alvinr/tbs/fp-corner-blueprint-spec.md

<!-- SPDX-License-Identifier: AGPL-3.0-only -->
<!-- © 2026 Alvin Richards -->
<!-- Design spec / scope — NOT a published TBS artifact (not registered in publish.sh). -->

# Film-Plane Corner Mechanism — Definitive Blueprint Spec

**Status:** scoped, awaiting sign-off before implementation.
**Purpose:** upgrade ONE film-plane corner from arrangement-schematic to a **dimensionally-exact,
fabricator-ready** drawing — the **template** for rolling the same standard across every subsystem
(water/tray, IBC frame, walkway, hinged panel, light lock, electrical, optics).

## Locked decisions (2026-08-10)

1. **Upgrade the existing corner sheets 3/4/8/9 in place** (in `generate_film_plane_mechanism.py`)
   + add a new **guide-corner sheet**. No separate generator.
2. **Cover both corners**: bottom = **weight** corner (rail web-vertical, skate load-bearing);
   top = **guide** corner (rail flat, skate as guide only) — the mirror pair.
3. **304 stainless** for the cross-slide bar + skate axle (procurement BOM is source of record; the
   cyanotype wash is chloride-free). Fix the stale **316** references.

## Design of record (one corner)

| Element | Spec | Finish |
|---|---|---|
| Depth rail | 3×1½" (76×38) **6061-T6 Al U-channel**, 8 ft (Grainger 795M51) | mill |
| Carriage | 4-wheel **acetal skate** — Ø32 load + Ø20 keeper rollers on Ø10 **304** axles + fab carriage plate | — |
| Cam clamp | 3/corner McMaster **5128A63** low-profile hold-down toggle | zinc |
| Z + X cross-slide | **304** flat-bar ¼"×1½" (6.35×38.1) on UHMW pad + brass-tip gib | — |
| U-joint | **Belden SSNBUJ750x3/8KB** (Grainger 41D816; 3/8" keyway bore + set screw, 0.75" OD, 45°, needle-bearing, factory-booted); input stub in McMaster **4040N12** 304 shaft support; keyed 3/8" 304 stub | stainless |
| Corner plate | ¼" **304 SS** 6×8" blank, press-brake **L-bracket** | 304 |
| Frame angle | 2×2×⅛" **6061-Al** angle, welded rigid rectangle 4,389×2,094 | mill |

_(The TODO's "Ruland US12-6-6-SS" is stale — the U-joint was changed to Belden. "Wheels/trolley on
316 pipe" is a superseded concept — the built design is the U-channel + acetal skate.)_

## Phase 1 — Reconcile + parametrize (precondition; no drawing yet)

**1a. Resolve conflicts (drift sweep):**
- Cross-slide bar + skate axle **316 → 304** in: `film-plane-mechanism-report.md` §4, `generate_film_plane_mechanism.py` Sheet-8 note, `component-dependency-map.md` §3.1/§1.3 and the FPM note.
- Rail **material** in depmap "304 U-channel" → **6061-Al**; rail **supplier** stale "McMaster 1262T21" → **Grainger 795M51** (depmap §1.3 + 2D generator comment).
- Rail **scheme**: adopt the 3D model's **two-orientation** build as the design of record (bottom web-vertical weight / top flat guide); fix the report/parts "uniform, one skate rides inside each" wording; drop stale "4×2" / "V-trolley" / "trolley" comments in constants + model.

**1b. Promote/add constants to `tbs_constants.py`** (so the drawing is parametric, can't drift):
- Promote `XSLIDE_Z_TRAVEL` / `XSLIDE_X_TRAVEL` / `XSLIDE_STROKE` / `XSLIDE_N` from **`reserved` → firm**. **FIRM (2026-08-13):** travel verified vs geometry on Sheet 10 — Z = (FP_H/2)(1−cos 40°) = 245 mm, X = (FP_W/2)(1−cos 28°) = 257 mm (exact match).
- **New:** `XSLIDE_BAR_W=38.1`, `XSLIDE_BAR_T=6.35` (cross-slide bar section); `XSLIDE_UHMW_T`, `XSLIDE_GIB_*`.
- **New:** `UJOINT_BORE=9.53`, `UJOINT_OD=19.05`, `UJOINT_ANGLE=45`, `UJOINT_LEN` (from the Belden datasheet).
- **New:** `SKATE_ROLLER_OD=32`, `SKATE_KEEPER_OD=20`, `SKATE_AXLE_OD=10`, skate roller spacing / carriage-plate W×H×T.
- **New:** `CORNER_PLATE_W=203.2`, `CORNER_PLATE_H=152.4`, `CORNER_PLATE_T=6.35`, bend line + leg lengths.
- **New:** hole **PCDs / edge distances** — see Phase 2 (designed, then captured as constants).

**1c. Firm the load — DONE (2026-08-13; `fp_corner_load.py` → Sheet 10).** Per-corner load = W/4 = **124 N**
(moving mass ~51 kg, weight model). Governing case = the horizontal X (swing) slide in bending at full
257 mm extension (the Z slide takes gravity axially, so it doesn't bend). **DECISION: the
cross-slide bars are mounted DEEP** — the 38.1 mm dimension in the load direction — giving σ ≈ 21 MPa,
**SF ≈ 10**, δ ≈ 0.1 mm. Flat mounting is marginal (SF ≈ 1.7, fails under a 2× dynamic/asymmetry factor)
and is NOT used. See Sheet 10 (`film-plane-sheet10.png`).

## Phase 2 — Dimensioned drawing upgrades

**Hole positions** — take fixed patterns from datasheets (4040N12 shaft support, 5128A63 cam-clamp
base, U-joint bore); **design** the patterns on our fab plates (carriage plate, L-plate, cross-slide
mounts) to ≥2×Ø edge distance, then capture all as constants (Phase 1b).

- **Sheet 3** (corner carriage detail) → add hole PCDs + edge distances for the skate rollers/axles,
  carriage plate, and U-channel capture; add datum flags; dimension roller spacing.
- **Sheet 4** (rail mounting + transport drop-in) → dimension the rail-end mount, the transport
  drop-in bridge, and the right-flange bolt pattern (PCD/edge distance).
- **Sheet 8** (frame-corner ↔ cross-slide + J1–J5) → dimension the cross-slide **bar section + travel
  + gib/UHMW**; complete J1–J5 (below).
- **Sheet 9** (frame + ACM ↔ U-joint ↔ X-slide) → make it a **dimensioned fabrication section**;
  add the **U-joint envelope** and the **L-plate bend** (bend line, radius, leg lengths, PCDs).
- **NEW Sheet 10** (guide/top corner) → the mirror: rail laid flat, skate as guide (no load path),
  same cross-slide/U-joint stack — call out only the **deltas** from the weight corner.

## Phase 3 — Fastener schedule (complete J1–J5)

Existing J1–J5 (Sheet 8) carry size/thread only. Add per joint: **thread pitch + class**, **torque**
(from the fastener's proof load), **washer** (flat/split), and **thread-locker** (Loctite grade) callout.
- J1/J2 = M8 (carriage/plate); J3 = 3/8" stub → U-joint (key + clamp); J4 = shaft-support setscrew;
  J5 = M6 legs tapped into the frame angle. Verify each against its datasheet.

## Phase 4 — Datum + tolerance scheme

Establish a datum reference frame for the corner (e.g. **A** = frame-angle mounting face, **B** = rail
web, **C** = optical axis) and apply position/parallelism tolerances to the critical features
(cross-slide travel squareness, U-joint bore concentricity, rail capture). Add a title-block tolerance
block (general ±, then per-feature GD&T where it matters).

## Phase 5 — Cascade + close

- Reconcile `parts.py` / `costing.py` / report §7 / master BOM to any spec change (304 confirm = no
  cost move; new constants = no cost move).
- Re-send the `film-plane-mechanism.skp` model so its (currently hardcoded) corner geometry reads the
  new constants; reconcile depmap §3.1.
- Run the gates (`lint.py`, `check_consistency.py`), gallery + registration for the new Sheet 10.
- Tick the milestone sub-items in `TODO.md`; RELEASE `[Unreleased]`.

## Acceptance criteria

A fabricator can build one weight corner **and** one guide corner from Sheets 3/4/8/9/10 alone:
every hole located (PCD/edge distance), every fastener called out (size/thread/torque/locker), every
part's material + finish stated, sections dimensioned, and a datum/tolerance scheme present — all driven
from `tbs_constants` with **zero** `reserved`/prose-only corner dimensions remaining.

## Guide (top) corner — web-vertical decision + FP_H reconciliation (VERIFIED 2026-08-10)

**Decision:** the top (guide) corner uses the **same web-vertical rail + captured skate** as
the bottom (weight) corner — NOT the flat "inverted-U, wheels-under-web" build the 3D model currently
has. Rationale: the wheels-under-web build is unsound (gravity drops the hanging carriage away from the
rollers); a captured skate on a web-vertical rail holds the corner regardless of load direction (it
reacts the plane's tip-force, not gravity). The transport swing does not constrain this — the left rails
are transport drop-ins (removed for the ~56° swing; door clearance `SWUNG_DOOR_CLEARANCE_MM`=29mm is
unaffected).

**The old Sheet 10 was reverted** (commit on this branch): its wheels-under-web section was wrong and it
added nothing over Sheet 3 but a deltas note.

**FP_H reconciliation — the key result: NO `FP_H` change, NO headline cascade.** The flat top rail was
letting the 3D model draw the film ~36 mm *taller* than the official constant ever claimed — a latent
inconsistency. Web-vertical corrects the model *down to* the constant. Verified against the LIVE model
(`film-plane-mechanism.skp`, read-only eval), all mm:

| | film bottom | film top | FP height | top rail Z |
|---|---|---|---|---|
| **Constant** (`FP_H`) | 160 | 2254 | **2094** | — |
| **Model, flat top (now)** | 160 | **2290** | 2130 (outlier, +36) | 2300–2338 (38 tall, 50 below ceiling) |
| **Model, web-vertical** | 160 | **2252** | **2092** (≈ FP_H, −2) | 2262–2338 (76 tall, 50 below ceiling) |

Web-vertical film top = `C_HGT(2388) − rail(76) − ceiling_clear(50) − guide_gap(10) = 2252`; FP =
2252 − 160 = **2092 ≈ FP_H 2094** (2 mm, within rounding). So `FP_H` stays **2094**, `RAIL_OFF_TOP`
stays **144** — the model was the thing out of sync; web-vertical fixes it. (A separate ~10 mm internal
slack exists between `RAIL_OFF_TOP`→2244 and `FP_H`→2254; optional future cleanup, independent of this.)

**What the switch takes (no FP_H/optics/image-area/facts/CLAUDE.md churn):**
1. **3D model** `generate_film_plane_mechanism_model.py` — top rail flat→web-vertical (`CD_TOP/CW_TOP`
   orientation, `PZ_HB_TOP`, `GUIDE_GAP`, `guide_rail()` builder); the top skate becomes the SAME captured
   skate as the bottom; film top drops 2290→2252. Regenerate + **re-send** (needs the .skp open) + ALVIN saves.
2. **Docs/comments** — "top laid FLAT / inverted-U / wheels under web" → "top web-vertical, captured guide
   skate (rollers grip both flanges; reacts tip-force, not gravity)" in `component-dependency-map.md`,
   `film-plane-mechanism-report.md`, and the model comments.
3. **2D** — the guide-corner coverage folds into Sheet 3 as a captured-skate note (not a separate Sheet 10).
4. **No** `FP_H` change (verified), so no cascade to facts/optics/ACM/muslin/weight/CLAUDE.md.

## Open items to settle during design

- ~~Exact travel values for the promoted `XSLIDE_*`~~ **DONE 2026-08-13** — verified vs geometry (Sheet 10): Z 245 / X 257 mm.
- ~~Belden U-joint booted length + bolt/key detail~~ **DONE 2026-08-13.** Reviewed the plain `UJ-SS750x375` datasheet (`eng-specs/UJ-SS750x375__ZE41.pdf`) — OD 19.05 / length 68.3 / yoke 34.2 / hub 24.1 / 45° confirmed — but it has no keyway/set-screw, so **selected the retained variant: Belden SSNBUJ750x3/8KB (Grainger 41D816, $252.13 ea)** — 3/8″ **keyway bore (3/32×3/64 key) + set screw**, needle-bearing, stainless, 45° max, and **factory-booted** (integral bellows `UJOINT_BOOT_OD` 32.54 / `UJOINT_BOOT_LEN` 31.75 — no separate boot). Cascaded to constants / parts (fp-ujoint + fp-ujoint-key, boot line dropped) / costing (+~$403) / Sheets 3·8·9 / report. (3D model label re-send pending.)
- ~~Carriage-plate hole pattern~~ **DONE 2026-08-13** — plate firmed at **80×181×6mm 6061-T6** (`CARRIAGE_PLATE_*`, grown +10 for keeper edge distance); pattern **4× Ø10 stub-axle (40×38) + 4× M8 J1 + 2× M4 cam**, all ≥2×Ø from edges; drawn on Sheet 3 View A + firmed in `parts.py` fp-carriage-plate. (L-plate/corner-plate pattern already in `CORNER_PLATE_HOLE_*`.)
- ~~Per-corner load + cross-slide bending SF~~ **DONE 2026-08-13** (Sheet 10): 124 N/corner; bars mounted **DEEP** → SF ≈ 10 (flat 1.7, not used).
