alvinr/tbs/diagrams/container-floorplan.png

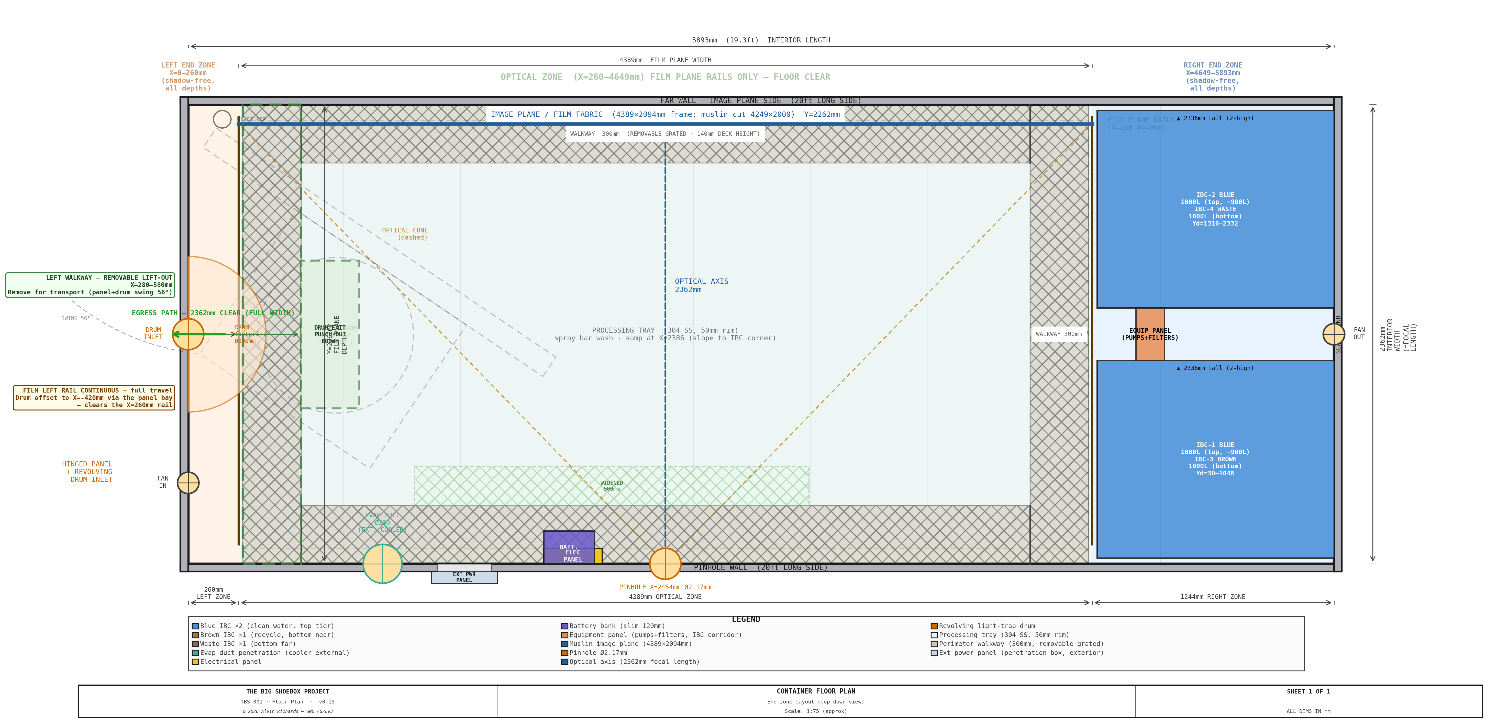
diagrams/container-floorplan.png
