alvinr/tbs/diagrams/electrical-sheet1.png

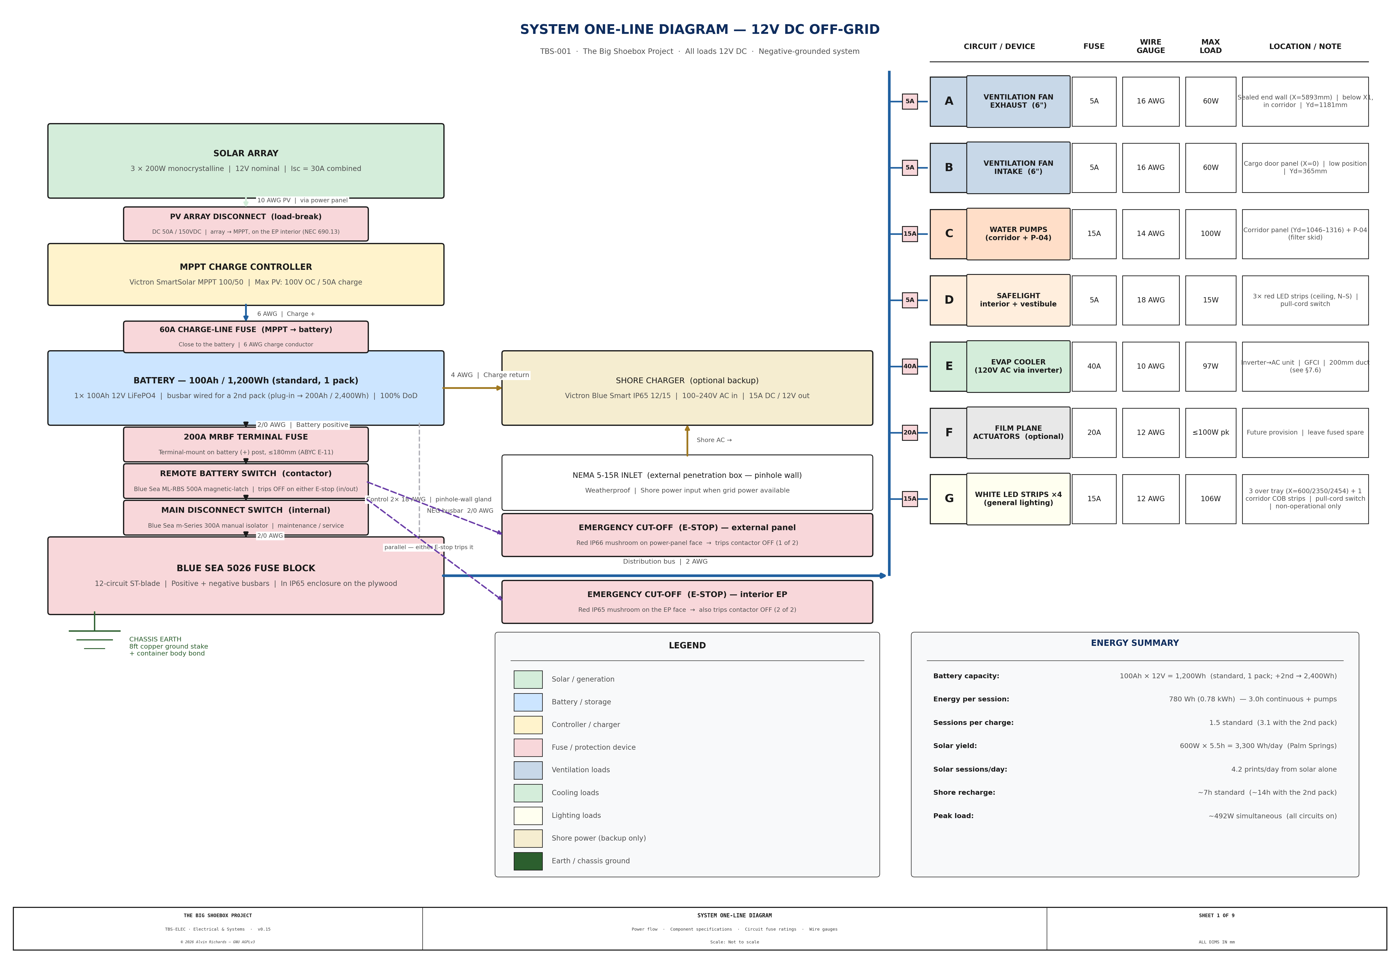
diagrams/electrical-sheet1.png
