alvinr/tbs/diagrams/electrical-sheet2.png

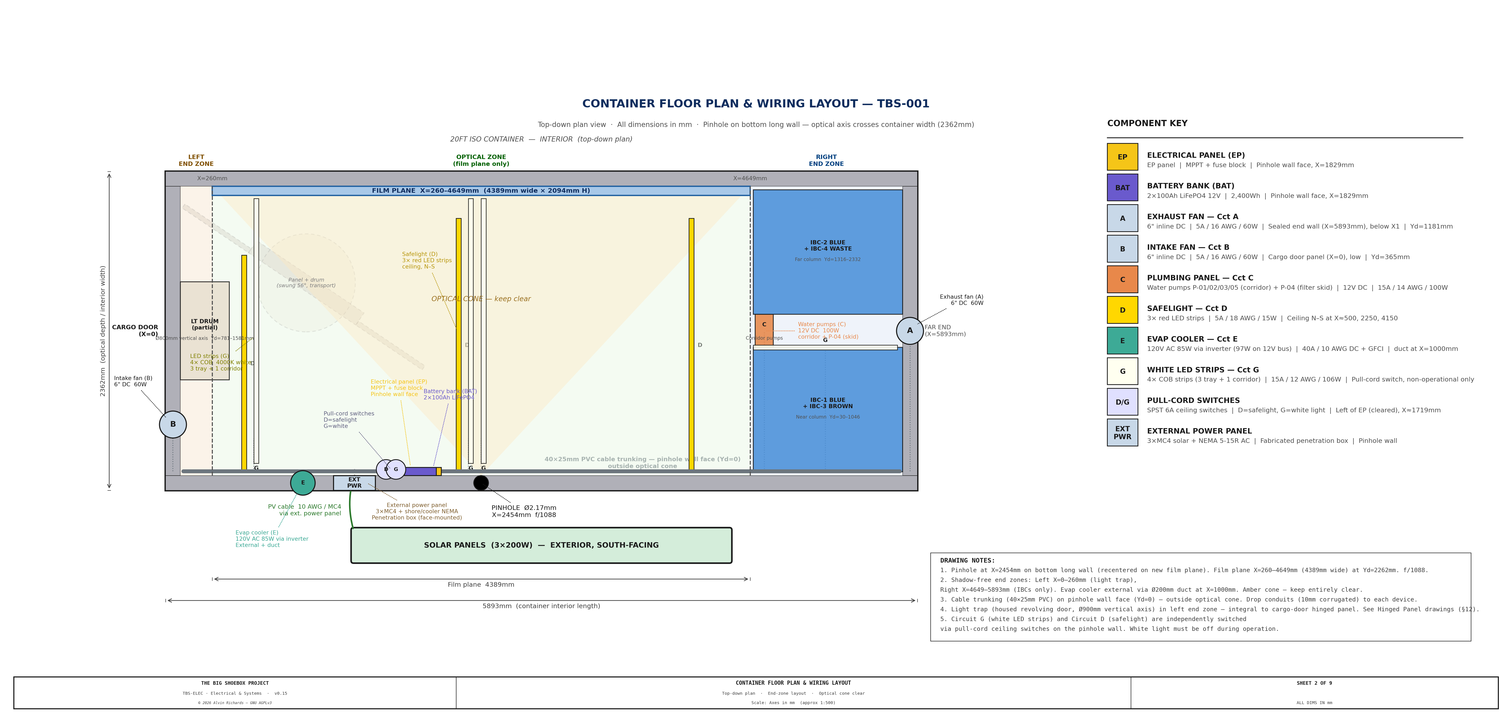
diagrams/electrical-sheet2.png
