alvinr/tbs/diagrams/film-joint-options.png

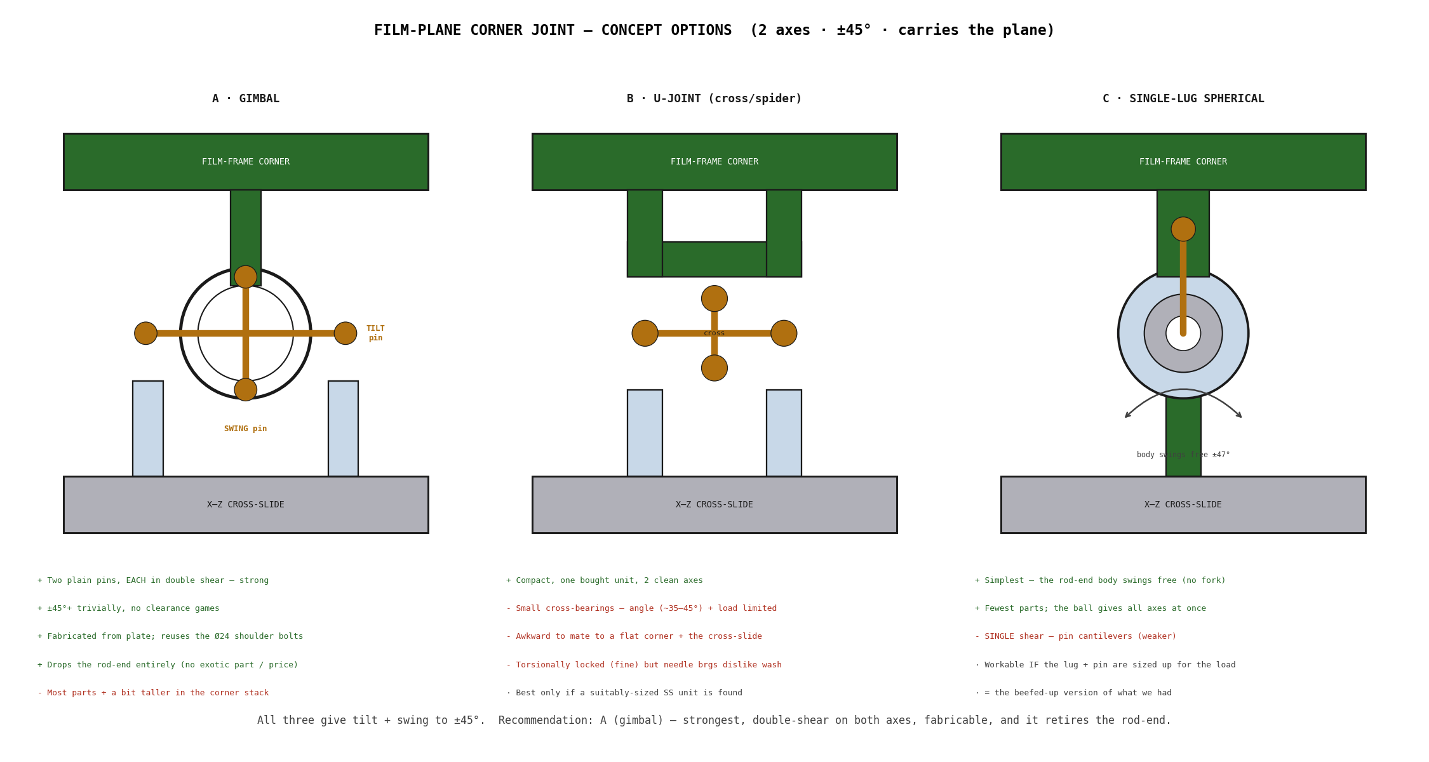
diagrams/film-joint-options.png
