alvinr/tbs/diagrams/film-joint-study-gimbal.png

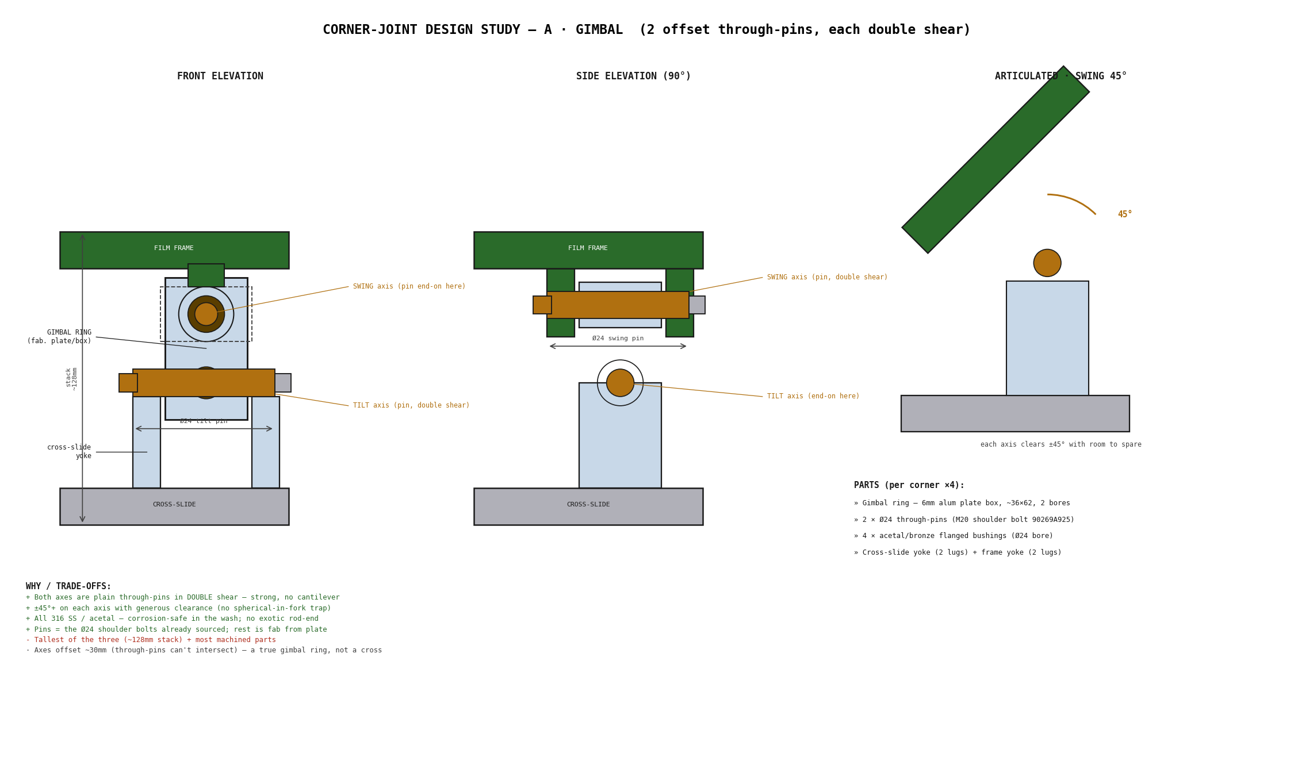
diagrams/film-joint-study-gimbal.png
