alvinr/tbs/diagrams/film-joint-study-ujoint.png

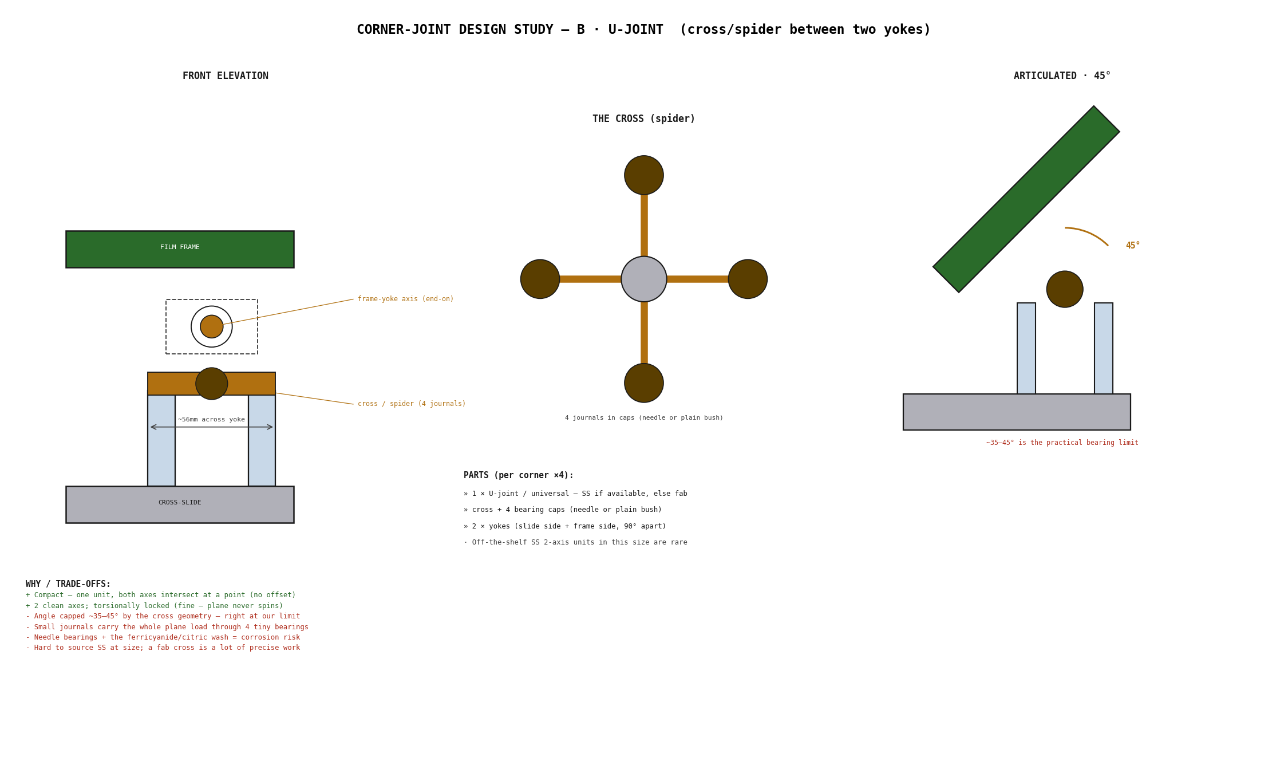
diagrams/film-joint-study-ujoint.png
