alvinr/tbs/diagrams/film-plane-distortion-c0.png

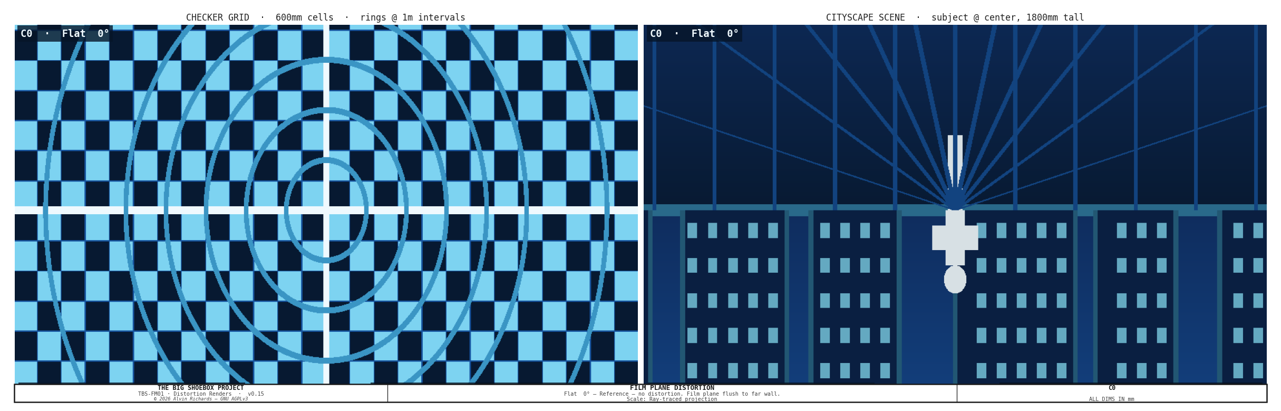
diagrams/film-plane-distortion-c0.png
