alvinr/tbs/diagrams/film-plane-distortion-c2.png

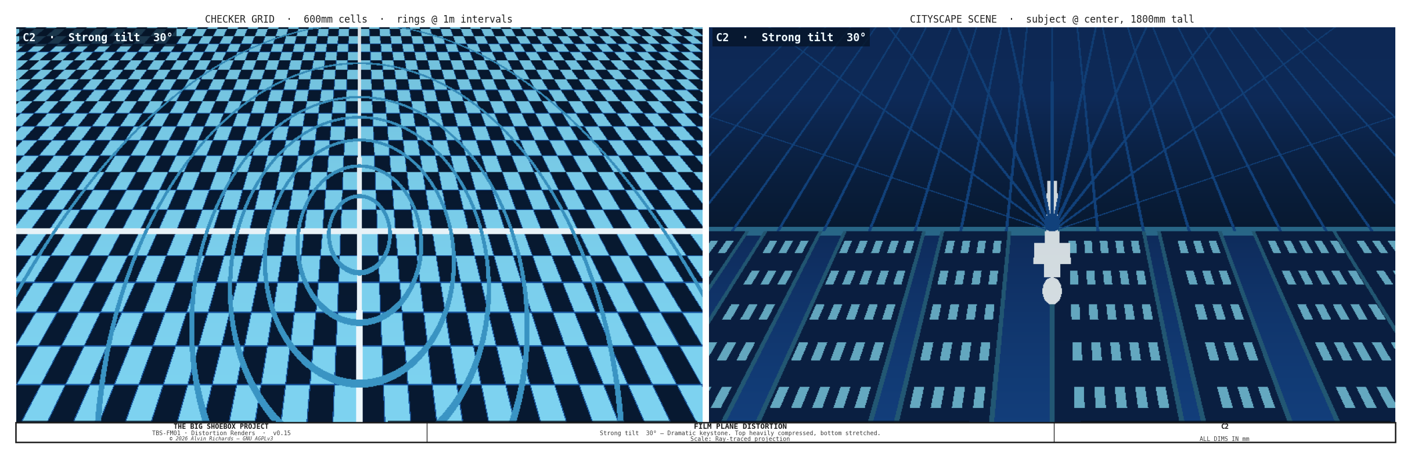
diagrams/film-plane-distortion-c2.png
