alvinr/tbs/diagrams/film-plane-distortion-c3.png

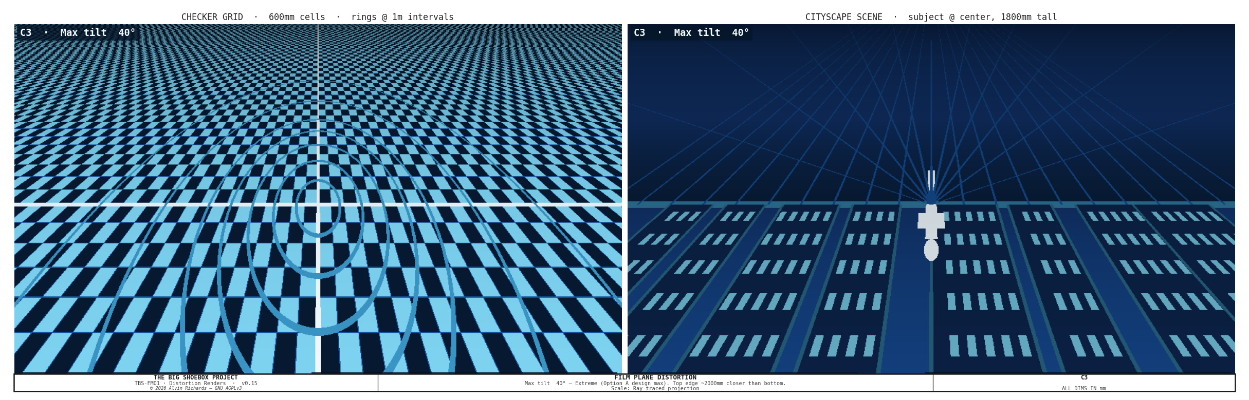
diagrams/film-plane-distortion-c3.png
