alvinr/tbs/diagrams/film-plane-distortion-c4.png

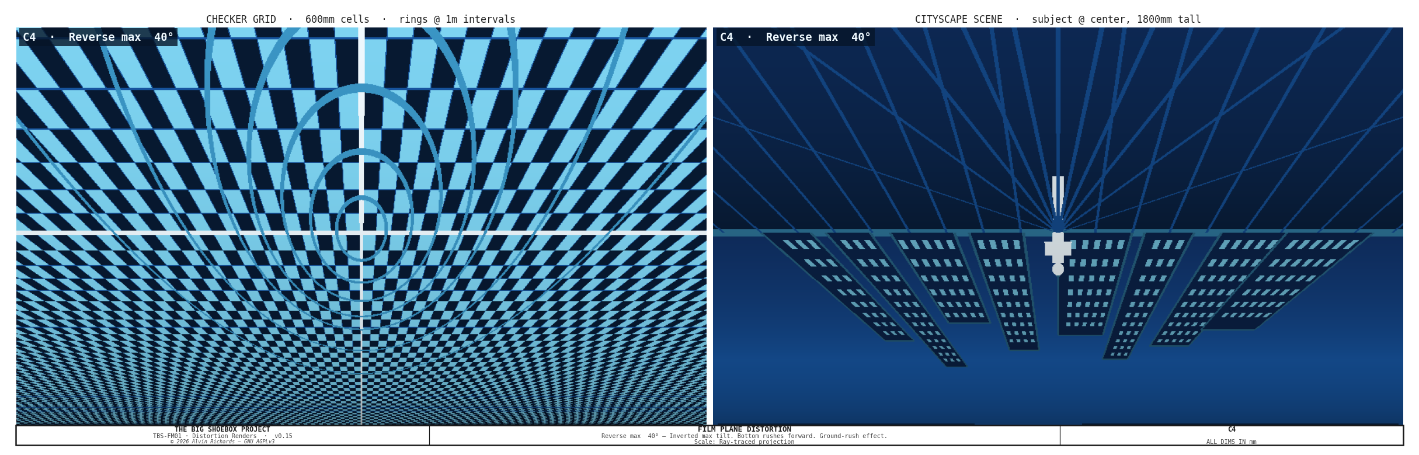
diagrams/film-plane-distortion-c4.png
