alvinr/tbs/diagrams/film-plane-distortion-c5.png

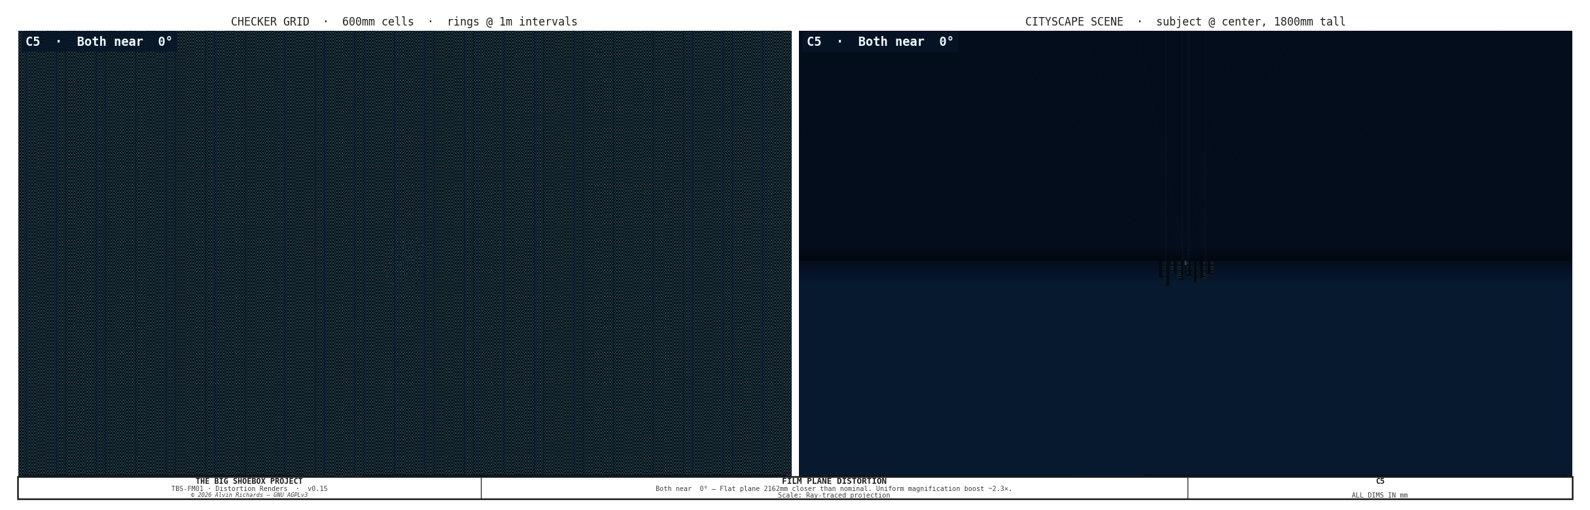
diagrams/film-plane-distortion-c5.png
