alvinr/tbs/diagrams/film-plane-distortion-summary.png

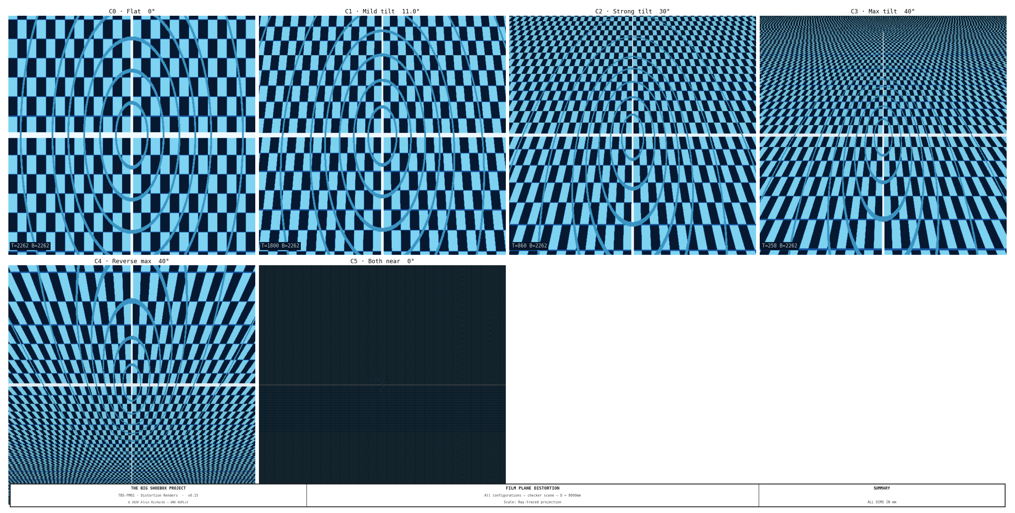
diagrams/film-plane-distortion-summary.png
