alvinr/tbs/diagrams/film-plane-sheet1.png

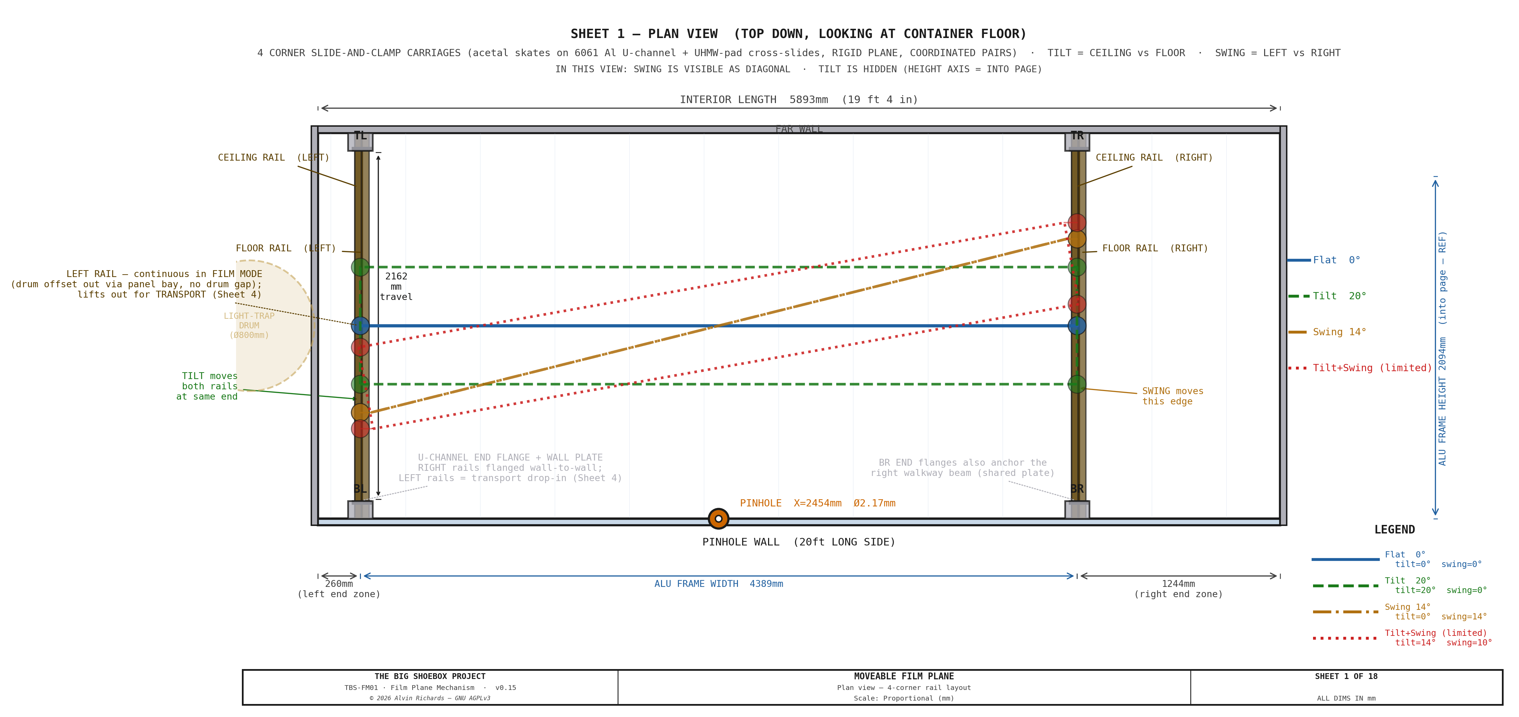
diagrams/film-plane-sheet1.png
