alvinr/tbs/diagrams/film-plane-sheet2.png

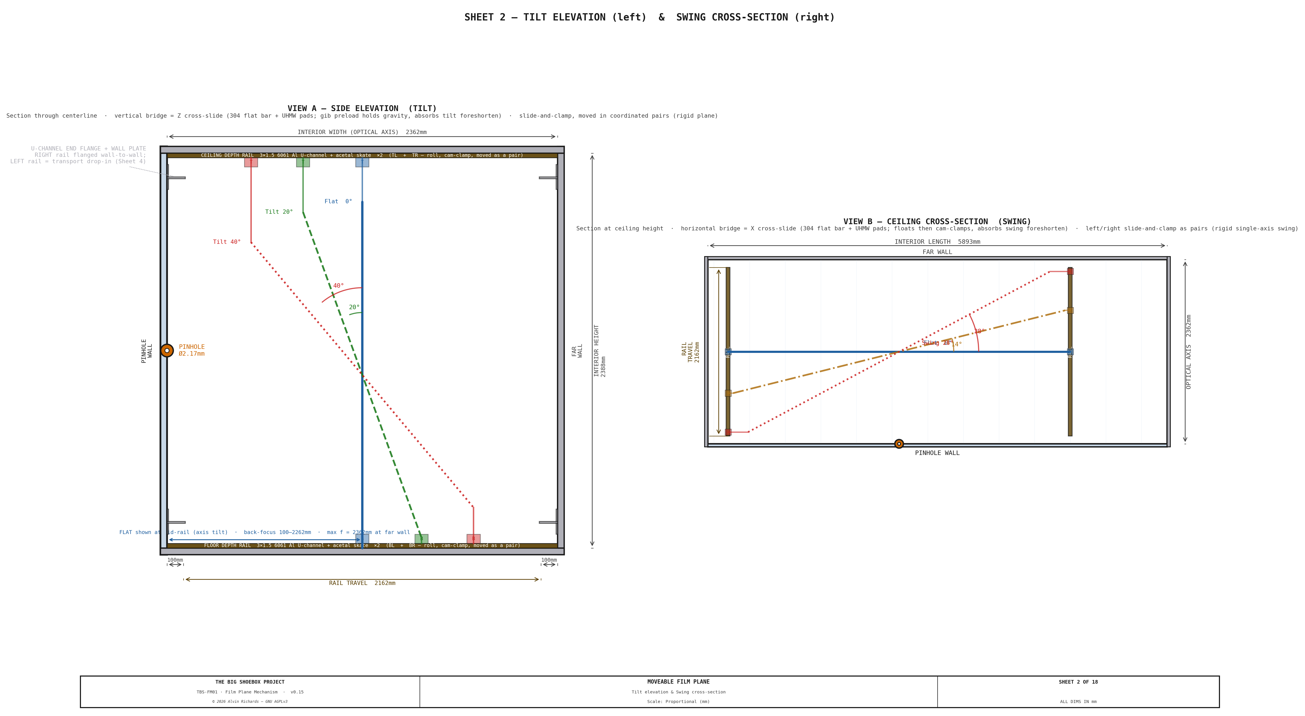
diagrams/film-plane-sheet2.png
