alvinr/tbs/diagrams/film-plane-sheet3.png

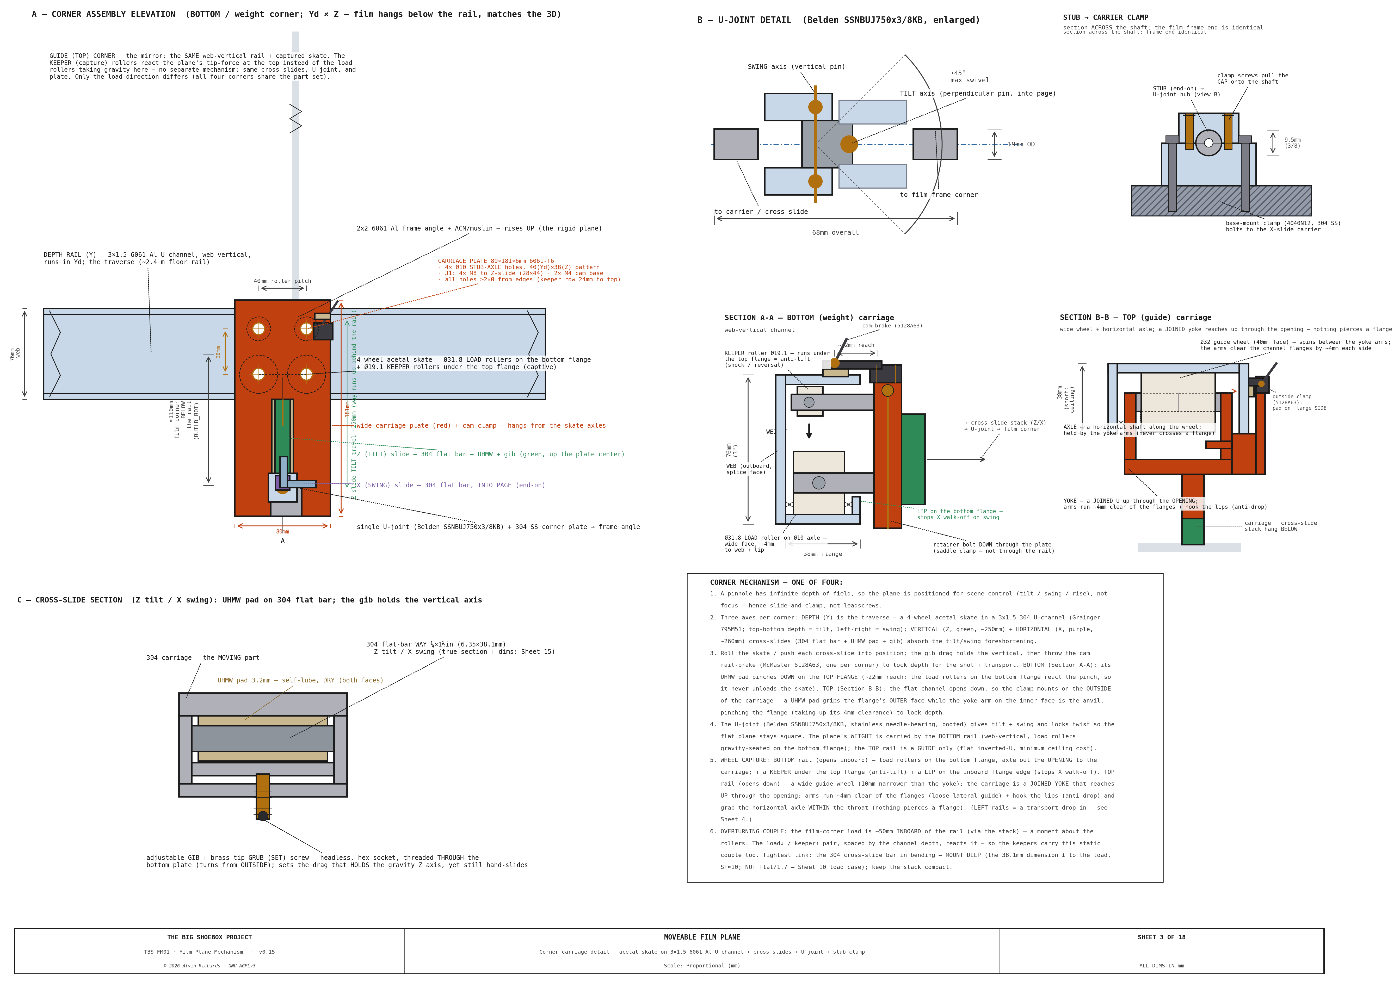
diagrams/film-plane-sheet3.png
