alvinr/tbs/diagrams/film-plane-sheet4.png

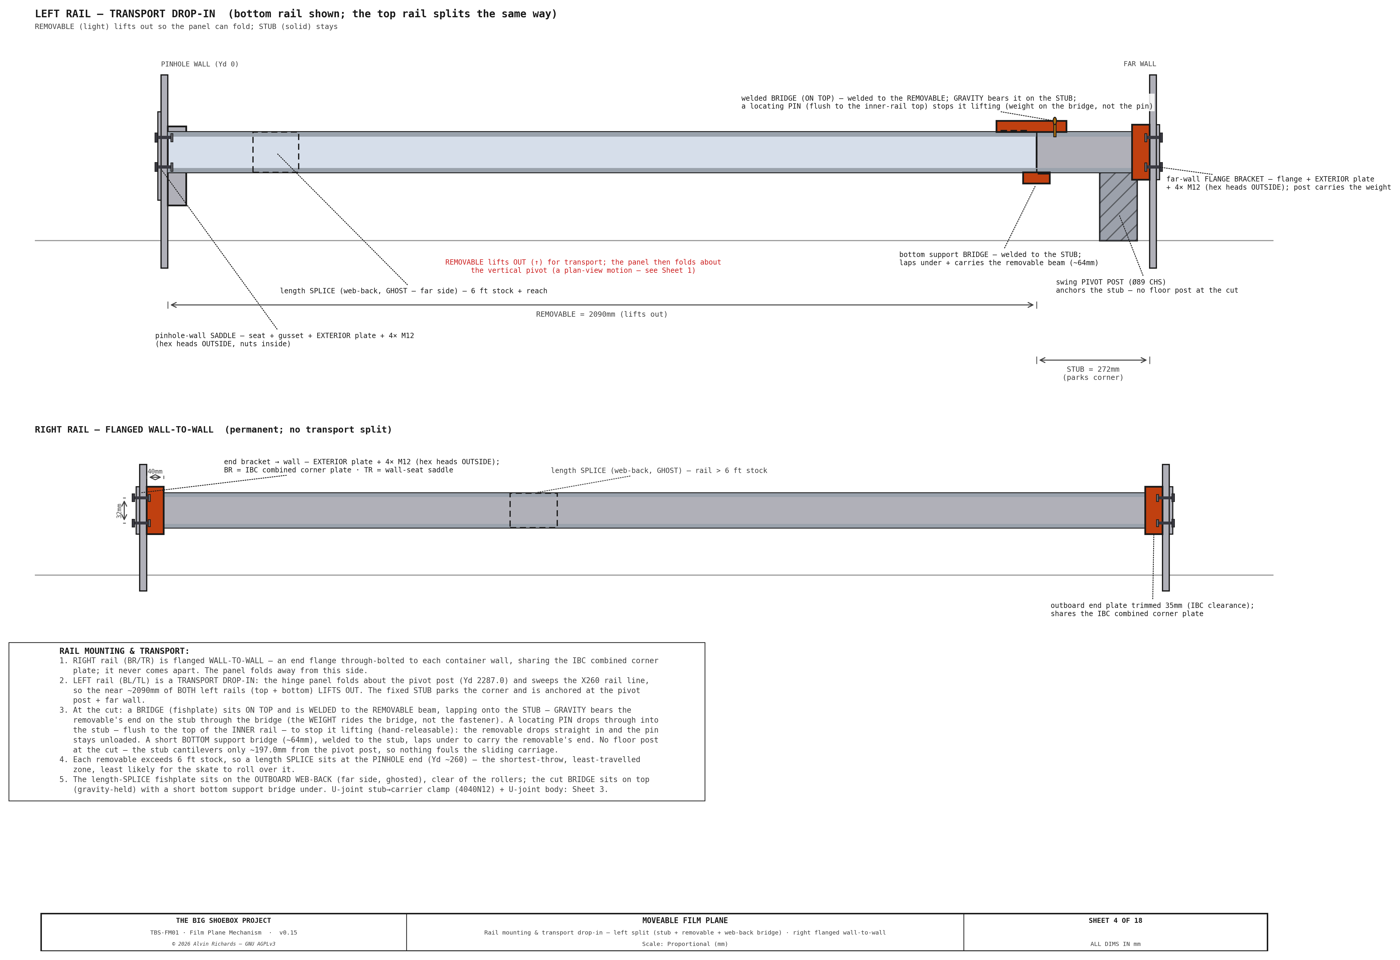
diagrams/film-plane-sheet4.png
