alvinr/tbs/diagrams/film-plane-sheet6.png

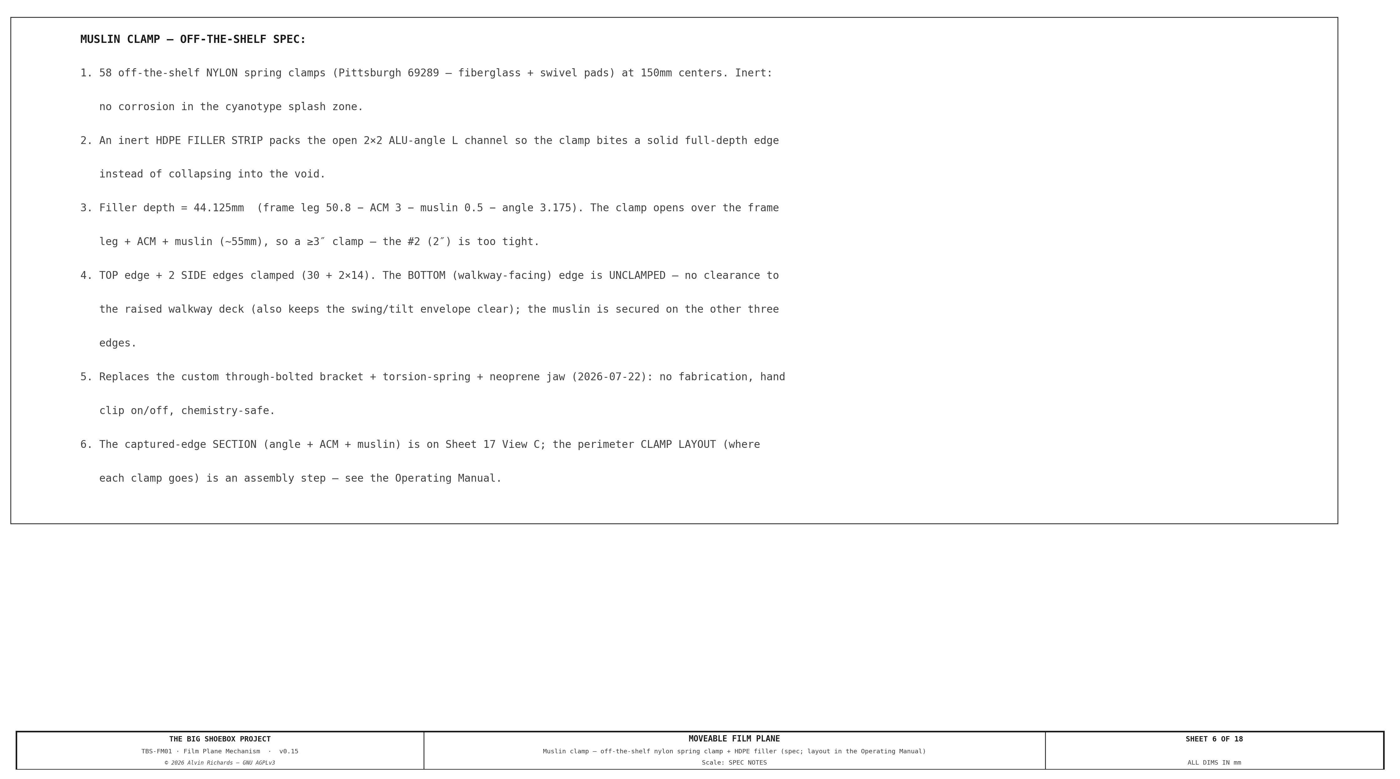
diagrams/film-plane-sheet6.png
