alvinr/tbs/diagrams/hingepanel-sheet1.png

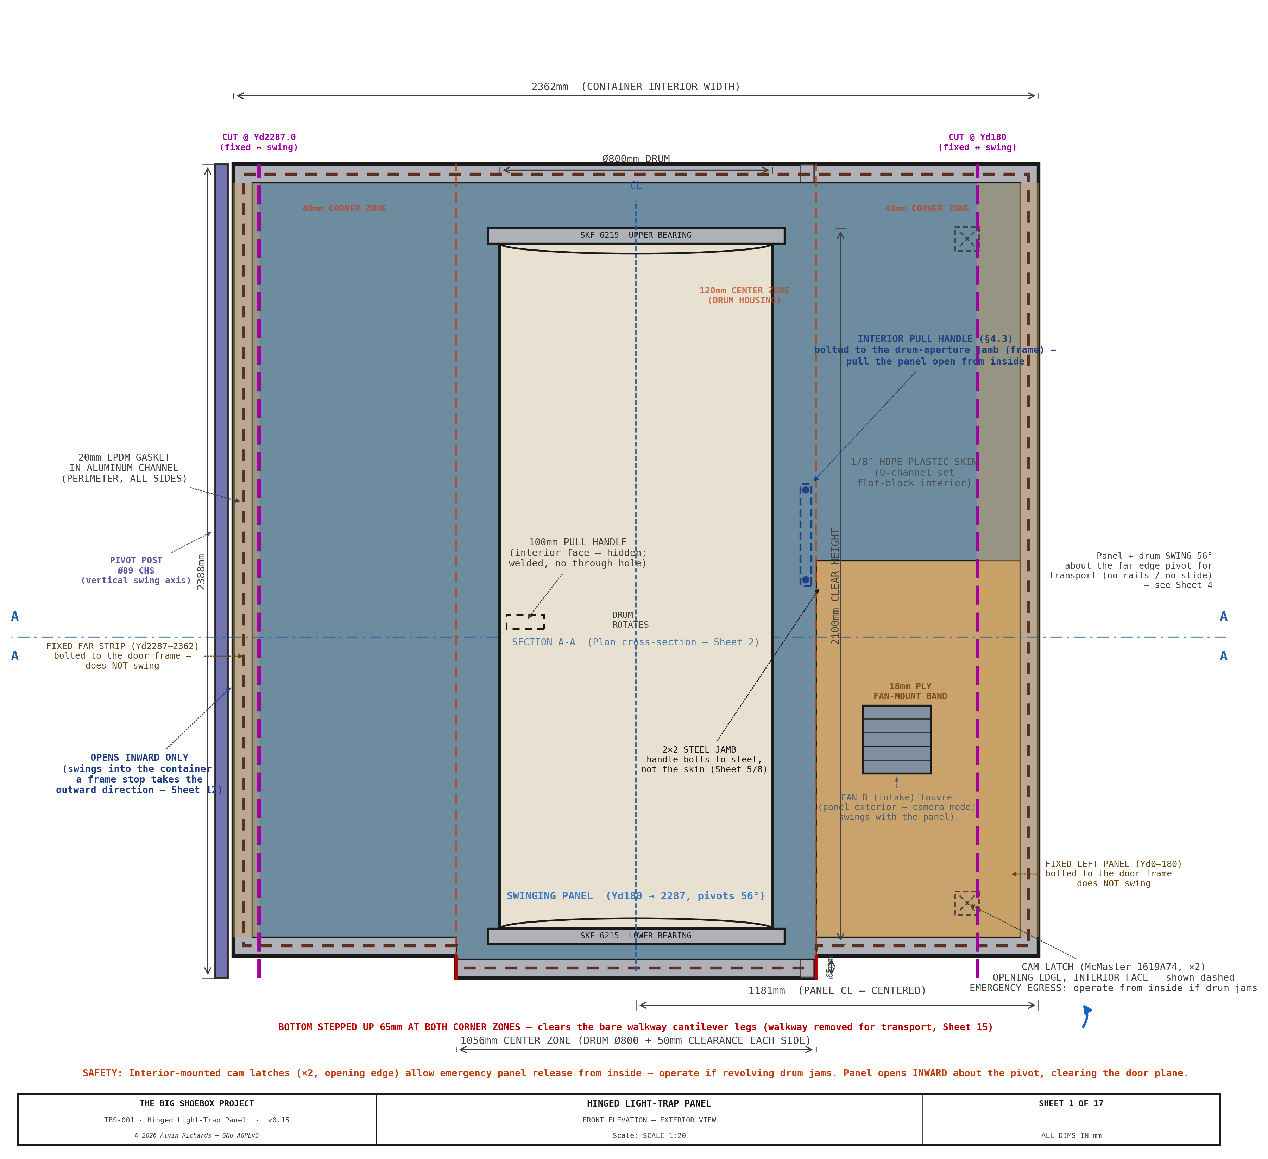
diagrams/hingepanel-sheet1.png
