alvinr/tbs/diagrams/hingepanel-sheet2.png

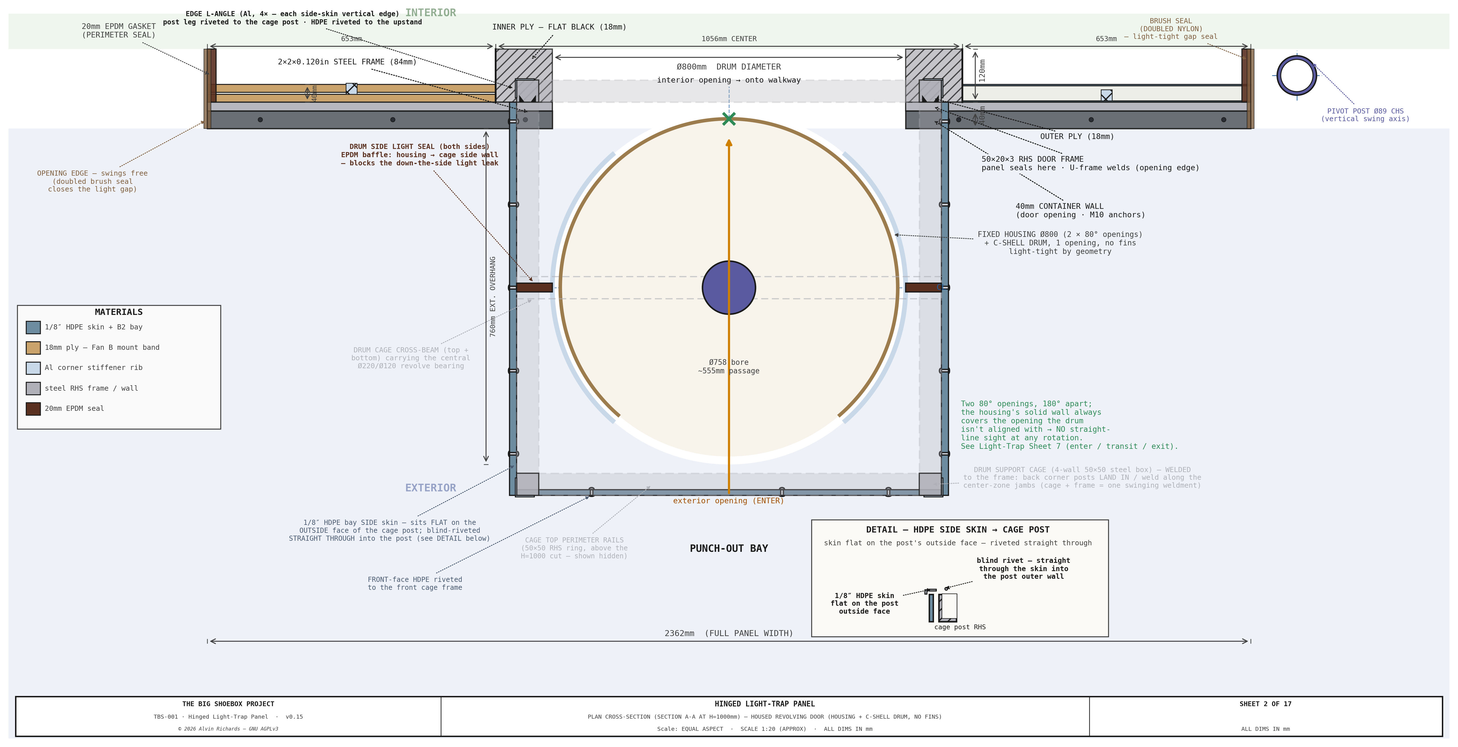
diagrams/hingepanel-sheet2.png
