alvinr/tbs/diagrams/hingepanel-sheet3.png

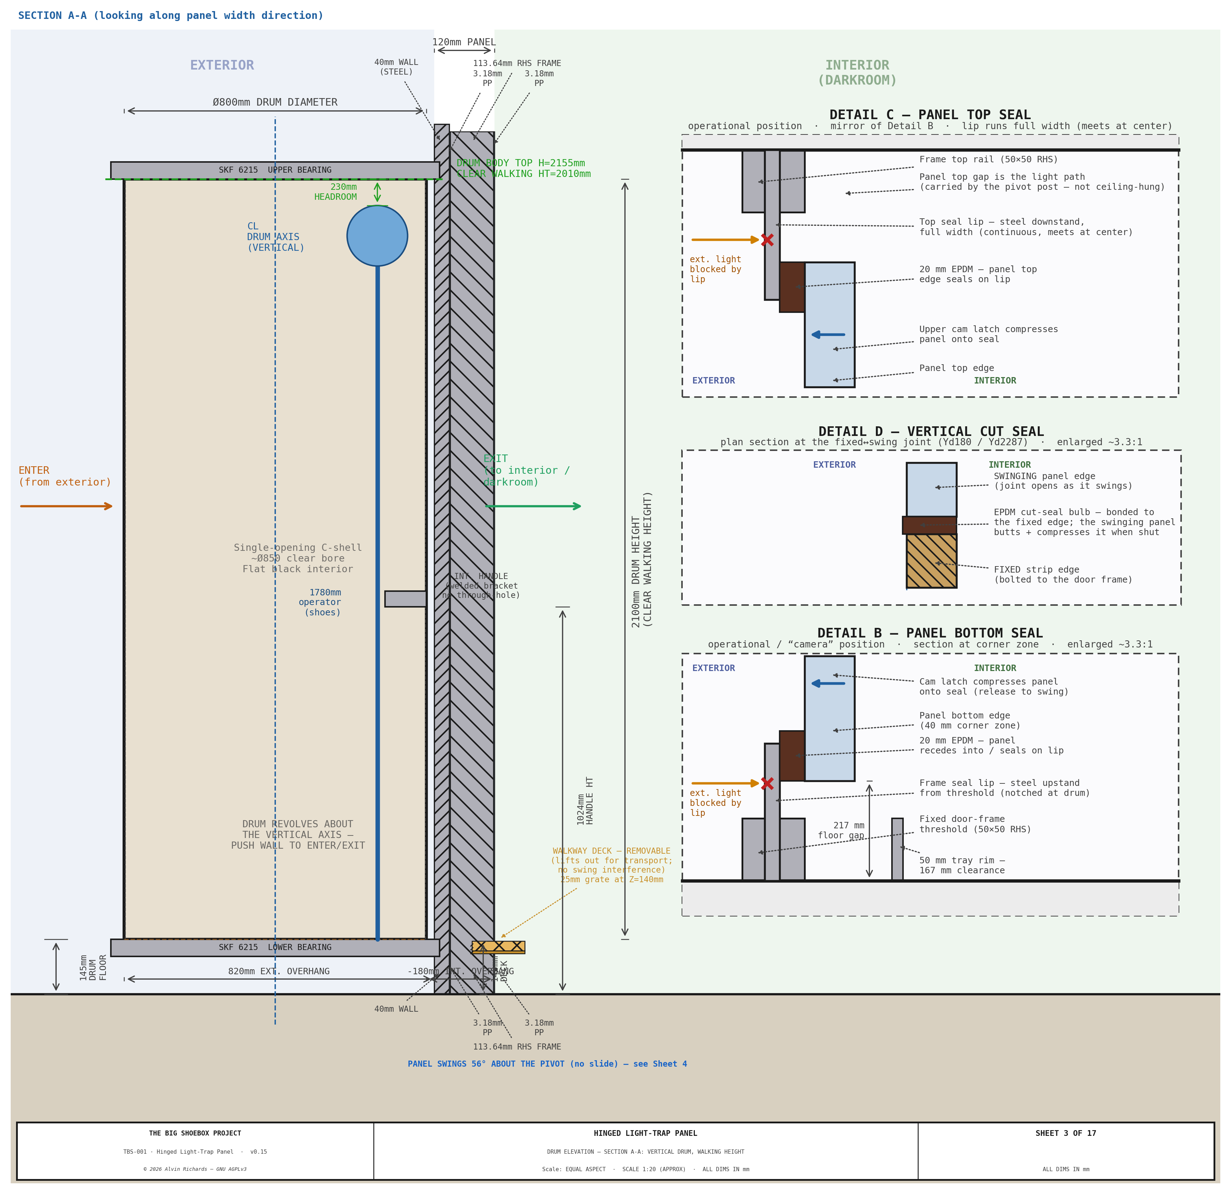
diagrams/hingepanel-sheet3.png
