alvinr/tbs/diagrams/lighttrap-sheet1.png

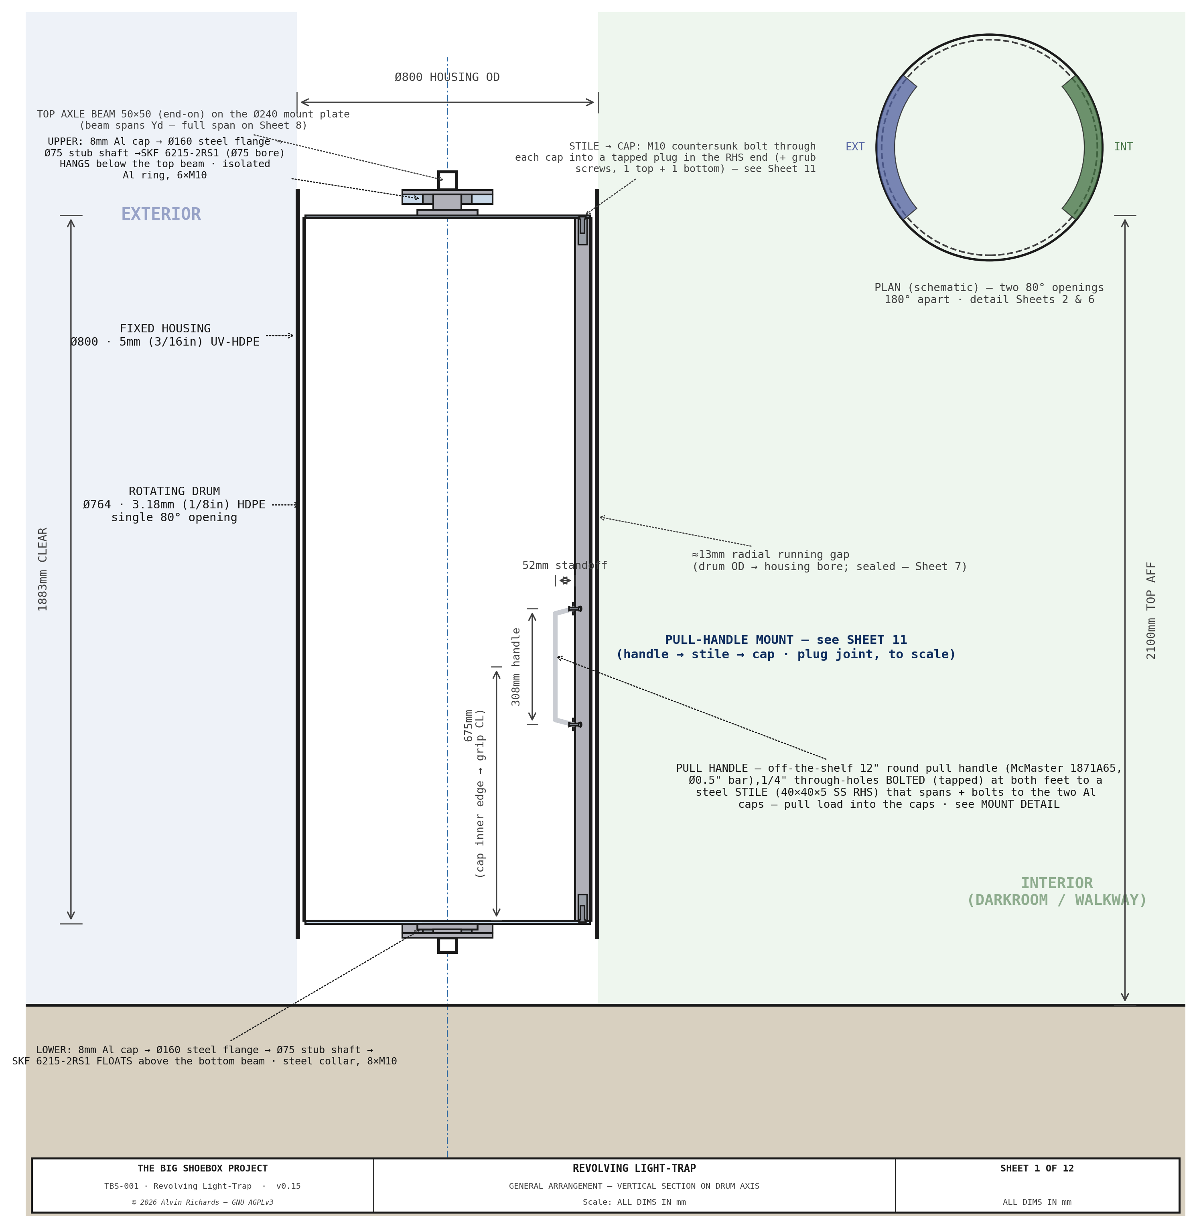
diagrams/lighttrap-sheet1.png
