alvinr/tbs/diagrams/lighttrap-sheet2.png

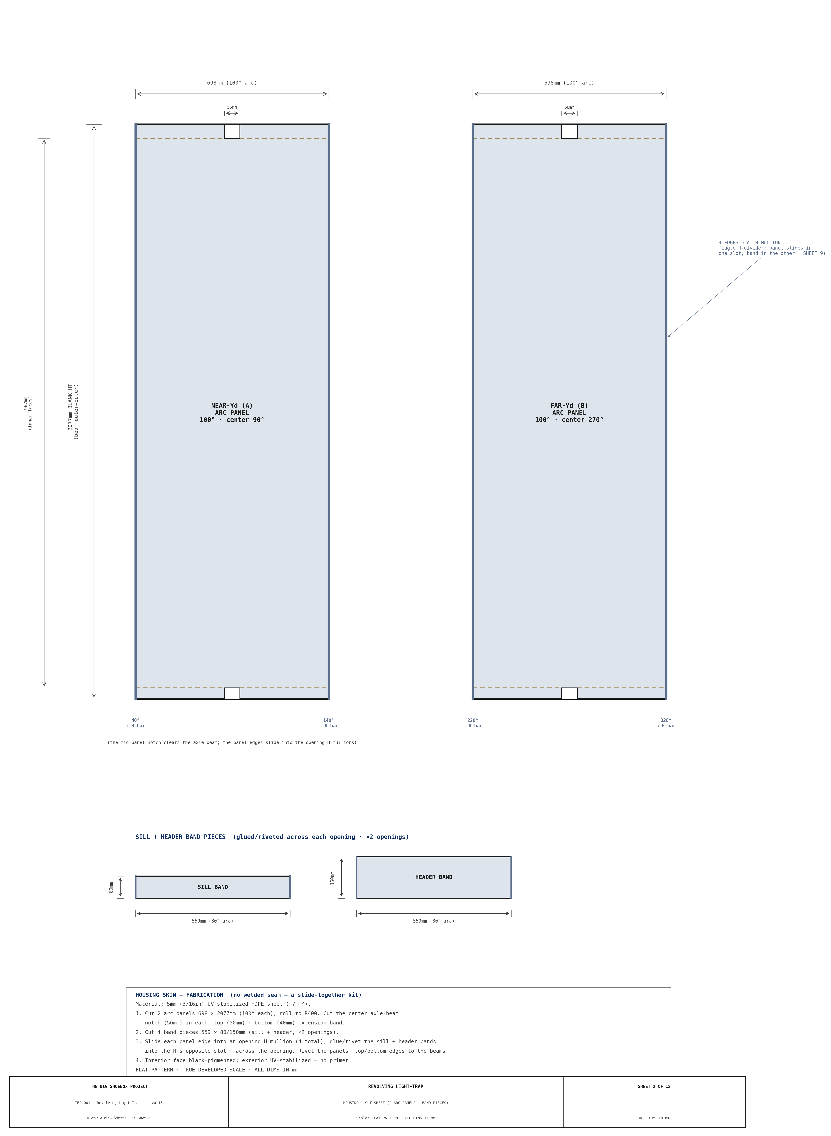
diagrams/lighttrap-sheet2.png
