alvinr/tbs/diagrams/lighttrap-sheet3.png

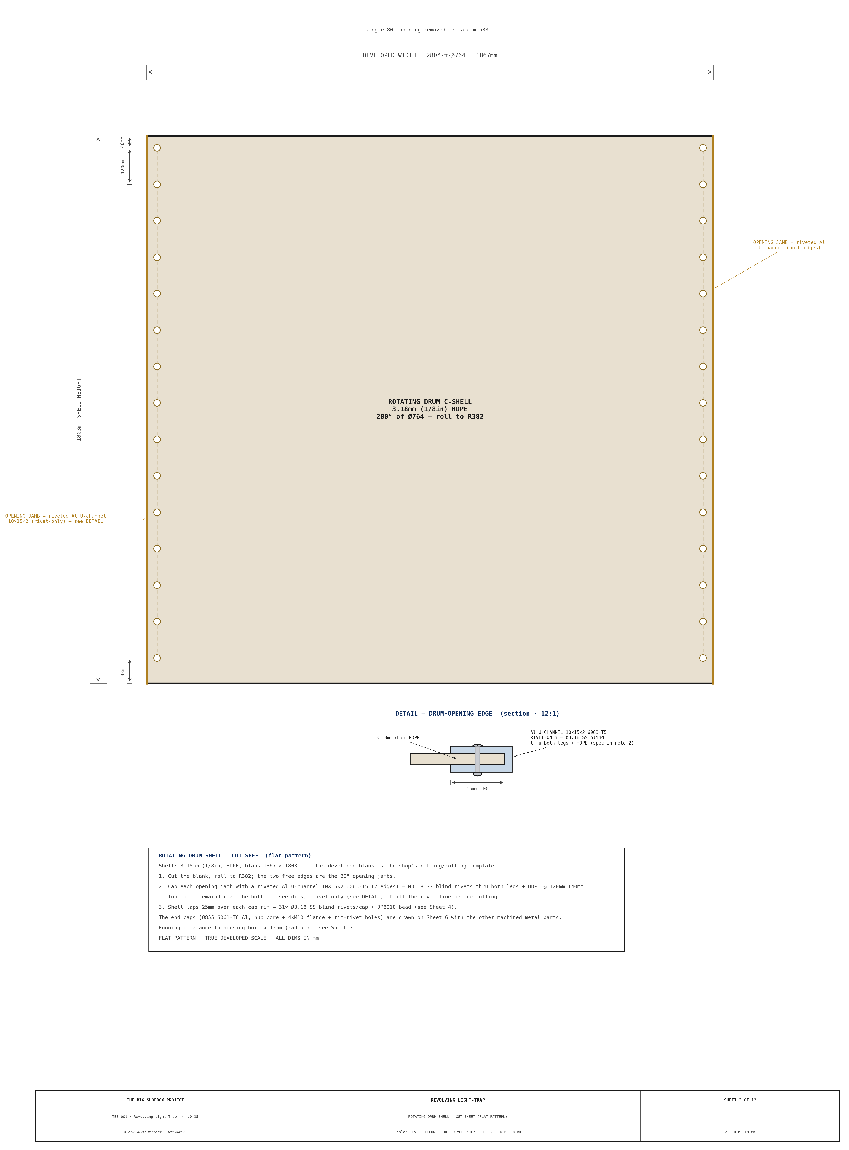
diagrams/lighttrap-sheet3.png
