alvinr/tbs/diagrams/lighttrap-sheet4.png

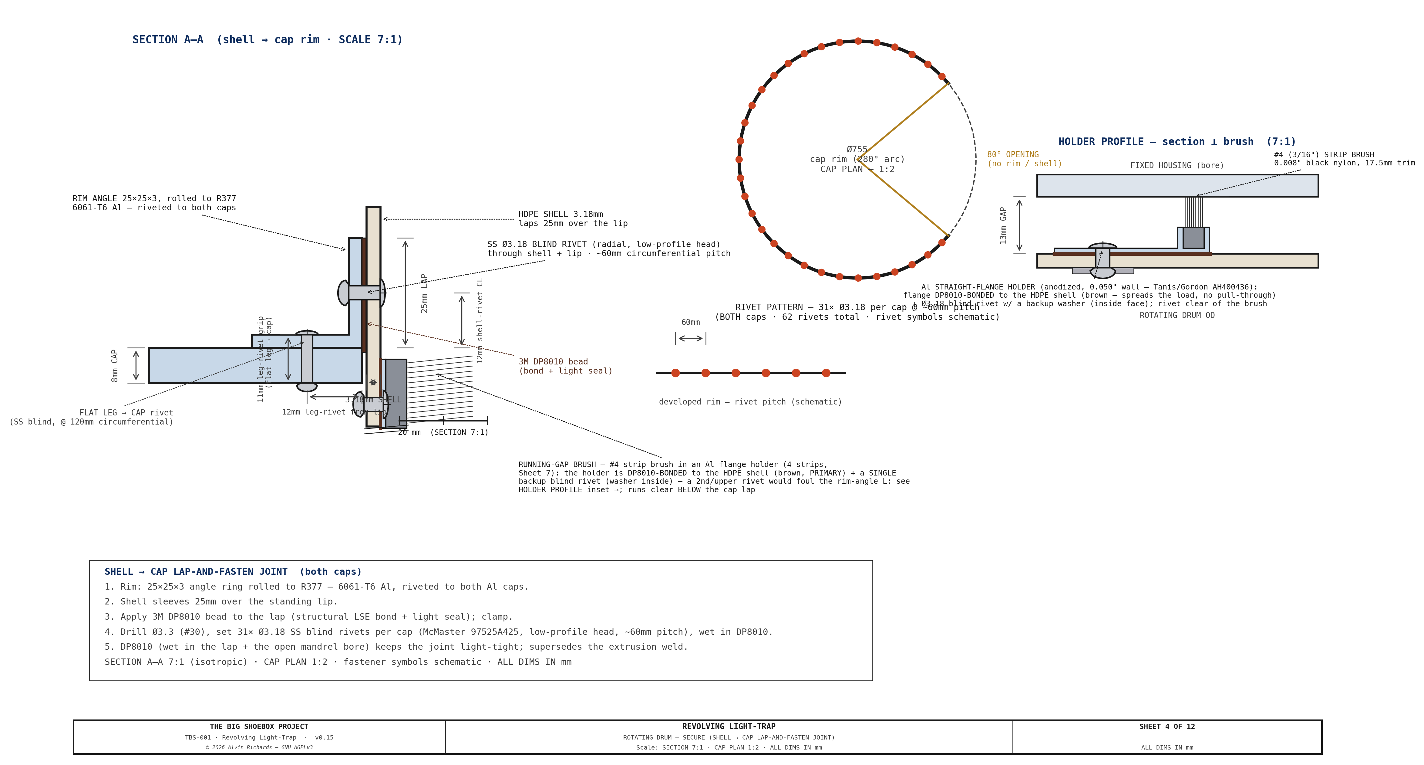
diagrams/lighttrap-sheet4.png
