alvinr/tbs/diagrams/lighttrap-sheet5.png

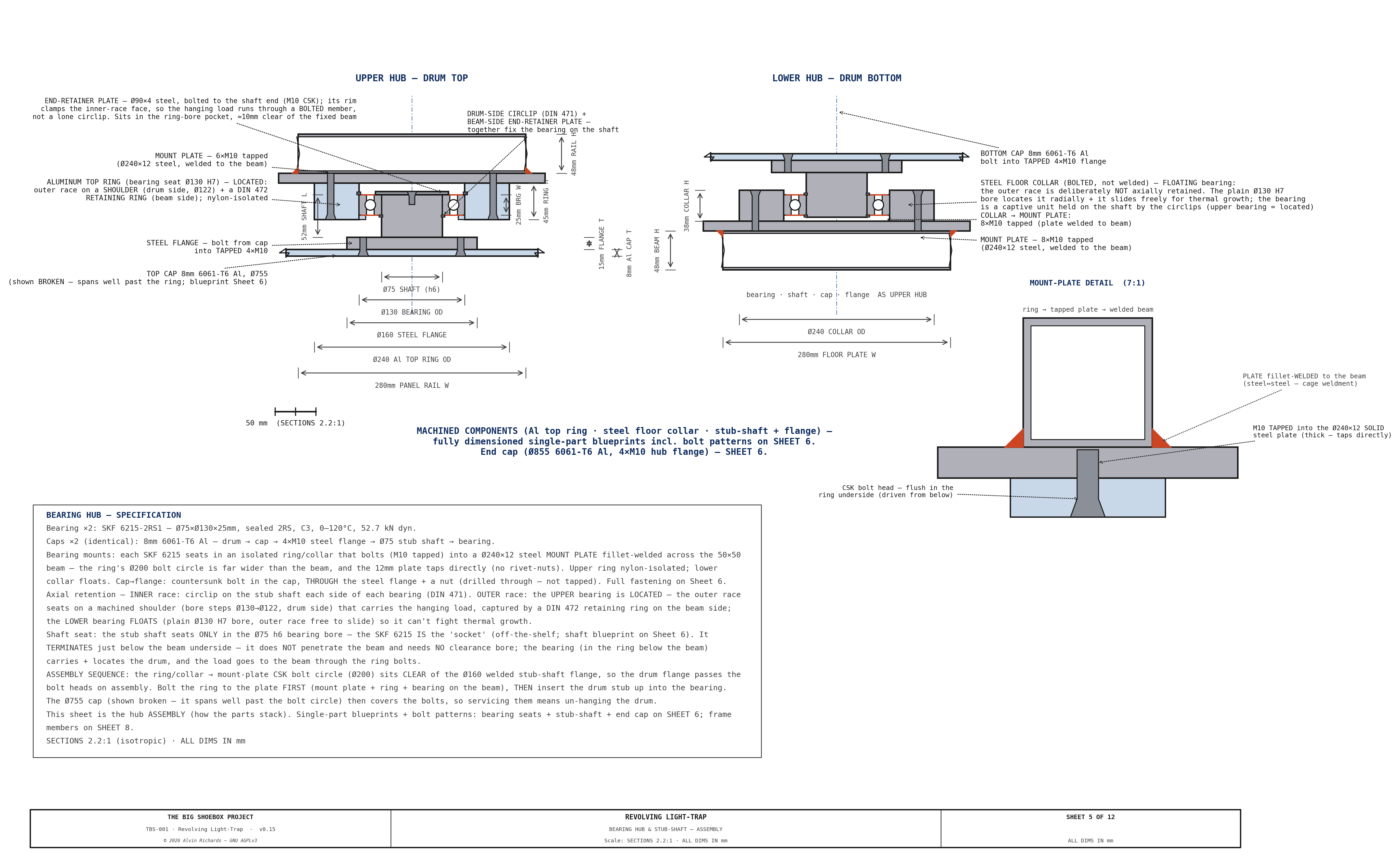
diagrams/lighttrap-sheet5.png
