alvinr/tbs/diagrams/lighttrap-sheet6.png

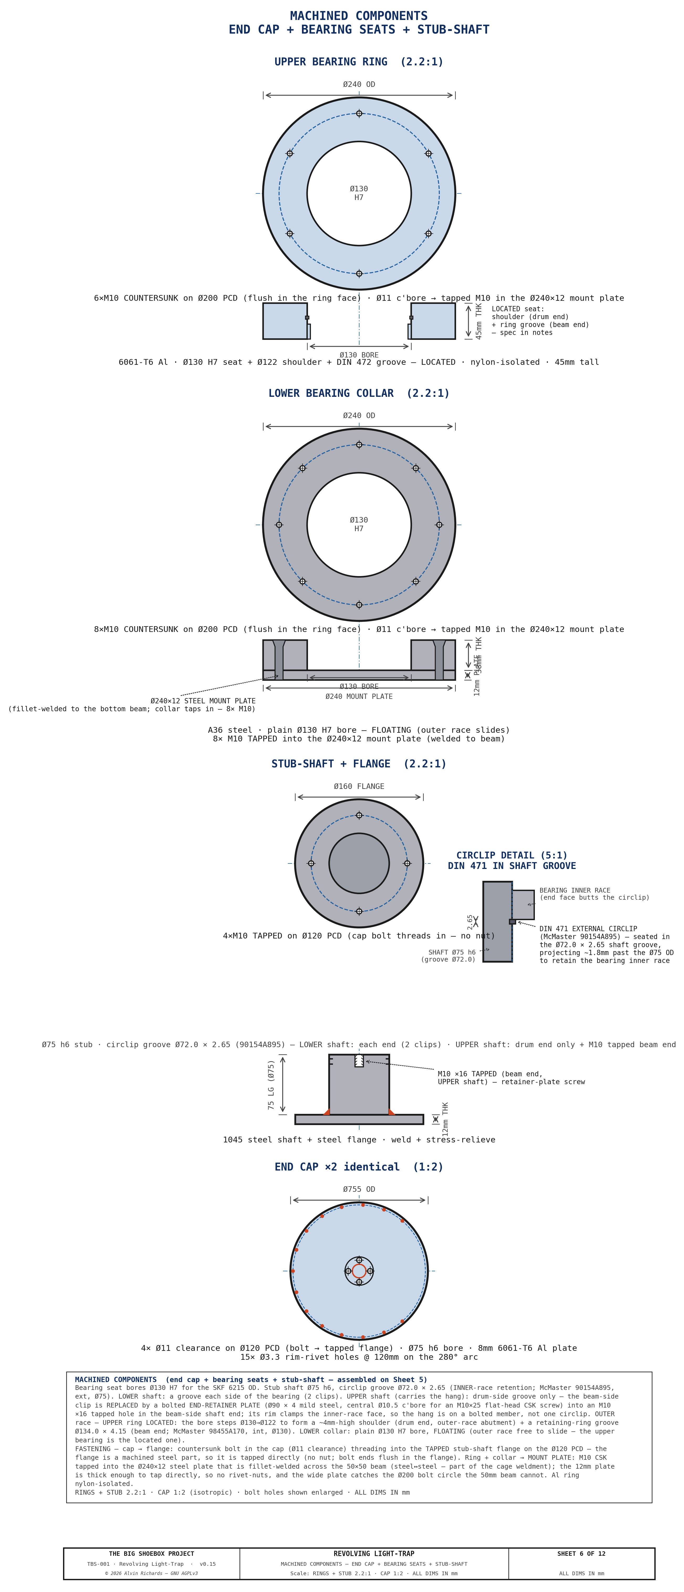
diagrams/lighttrap-sheet6.png
