alvinr/tbs/diagrams/lighttrap-sheet8.png

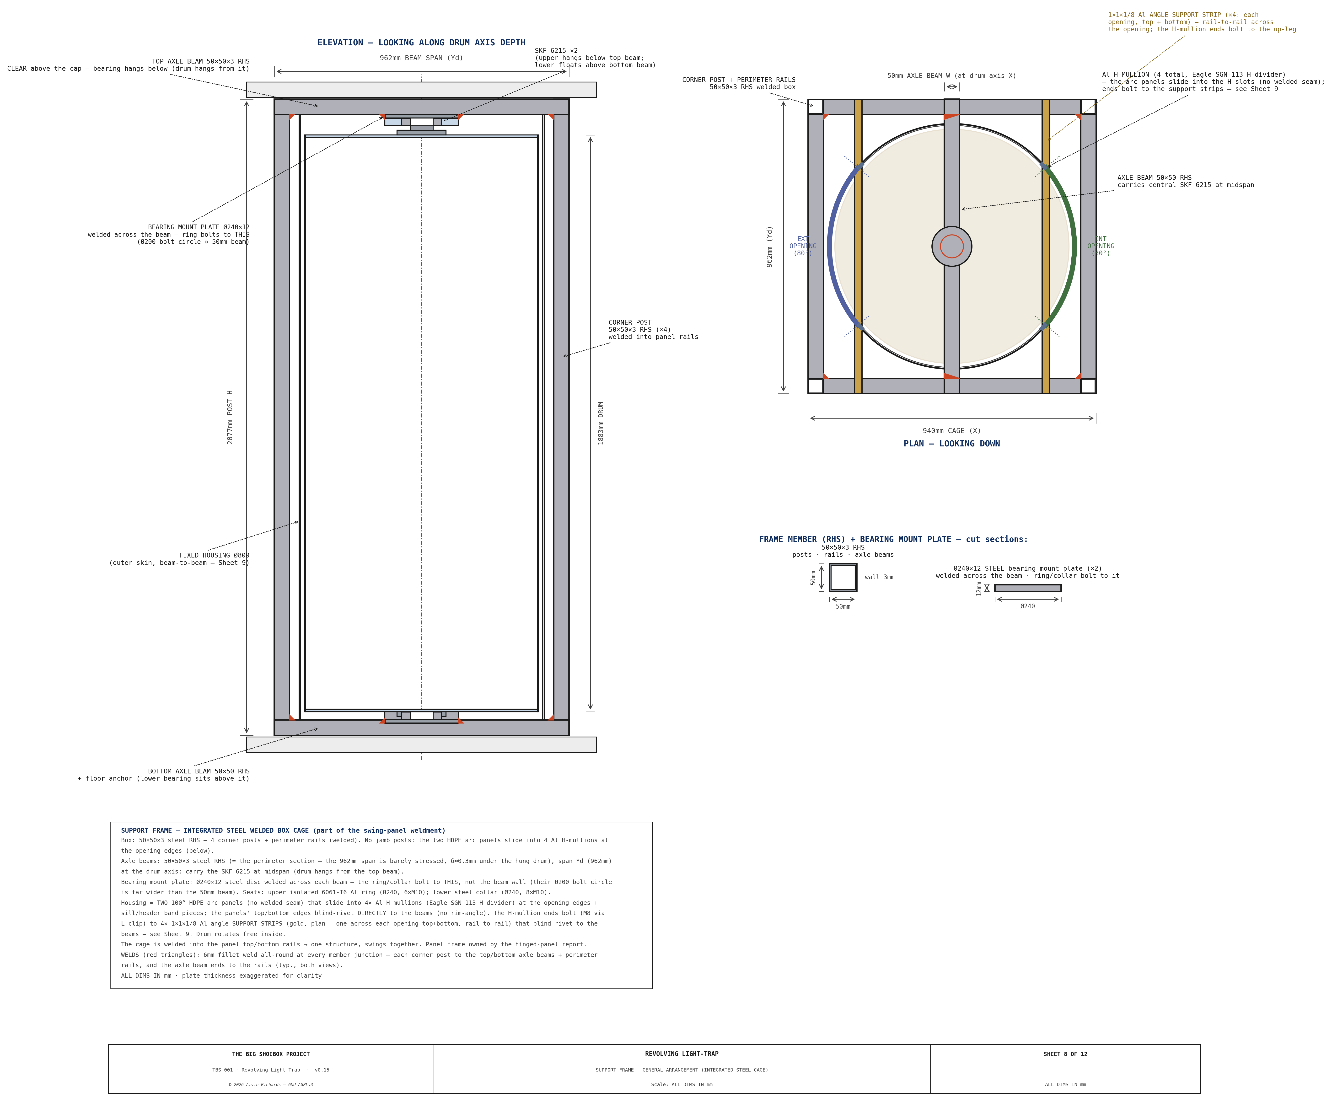
diagrams/lighttrap-sheet8.png
