alvinr/tbs/diagrams/lighttrap-sheet9.png

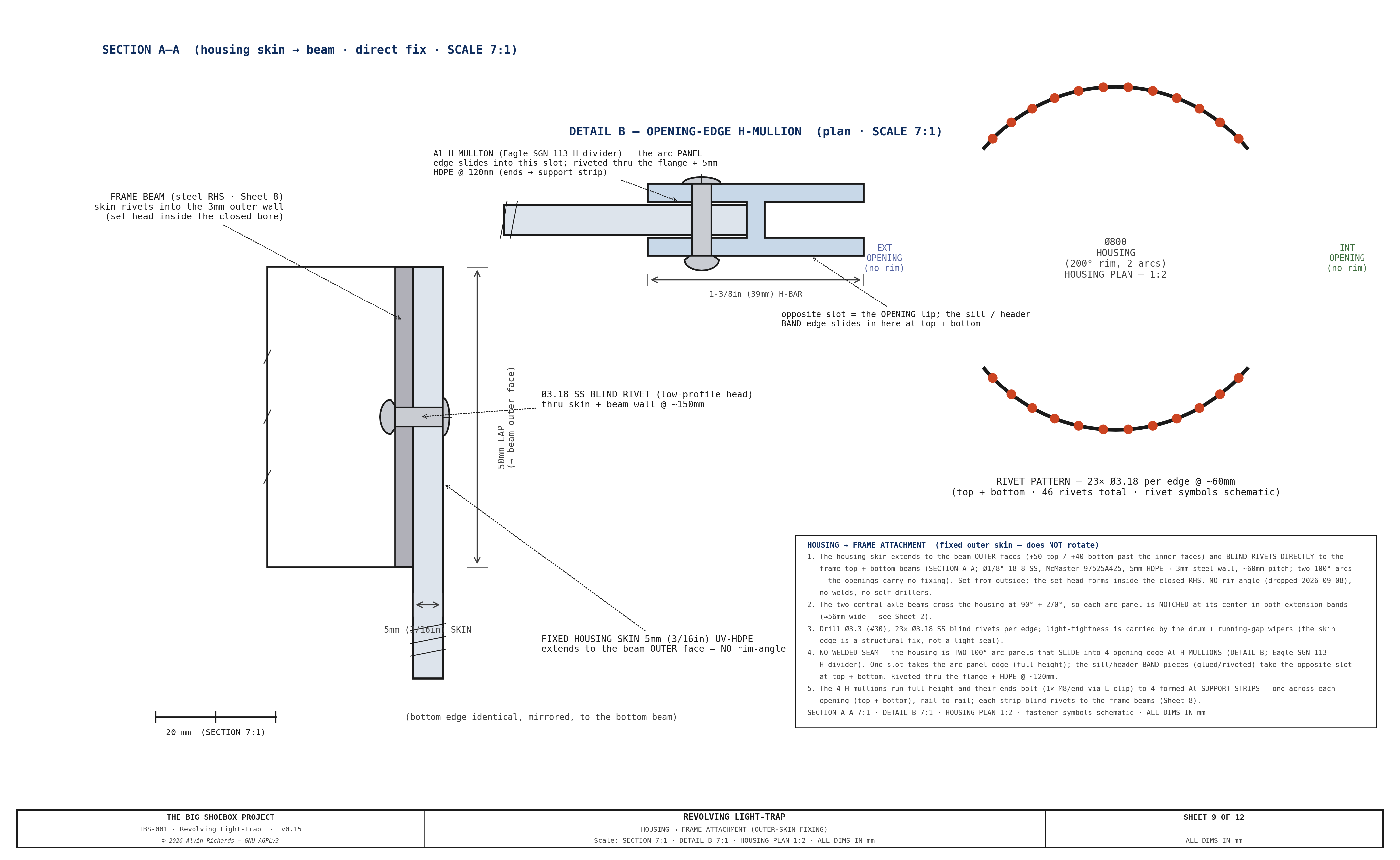
diagrams/lighttrap-sheet9.png
