alvinr/tbs/diagrams/lighttrap-sheet10.png

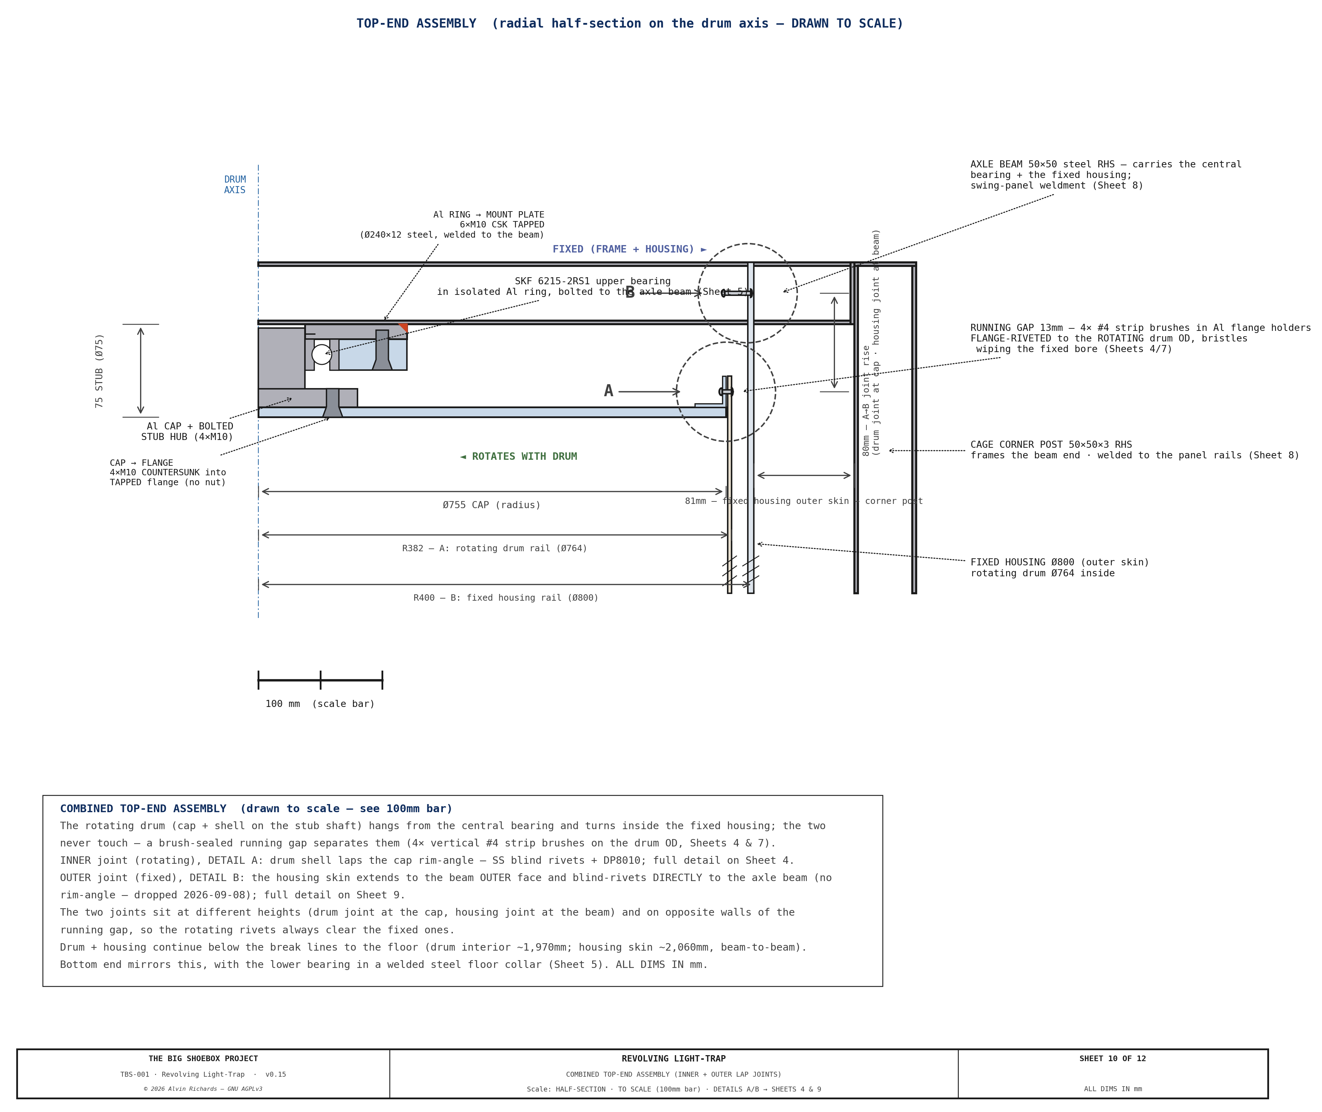
diagrams/lighttrap-sheet10.png
