alvinr/tbs/diagrams/lighttrap-sheet11.png

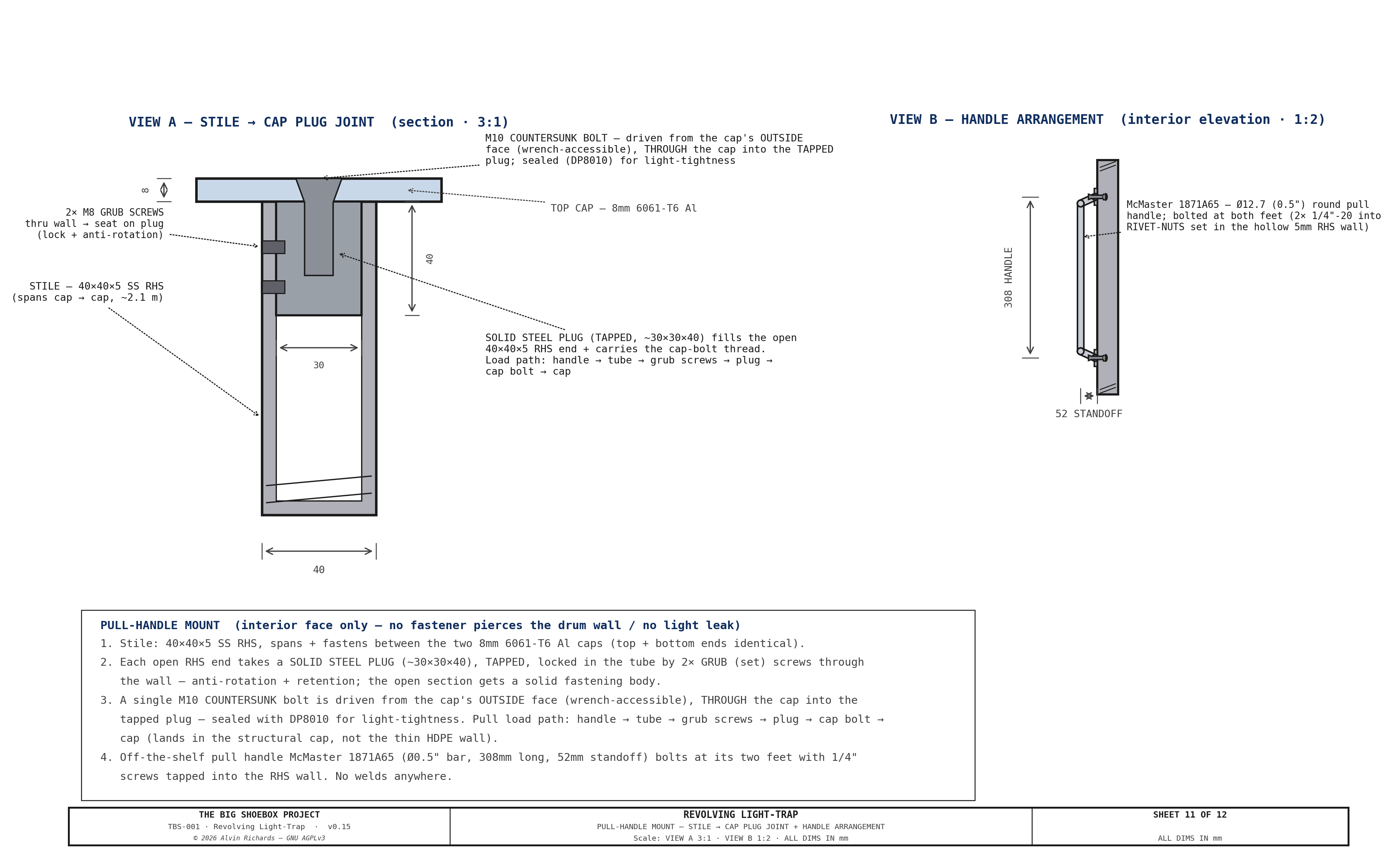
diagrams/lighttrap-sheet11.png
