alvinr/tbs/diagrams/lighttrap-sheet12.png

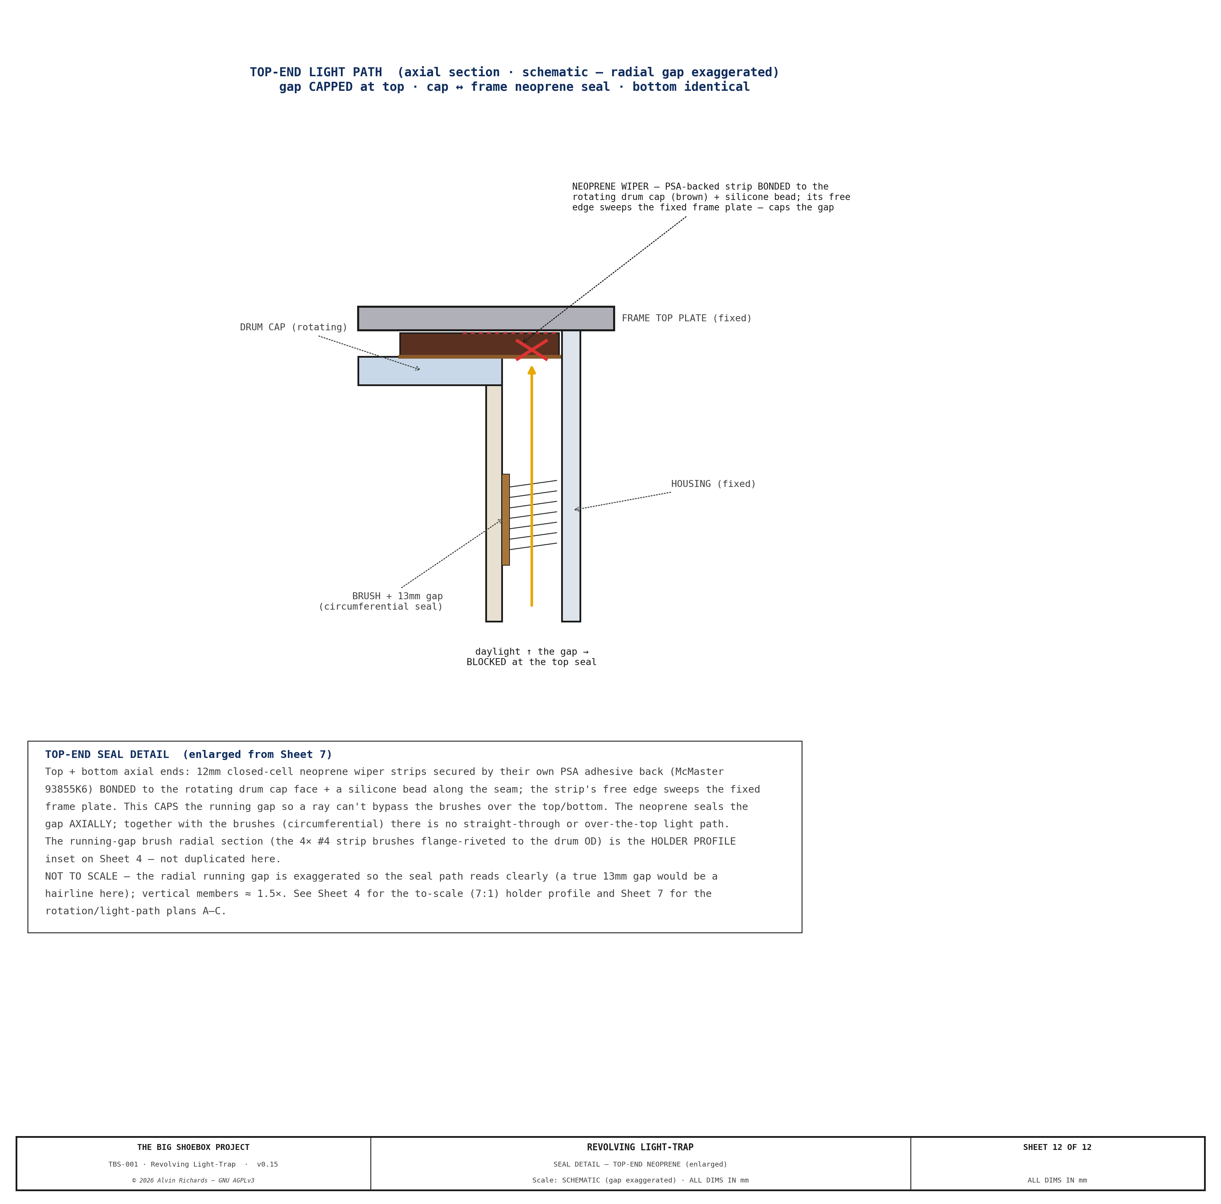
diagrams/lighttrap-sheet12.png
