alvinr/tbs/diagrams/line-of-sight.png

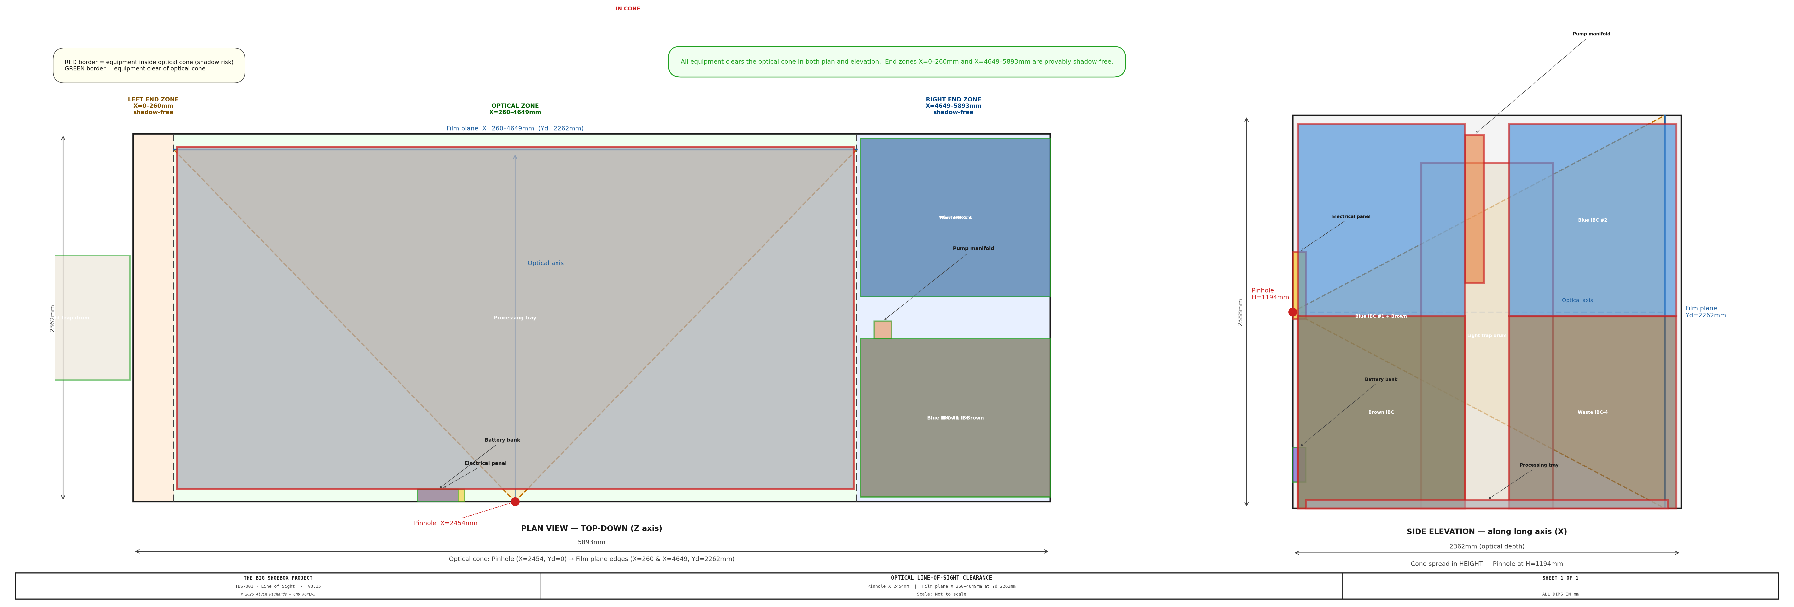
diagrams/line-of-sight.png
