alvinr/tbs/diagrams/pinhole-wall-elevation.png

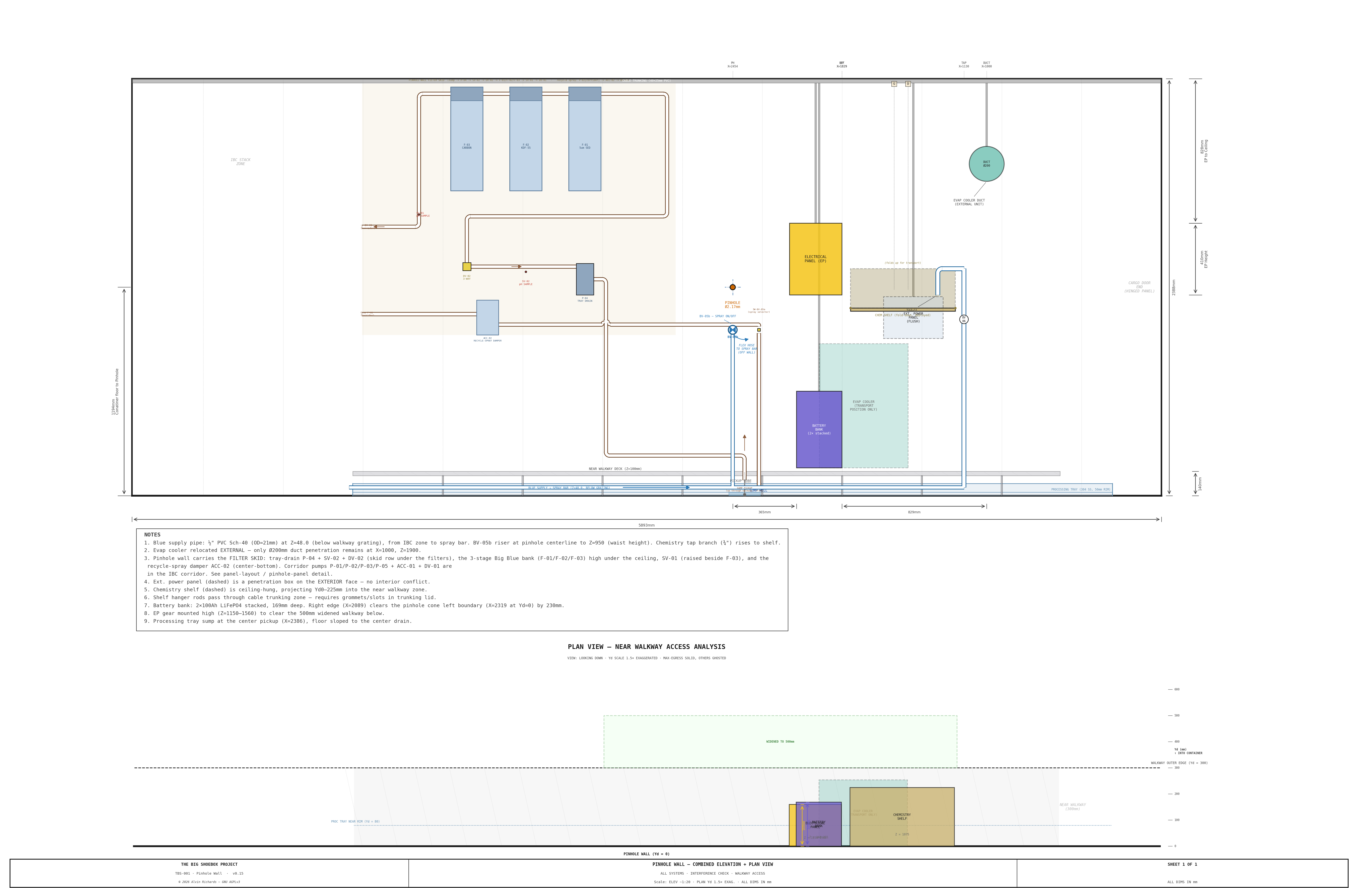
diagrams/pinhole-wall-elevation.png
