alvinr/tbs/diagrams/plywood-cutsheets-sheet1.png

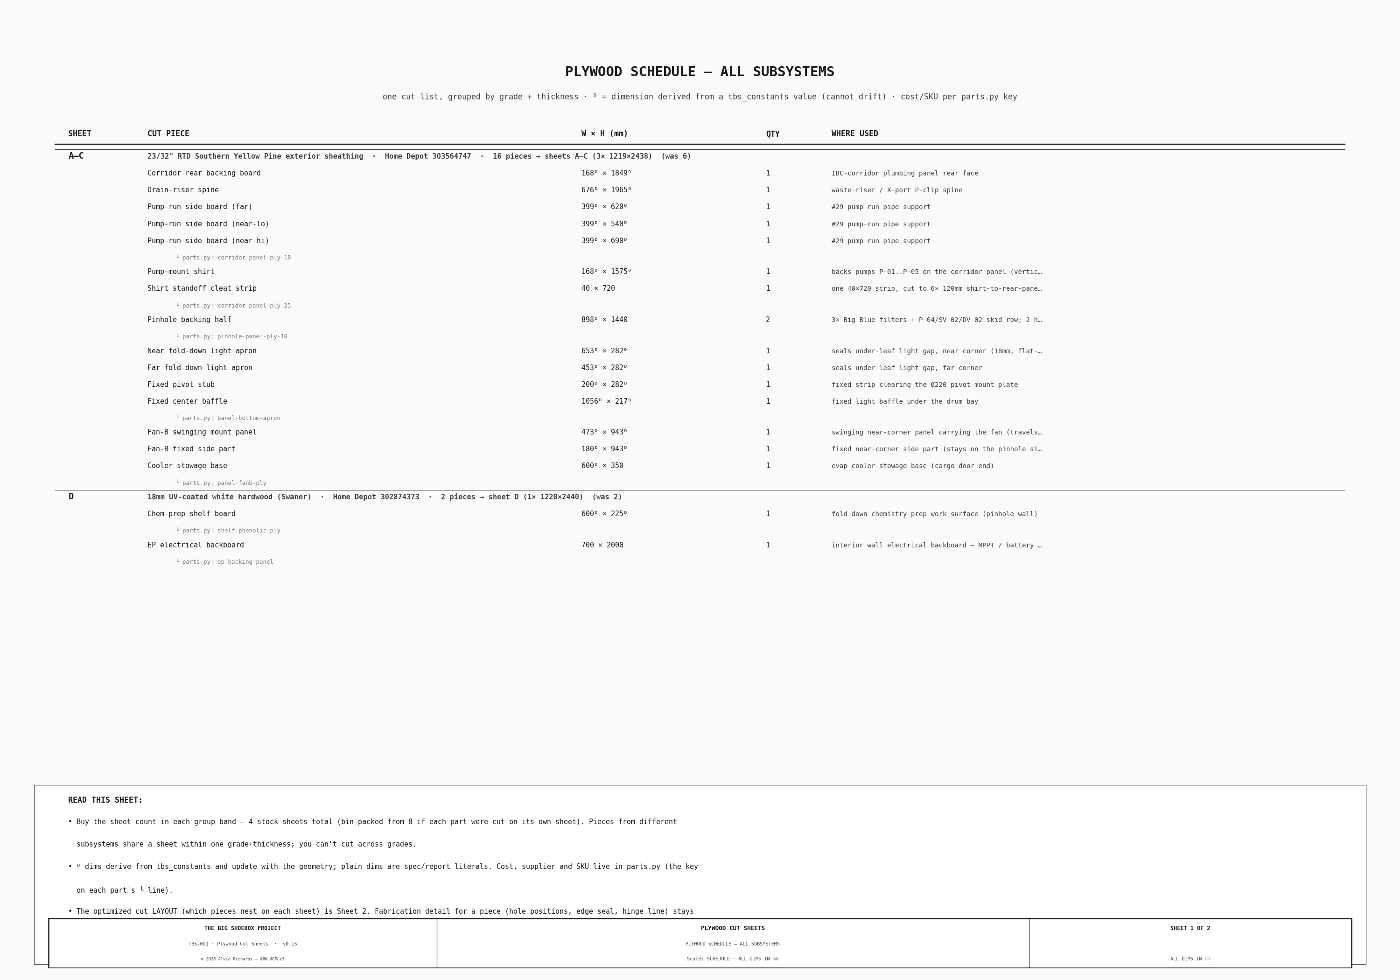
diagrams/plywood-cutsheets-sheet1.png
