alvinr/tbs/diagrams/plywood-cutsheets-sheet2.png

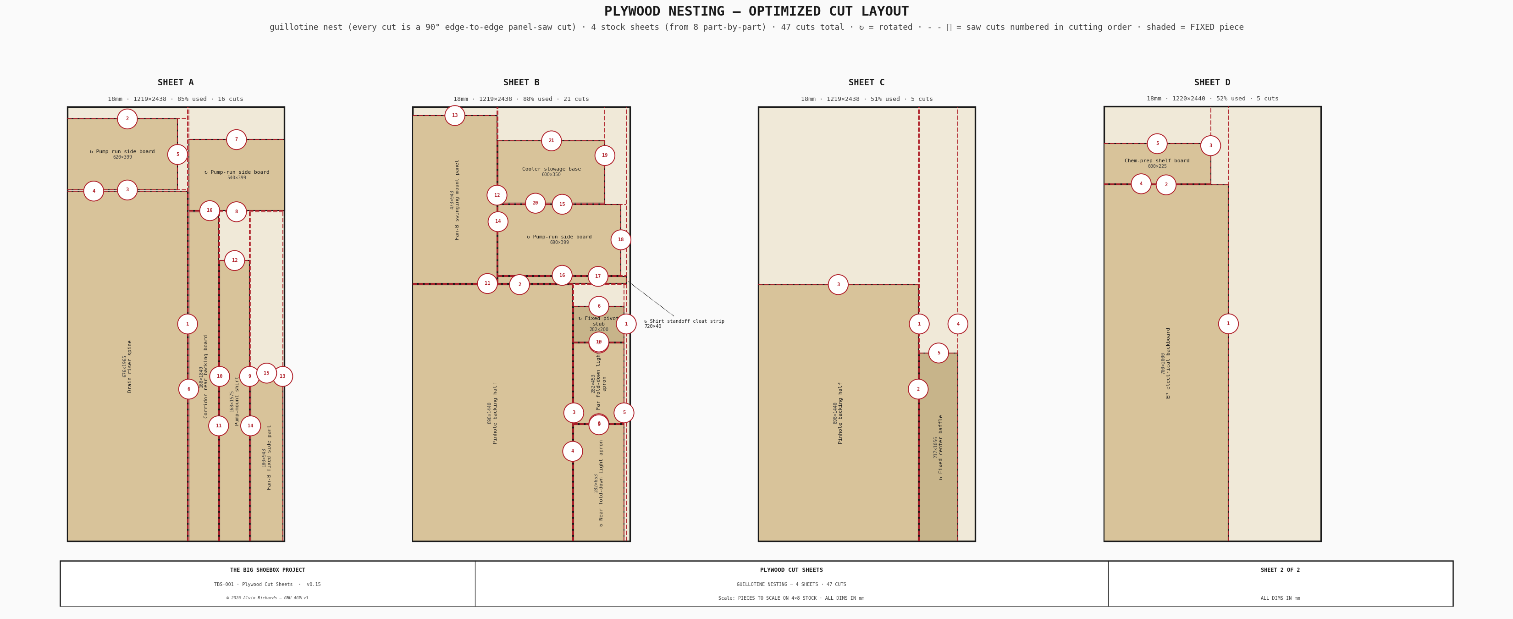
diagrams/plywood-cutsheets-sheet2.png
