alvinr/tbs/diagrams/portrait-camera-schematic.png

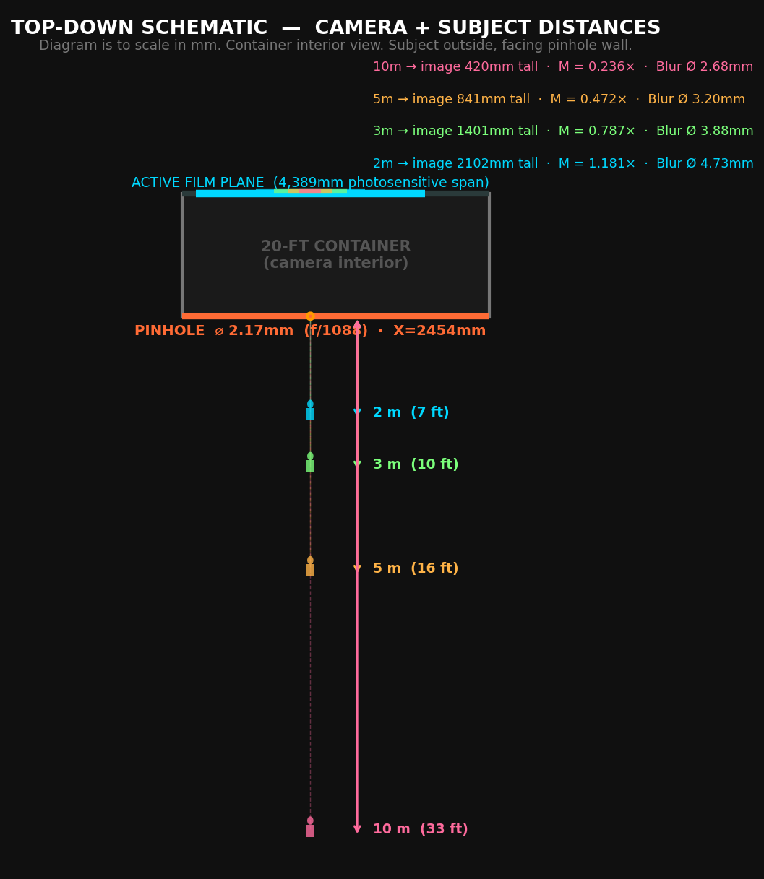
diagrams/portrait-camera-schematic.png
