alvinr/tbs/diagrams/portrait-optimal-3m.png

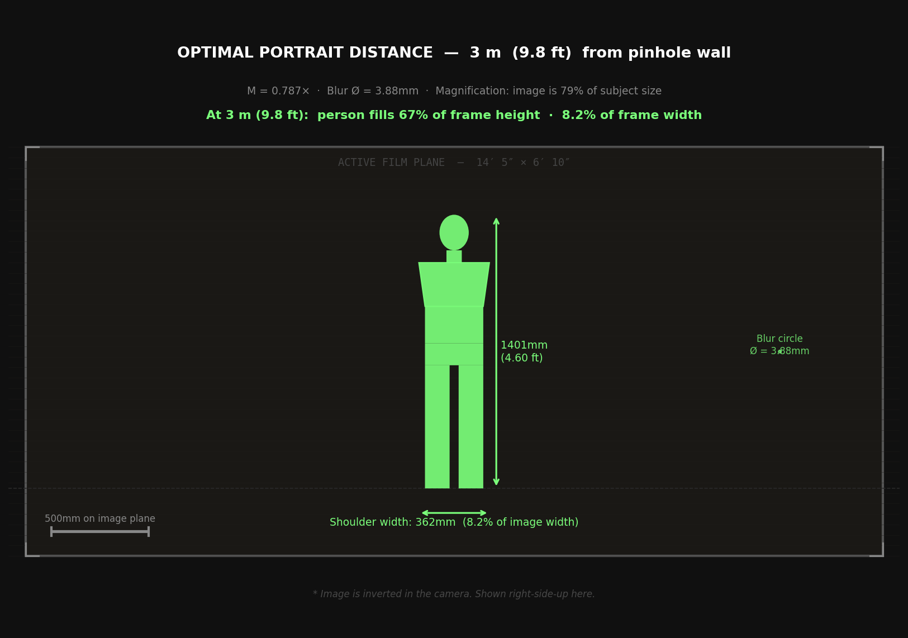
diagrams/portrait-optimal-3m.png
