alvinr/tbs/diagrams/portrait-scale-comparison.png

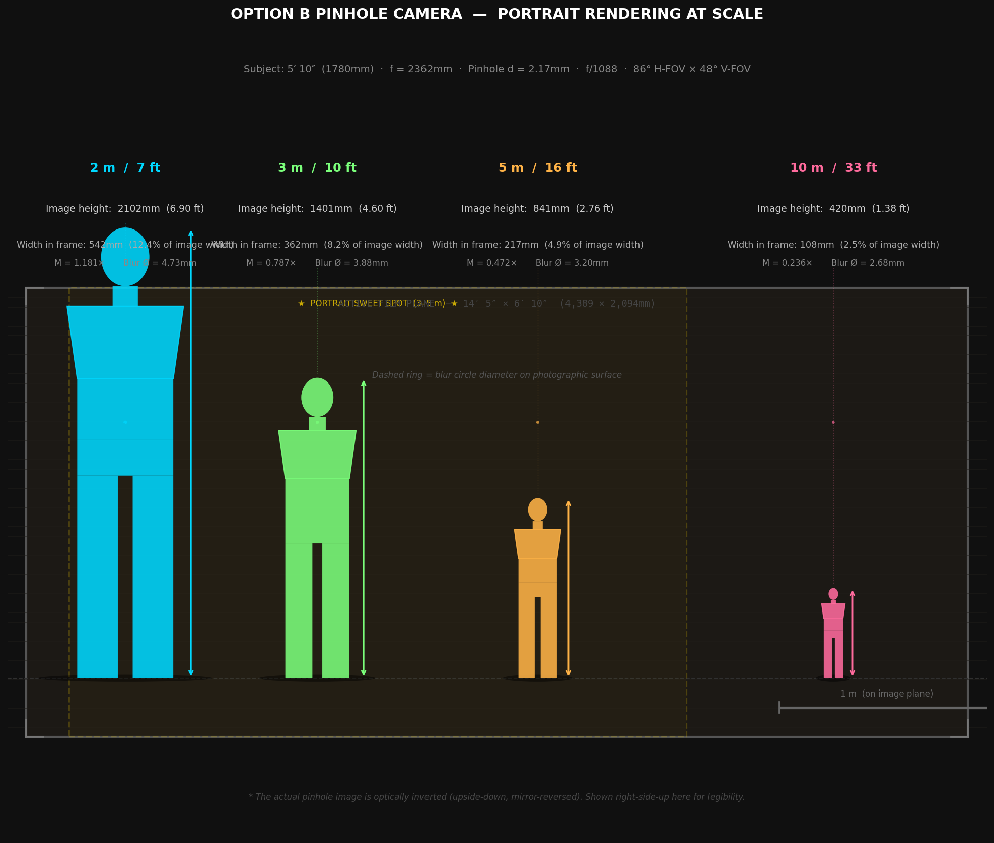
diagrams/portrait-scale-comparison.png
