alvinr/tbs/diagrams/shelf-sheet1.png

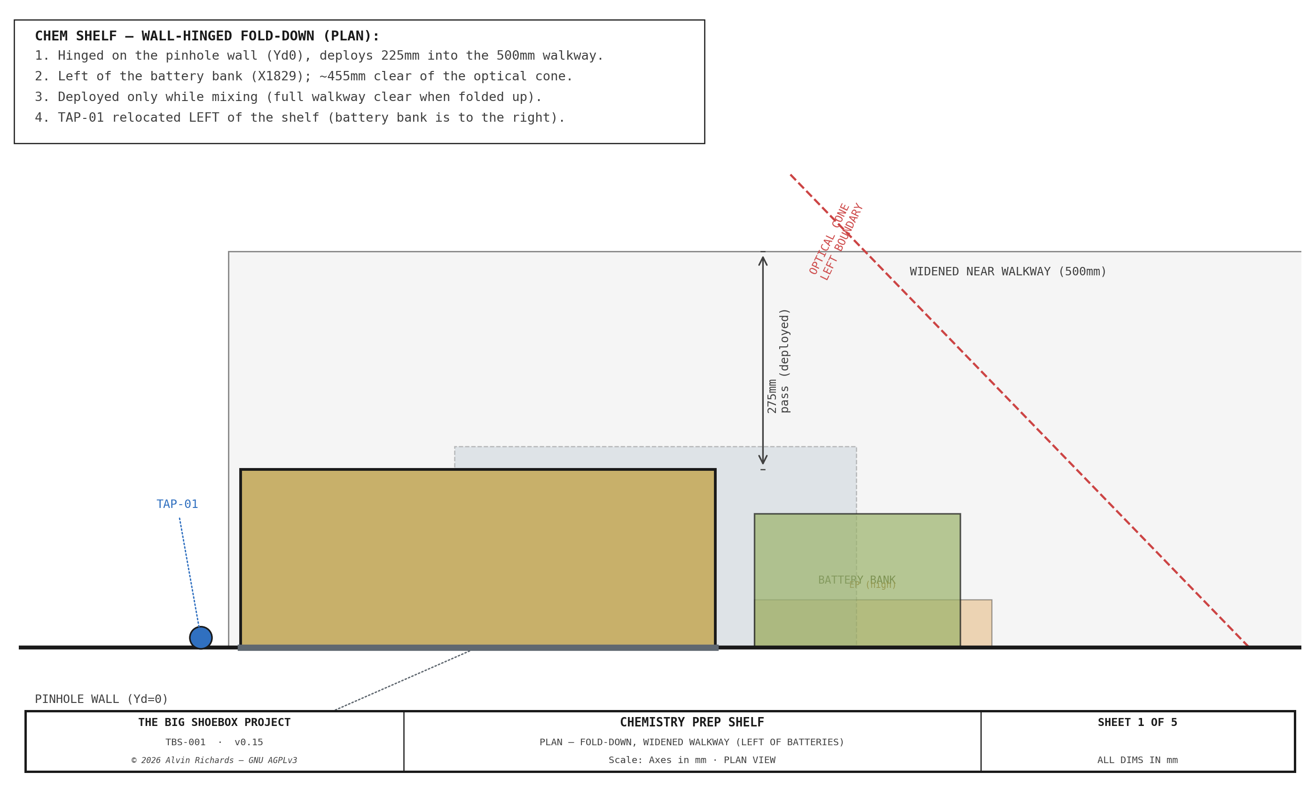
diagrams/shelf-sheet1.png
