alvinr/tbs/diagrams/shelf-sheet2.png

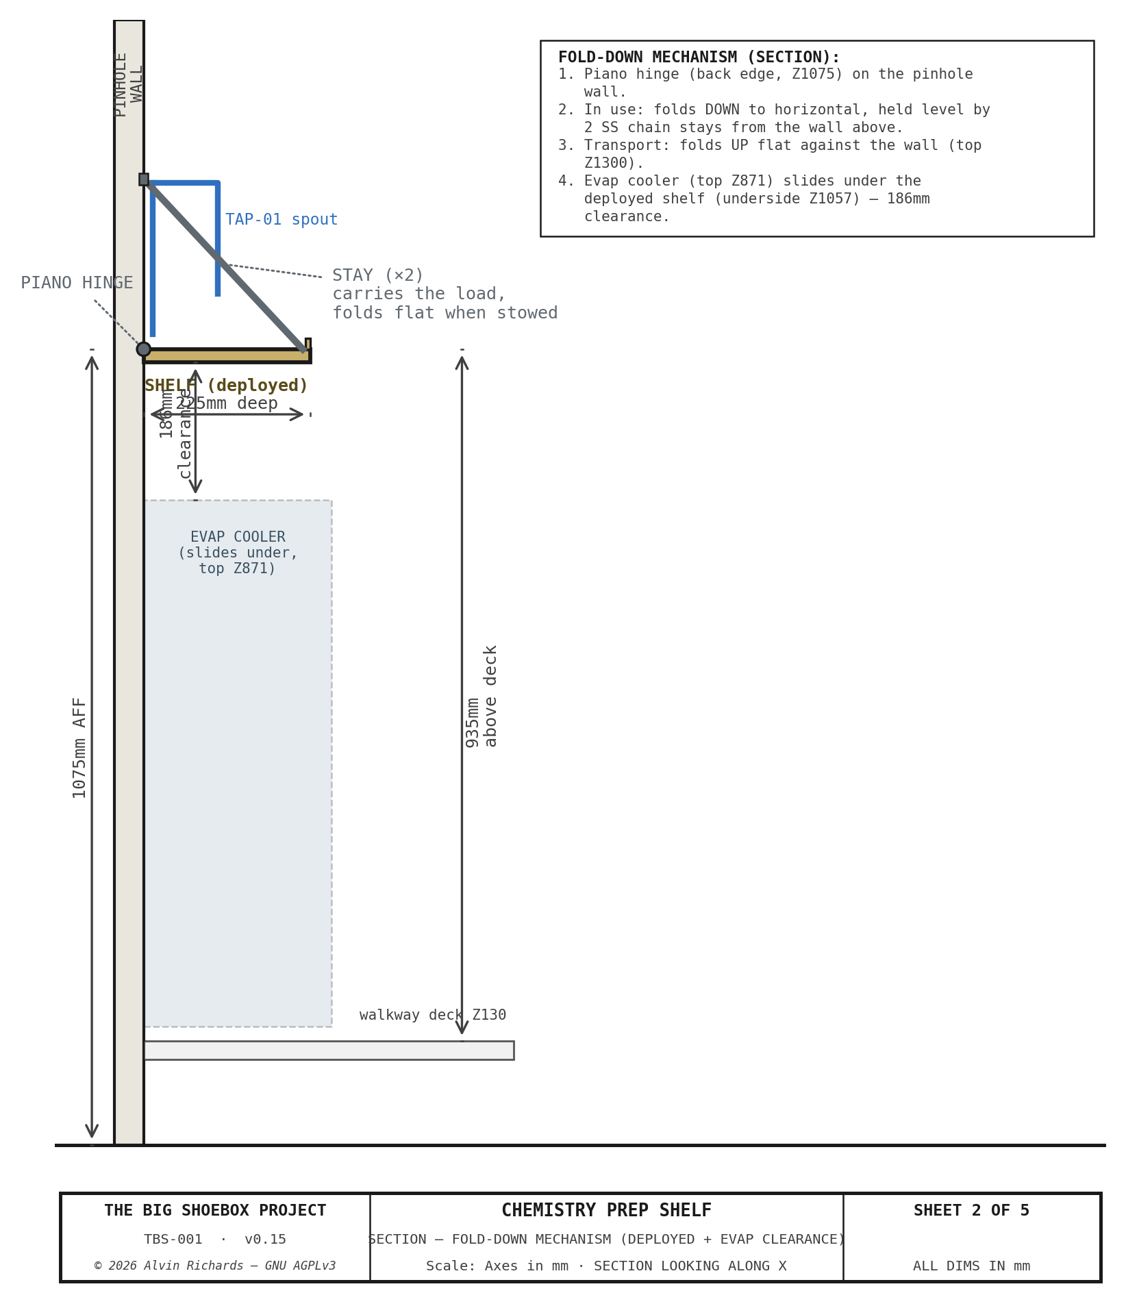
diagrams/shelf-sheet2.png
