alvinr/tbs/diagrams/shelf-sheet3.png

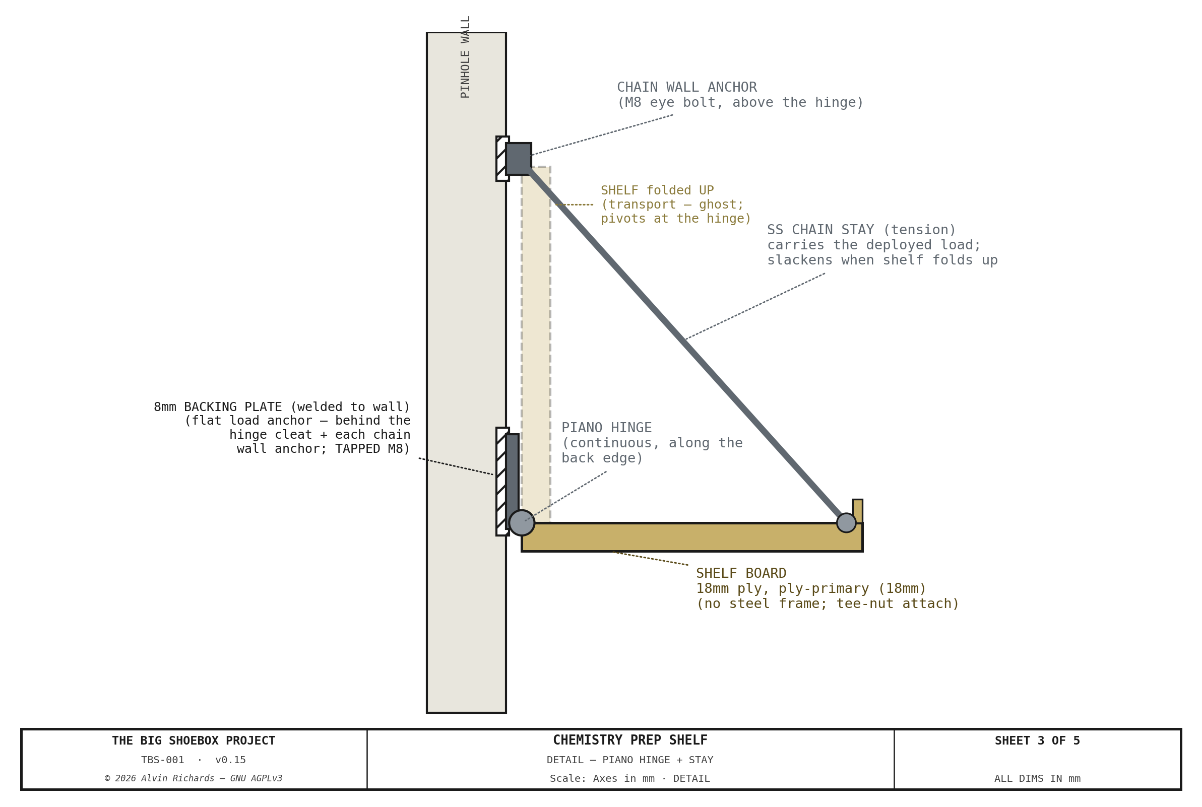
diagrams/shelf-sheet3.png
