alvinr/tbs/diagrams/shelf-sheet4.png

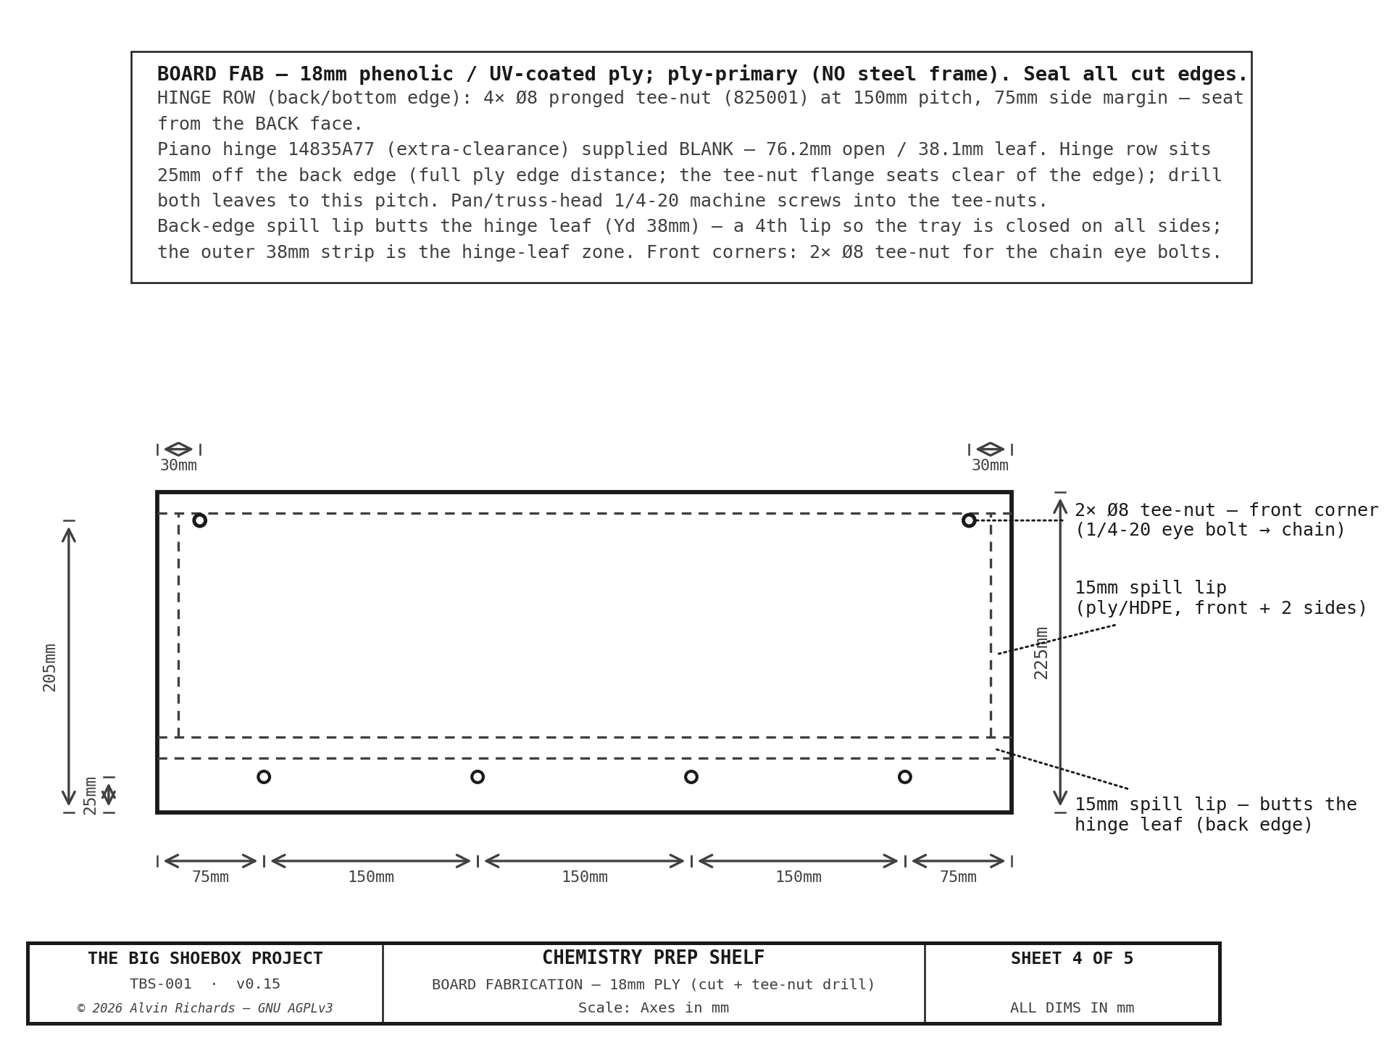
diagrams/shelf-sheet4.png
