alvinr/tbs/diagrams/shelf-sheet5.png

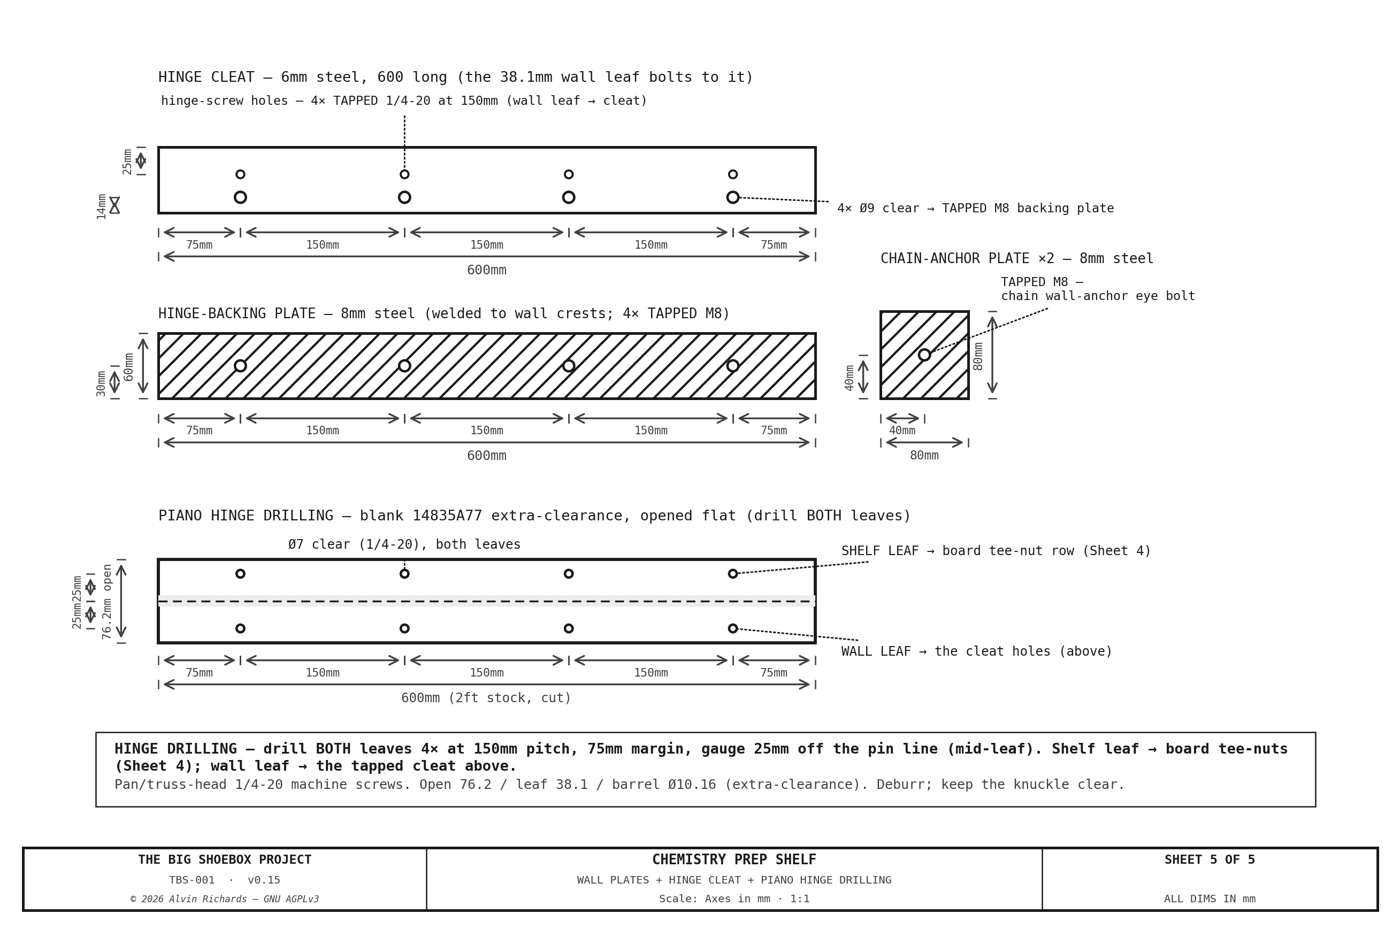
diagrams/shelf-sheet5.png
