alvinr/tbs/diagrams/spray-bar-sheet1.png

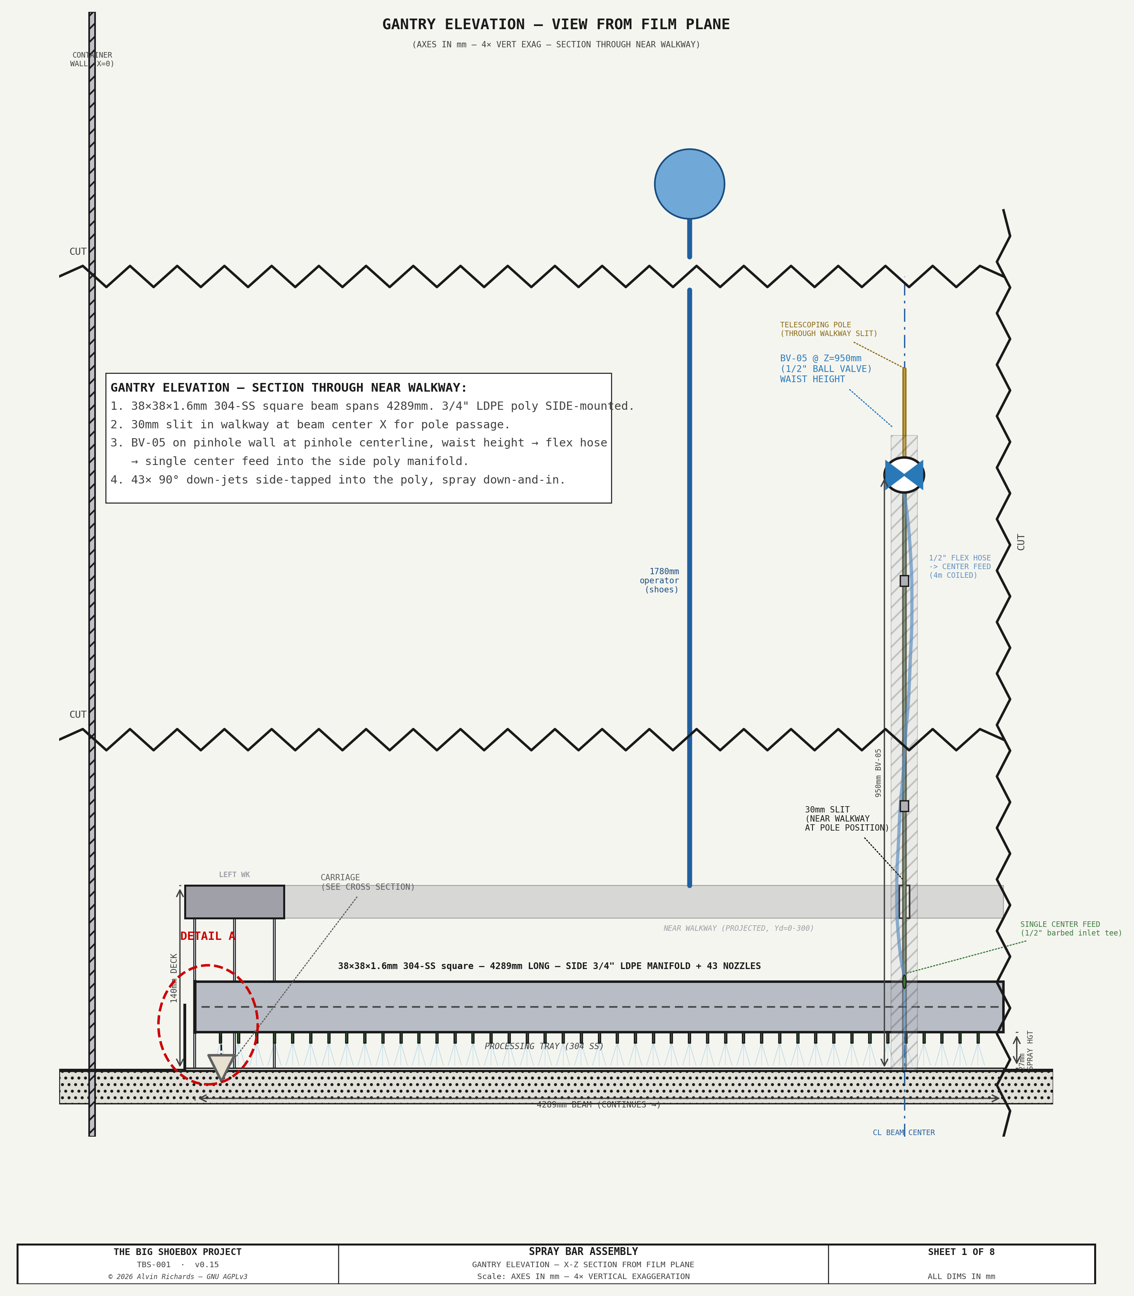
diagrams/spray-bar-sheet1.png
