alvinr/tbs/diagrams/spray-bar-sheet2.png

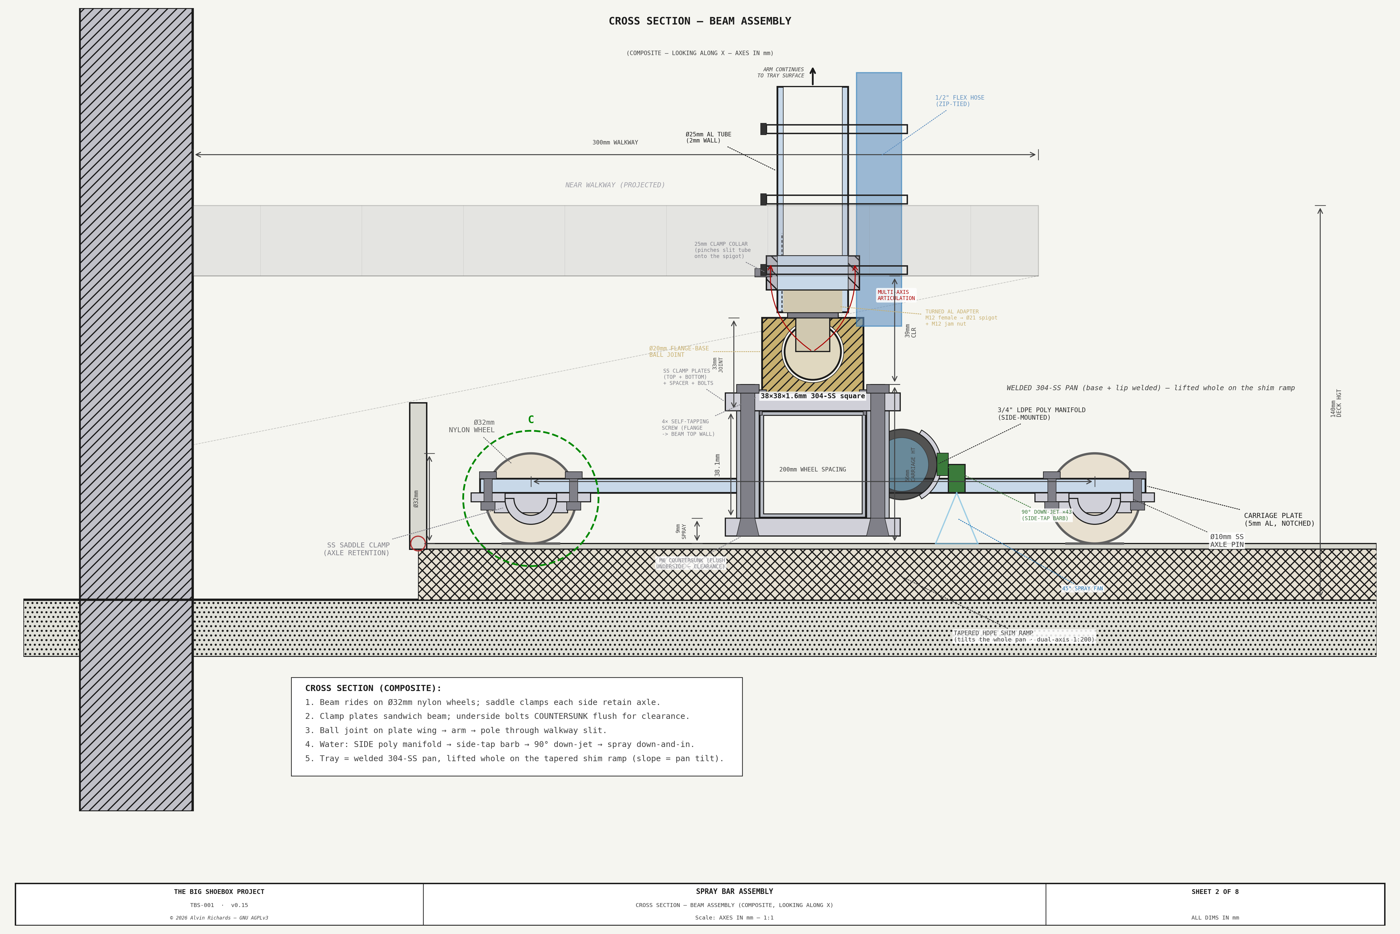
diagrams/spray-bar-sheet2.png
