alvinr/tbs/diagrams/spray-bar-sheet4.png

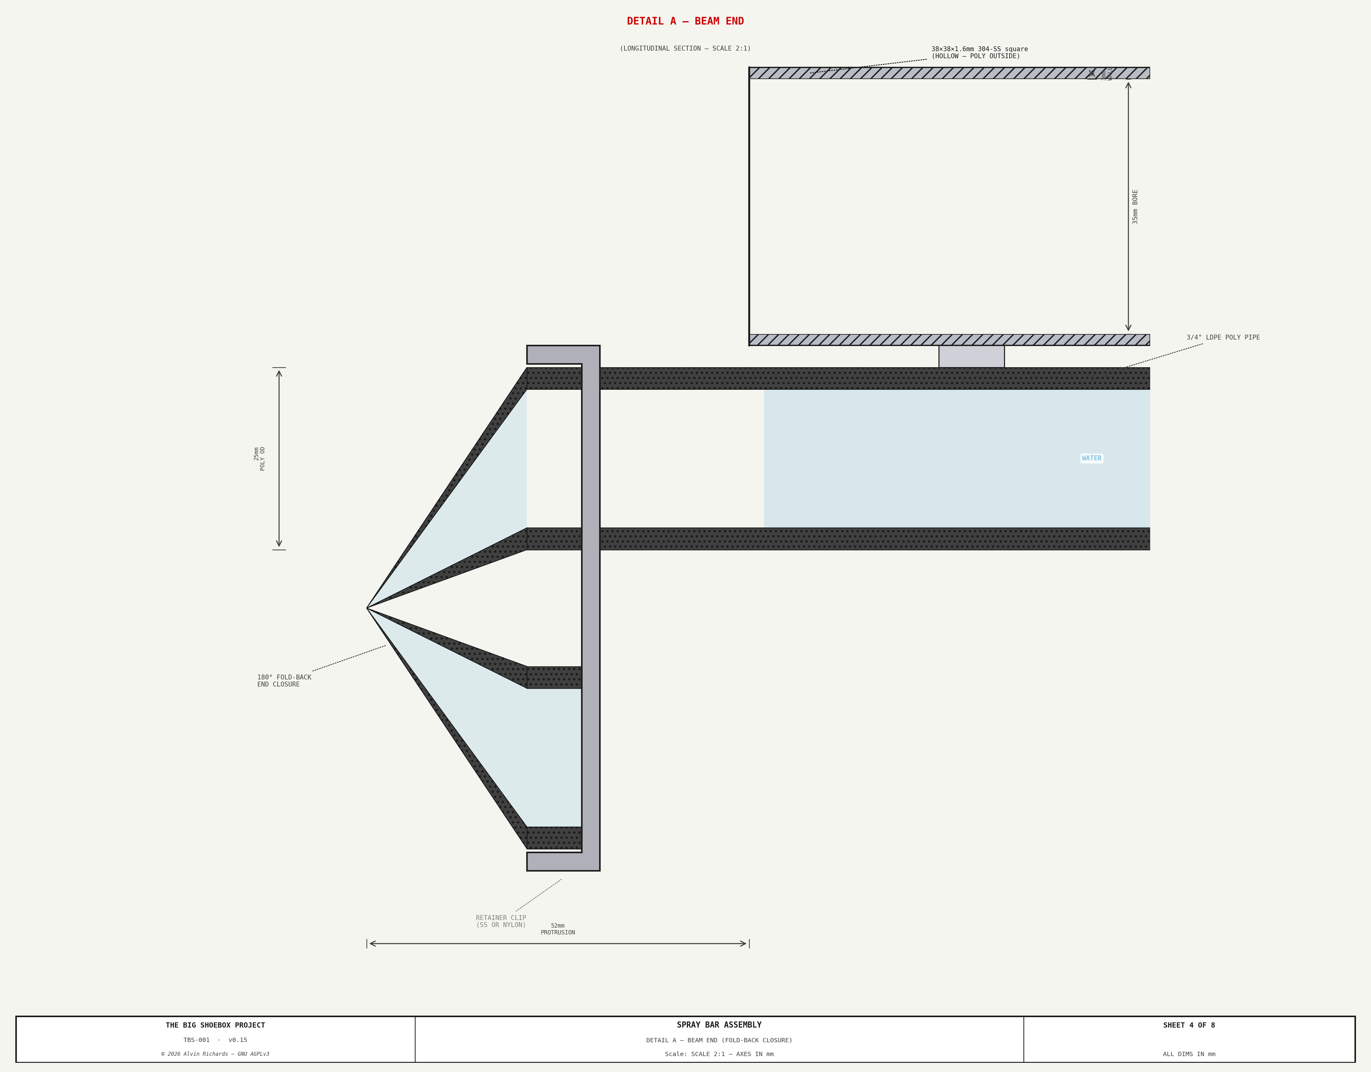
diagrams/spray-bar-sheet4.png
