alvinr/tbs/diagrams/spray-bar-sheet5.png

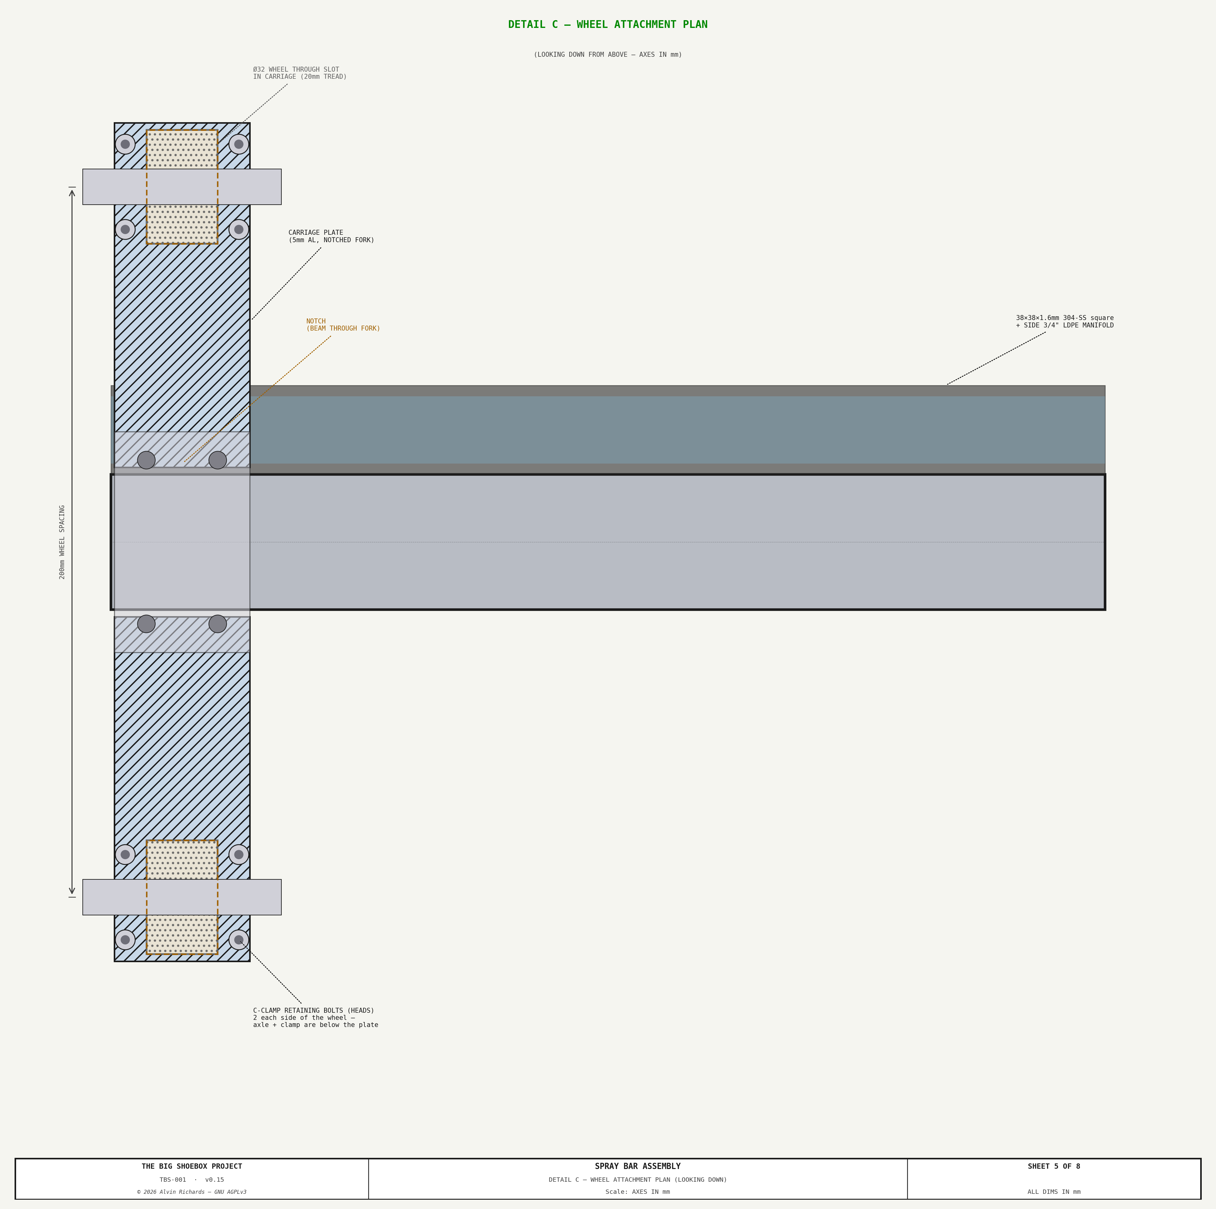
diagrams/spray-bar-sheet5.png
