alvinr/tbs/diagrams/spray-bar-sheet6.png

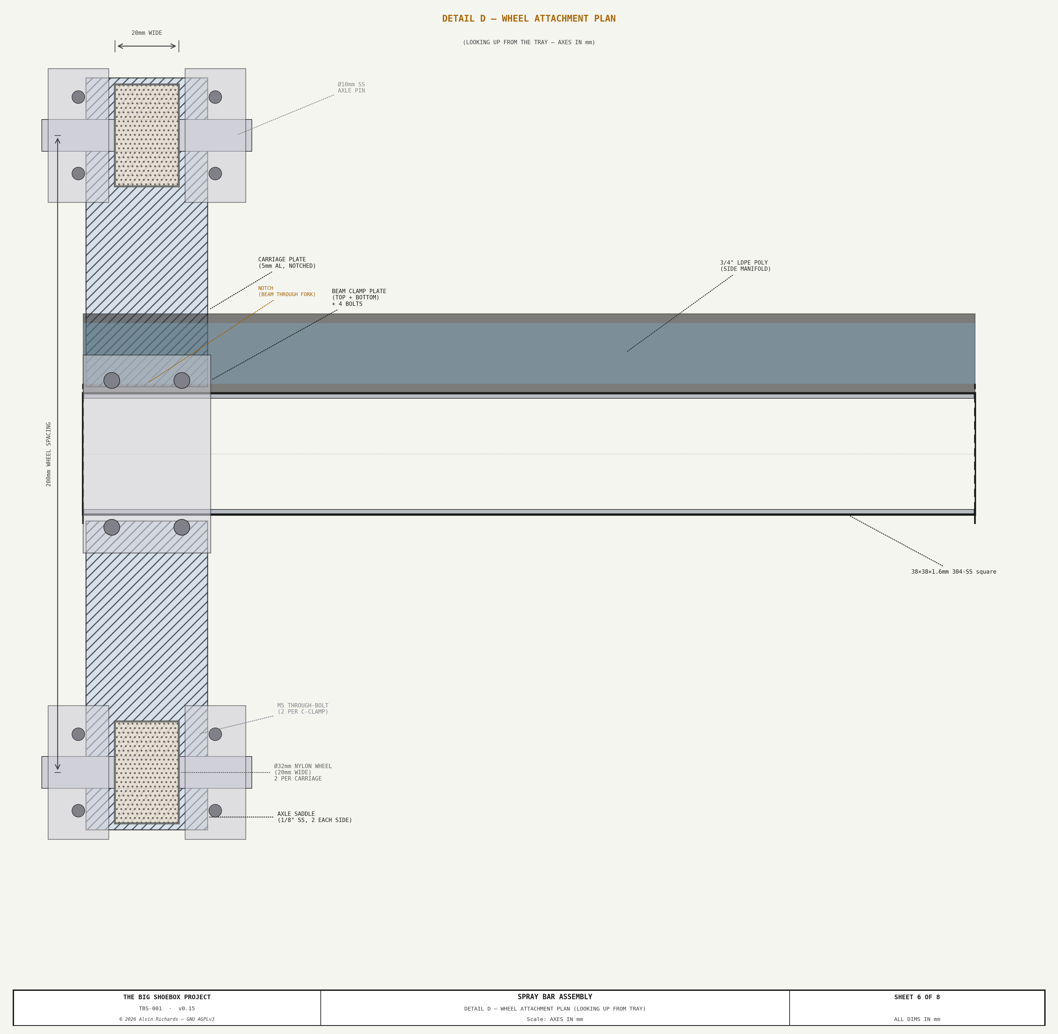
diagrams/spray-bar-sheet6.png
