alvinr/tbs/diagrams/spray-bar-sheet7.png

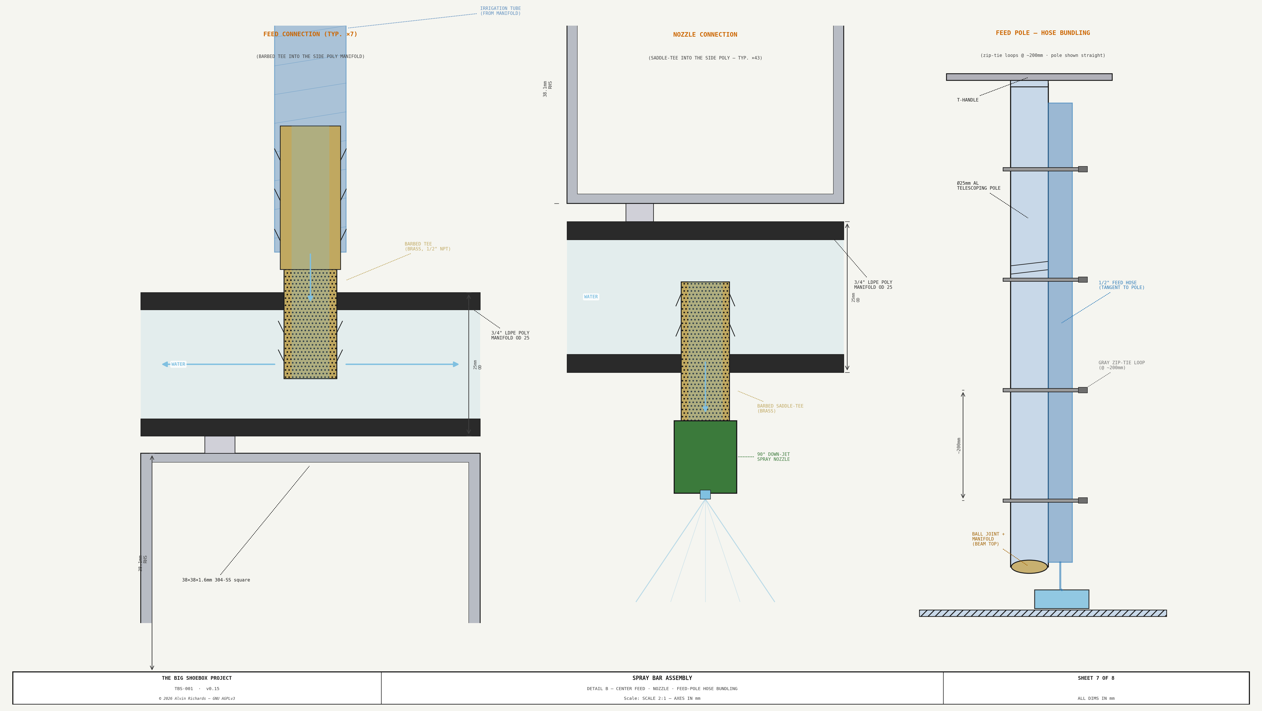
diagrams/spray-bar-sheet7.png
