alvinr/tbs/diagrams/spray-bar-sheet8.png

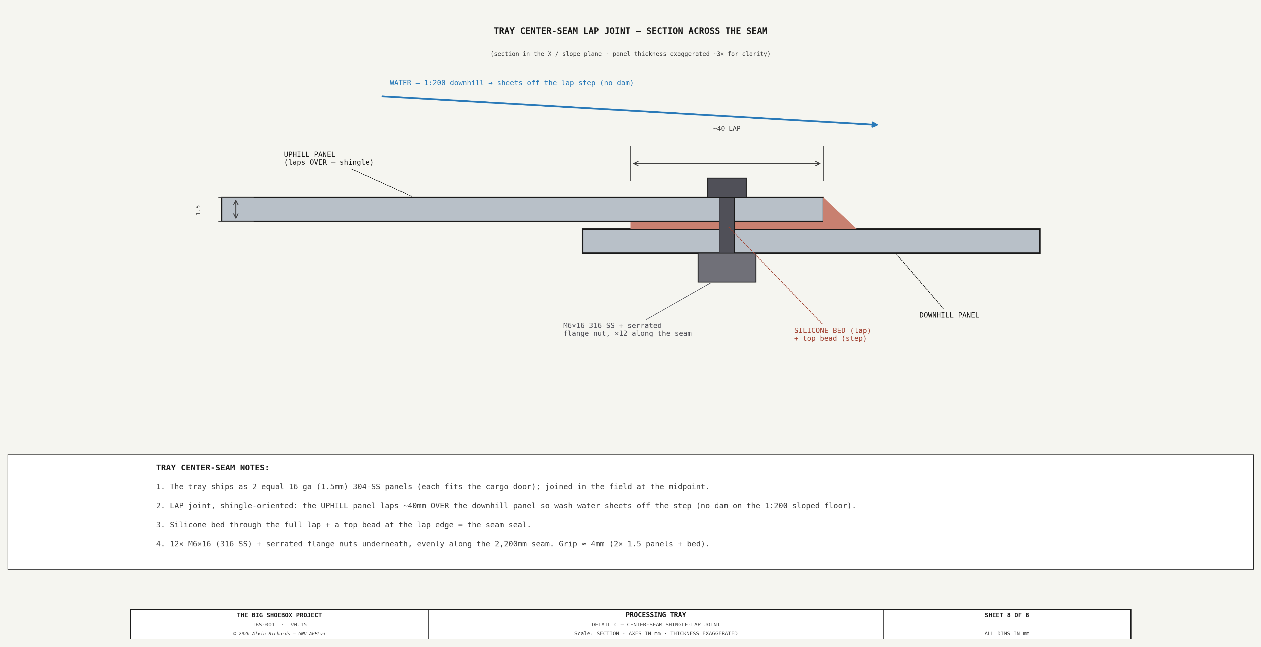
diagrams/spray-bar-sheet8.png
