alvinr/tbs/diagrams/tray-redesign-sheet1.png

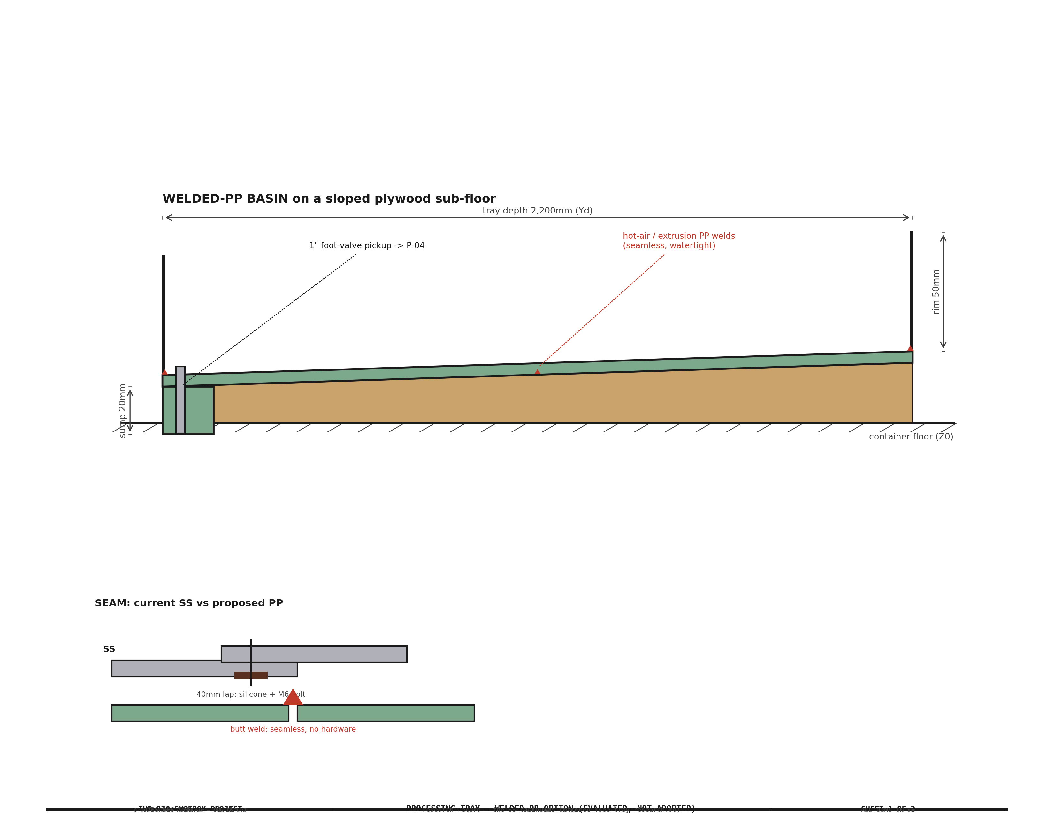
diagrams/tray-redesign-sheet1.png
