alvinr/tbs/diagrams/tray-redesign-sheet2.png

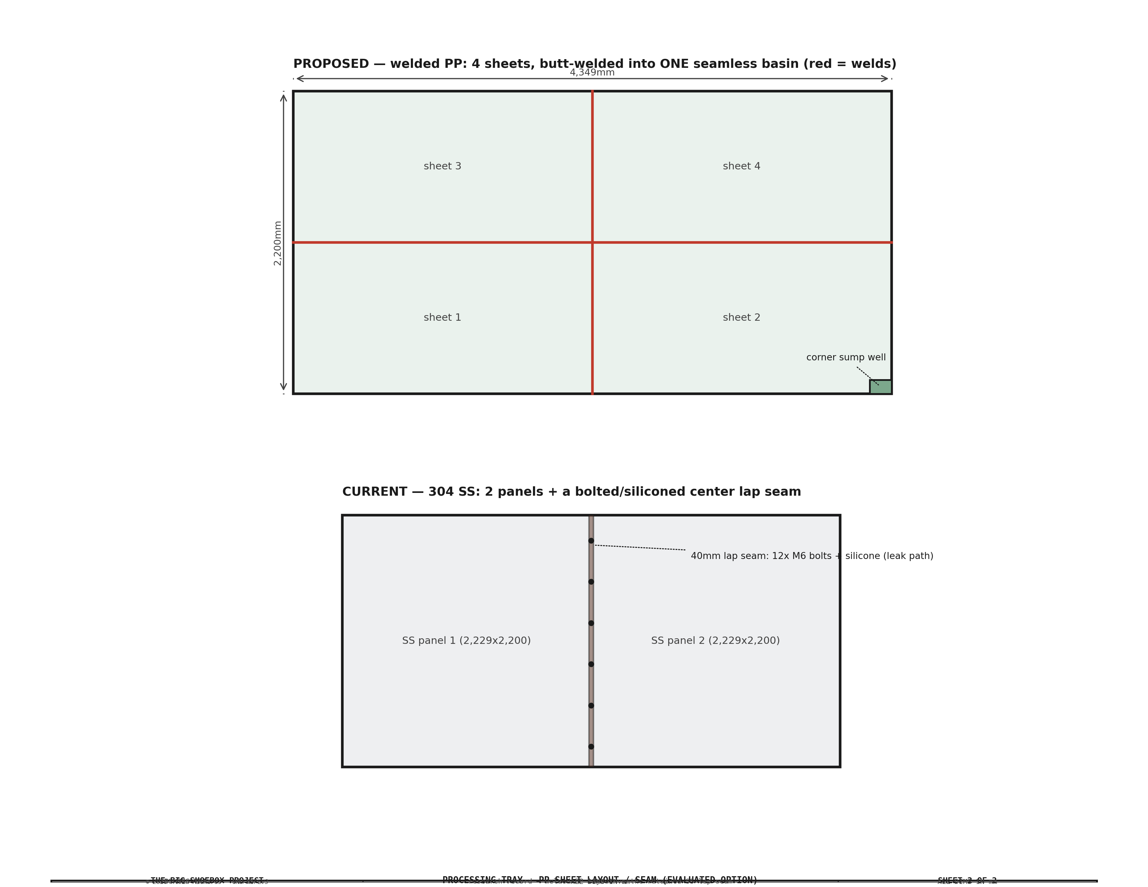
diagrams/tray-redesign-sheet2.png
