alvinr/tbs/diagrams/tray-slope-sheet1.png

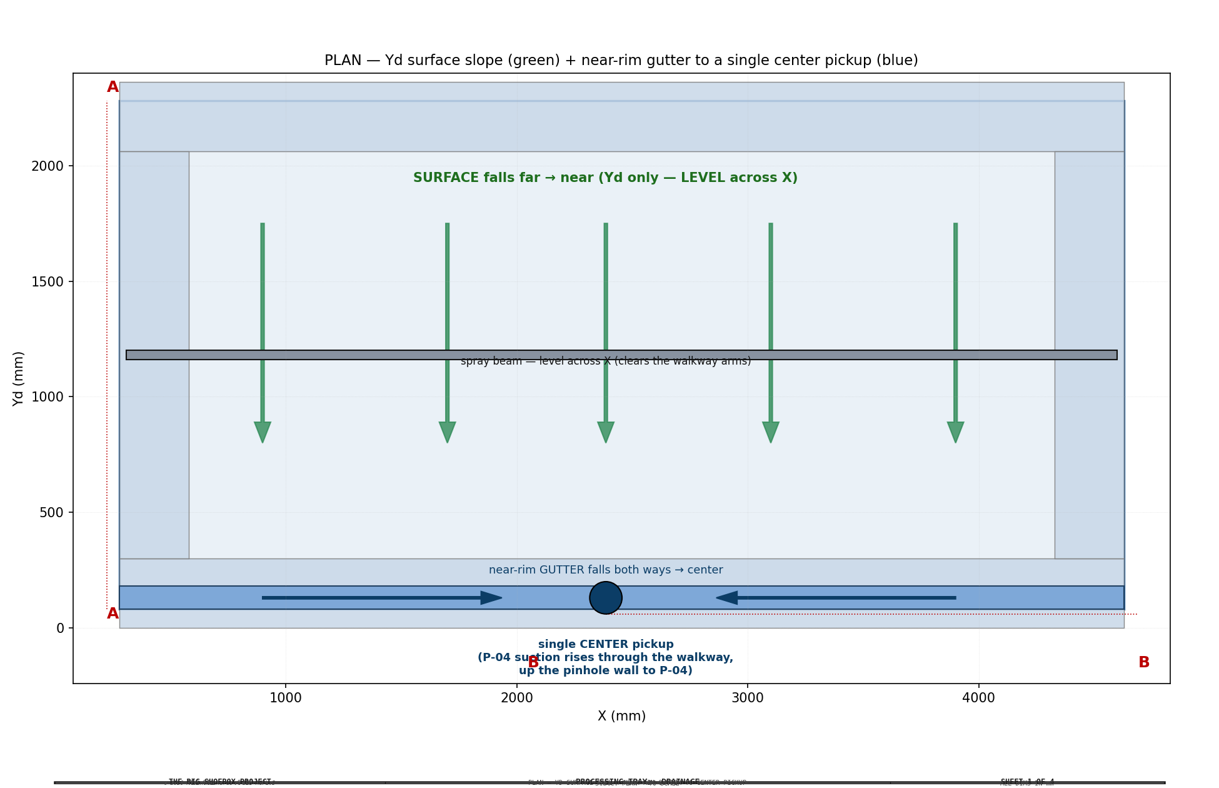
diagrams/tray-slope-sheet1.png
