alvinr/tbs/diagrams/tray-slope-sheet2.png

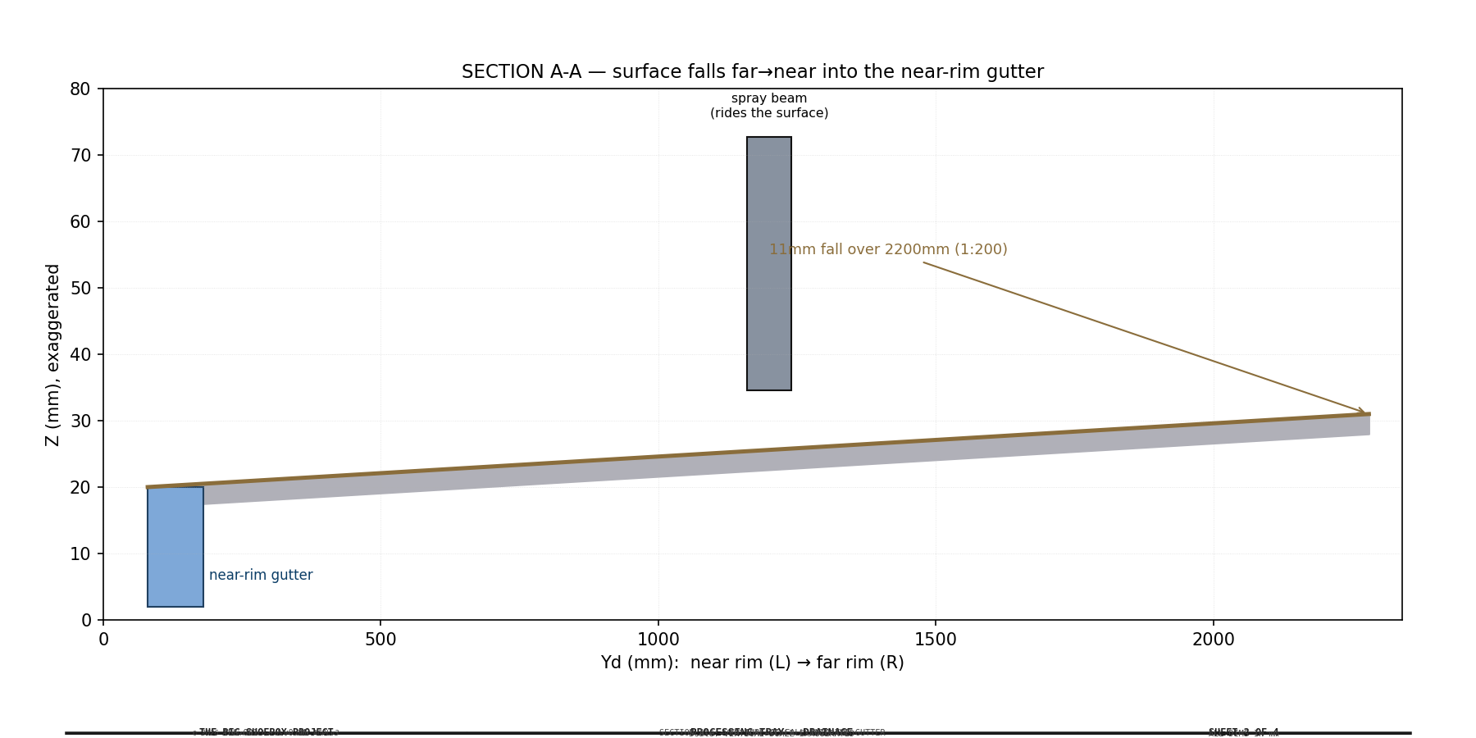
diagrams/tray-slope-sheet2.png
