alvinr/tbs/diagrams/tray-slope-sheet3.png

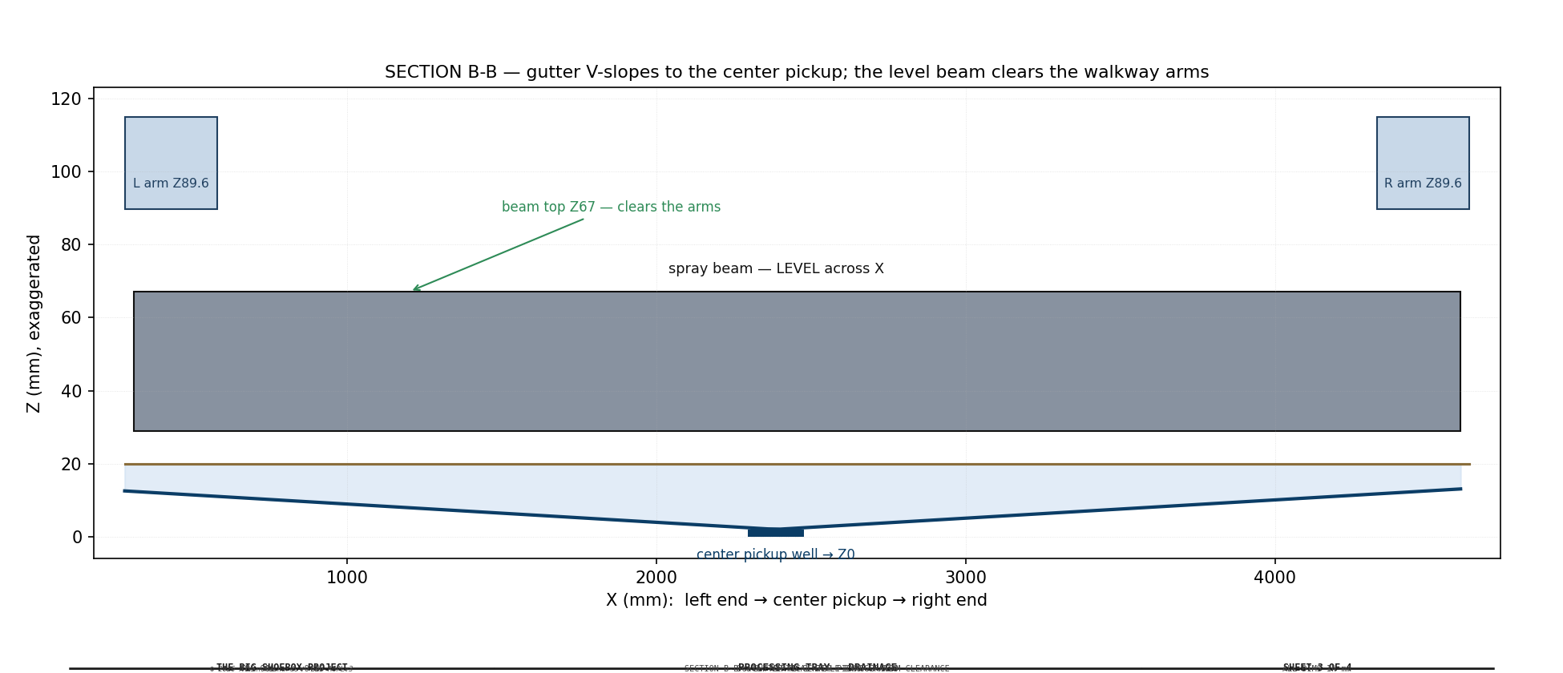
diagrams/tray-slope-sheet3.png
