alvinr/tbs/diagrams/tray-slope-sheet4.png

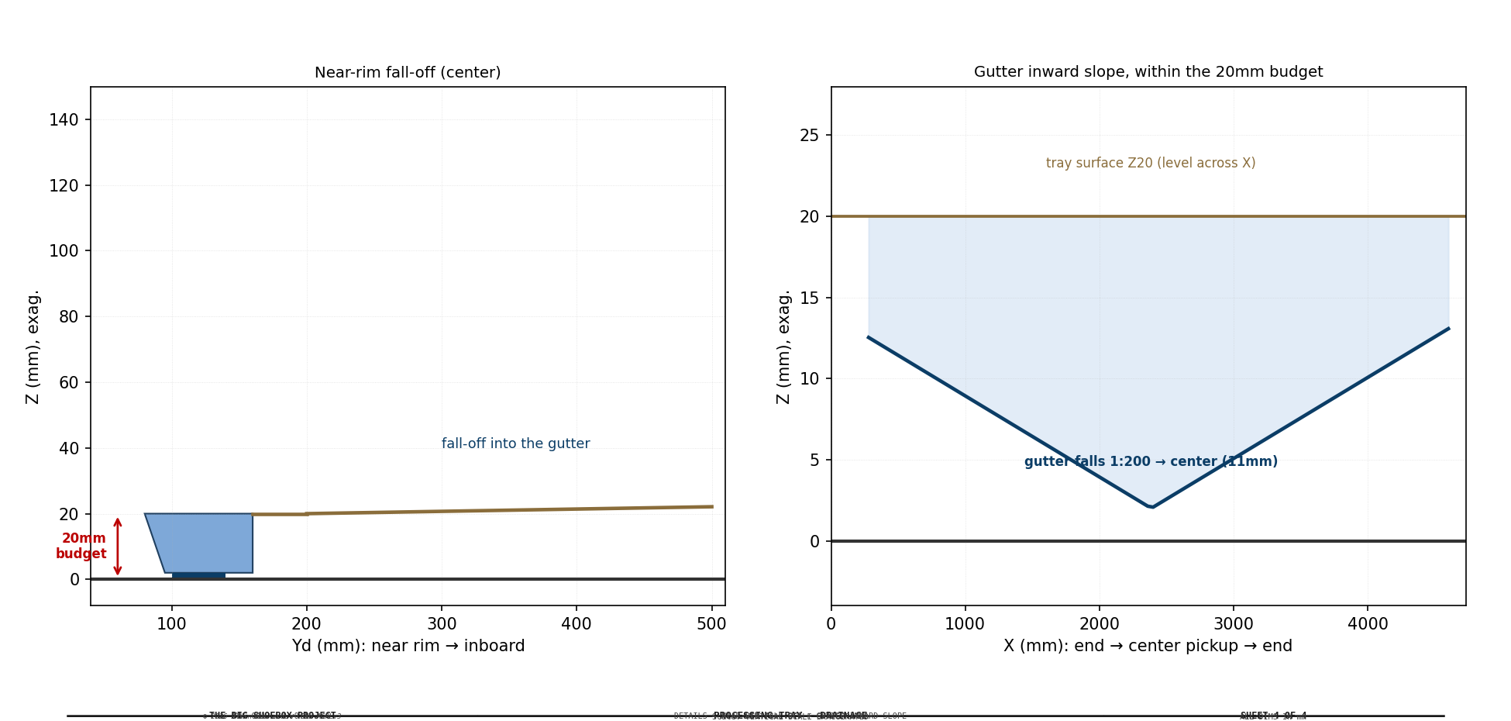
diagrams/tray-slope-sheet4.png
