alvinr/tbs/diagrams/walkway-sections-sheet1.png

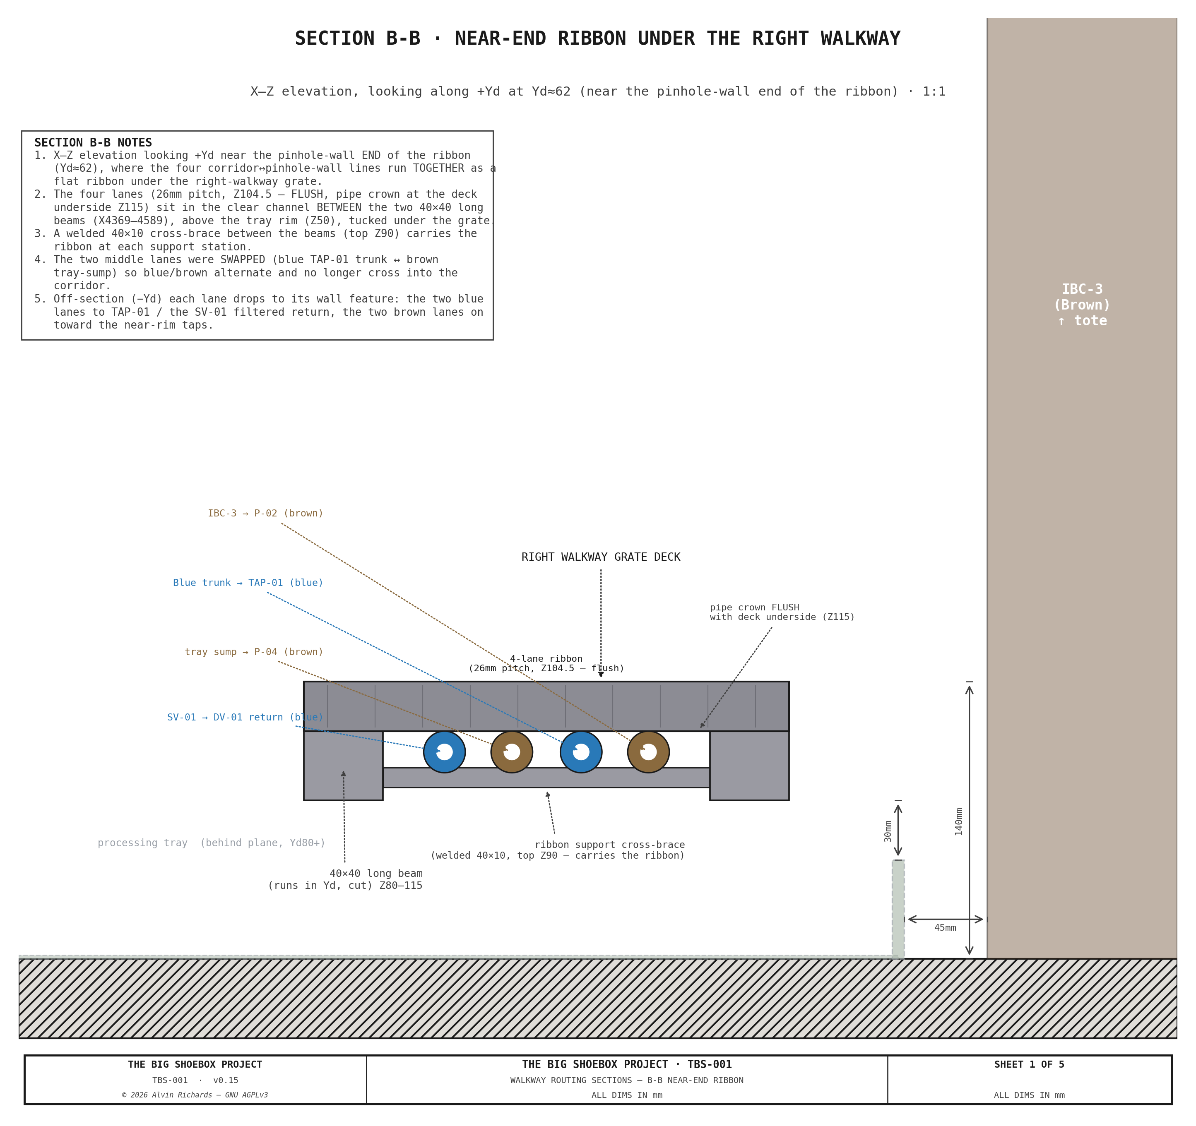
diagrams/walkway-sections-sheet1.png
