alvinr/tbs/diagrams/walkway-sections-sheet3.png

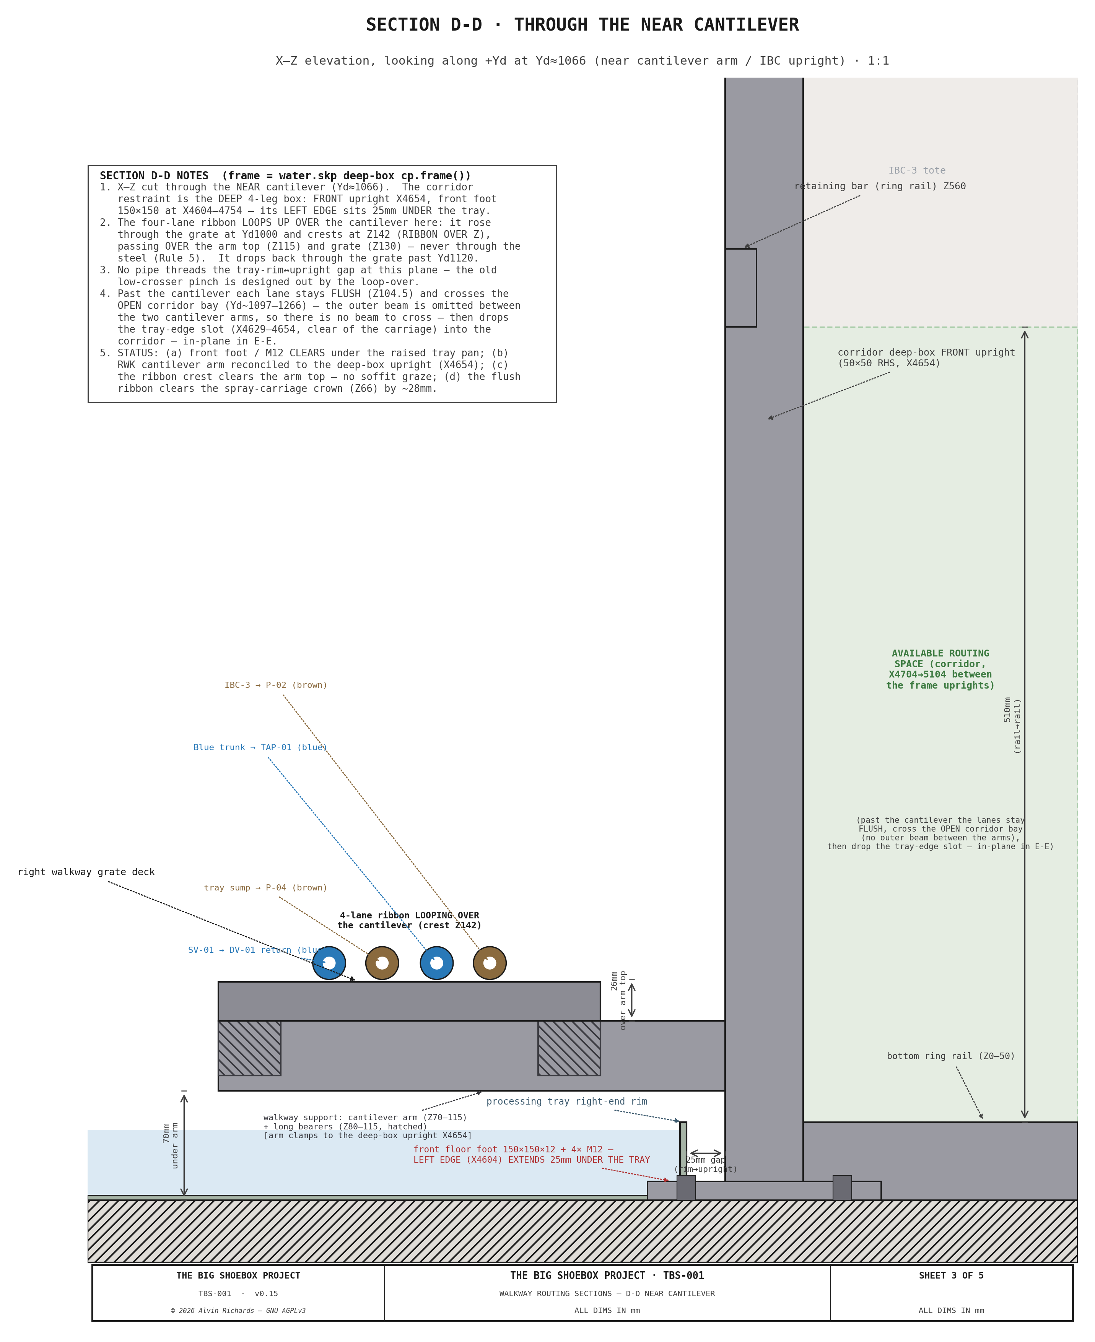
diagrams/walkway-sections-sheet3.png
