alvinr/tbs/diagrams/walkway-sections-sheet4.png

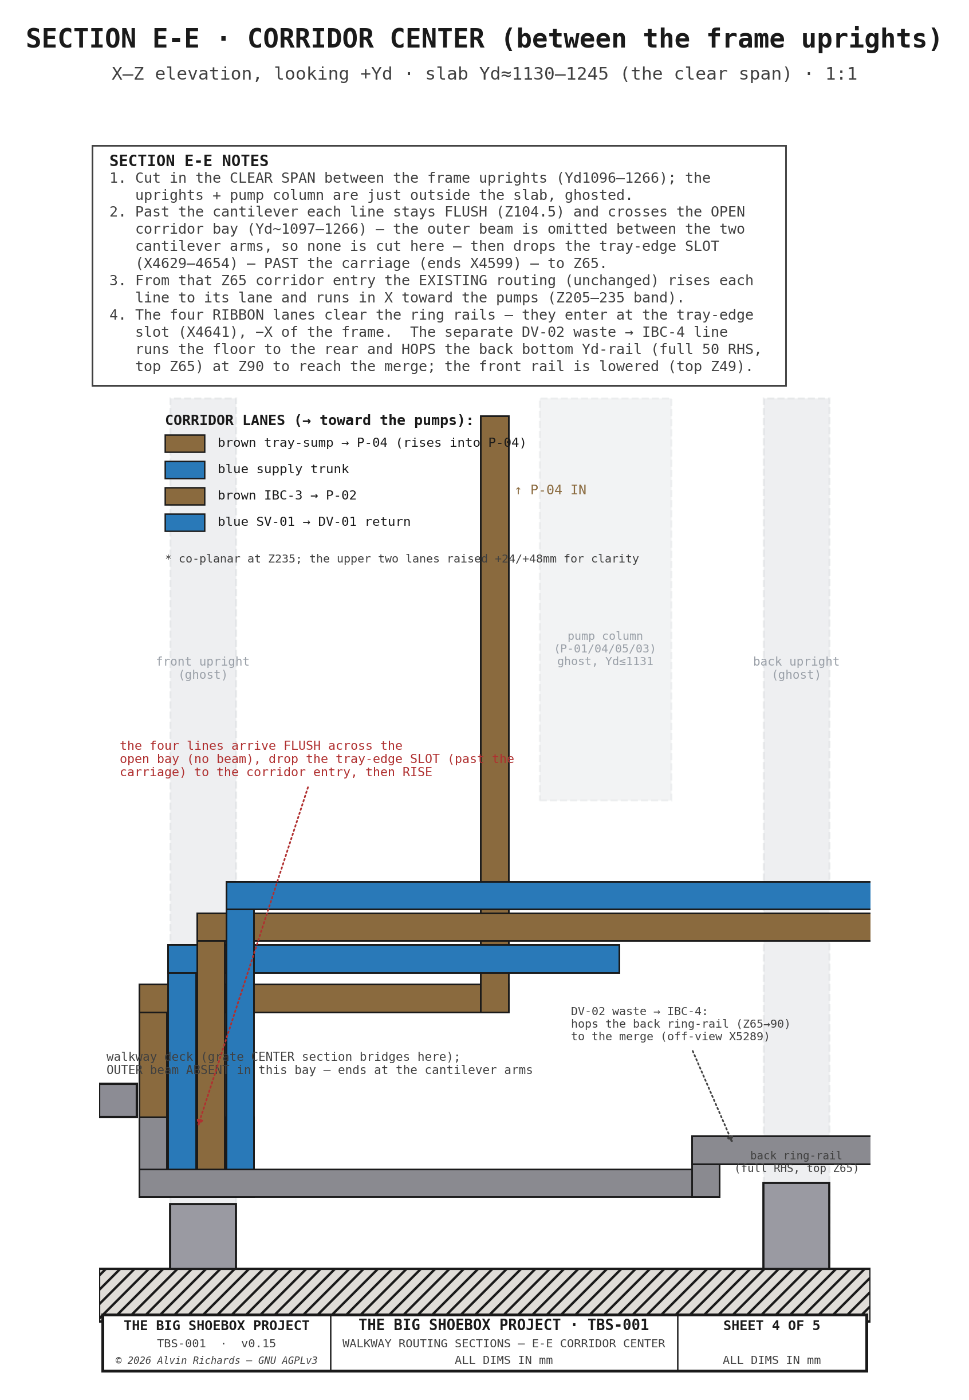
diagrams/walkway-sections-sheet4.png
