alvinr/tbs/diagrams/walkway-sections-sheet5.png

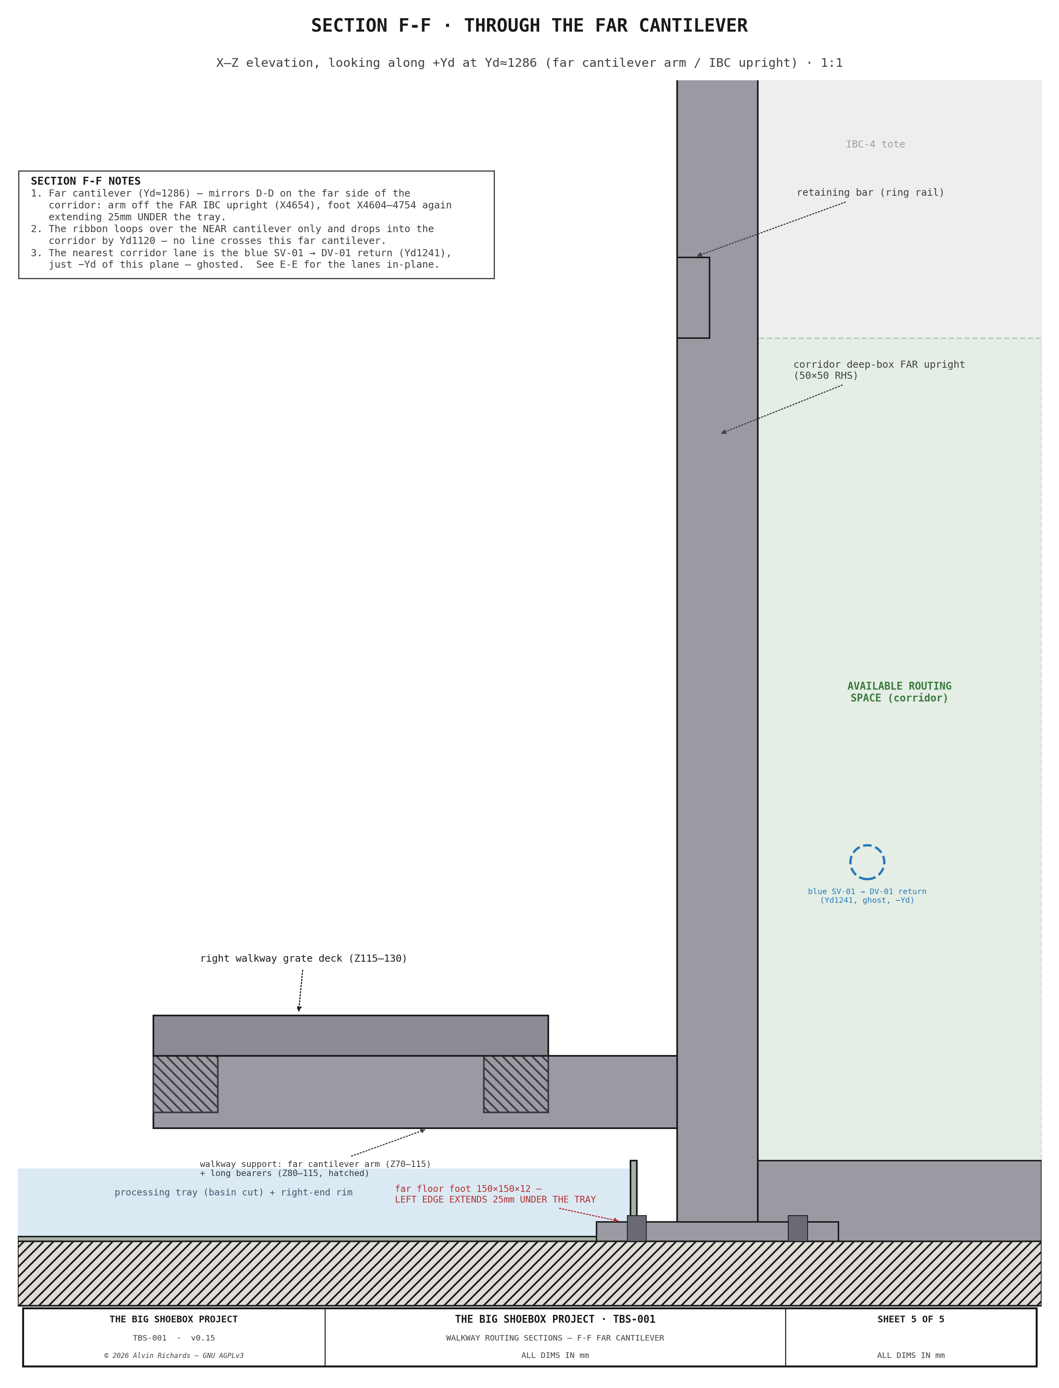
diagrams/walkway-sections-sheet5.png
