alvinr/tbs/diagrams/walkway-sections-sheet6.png

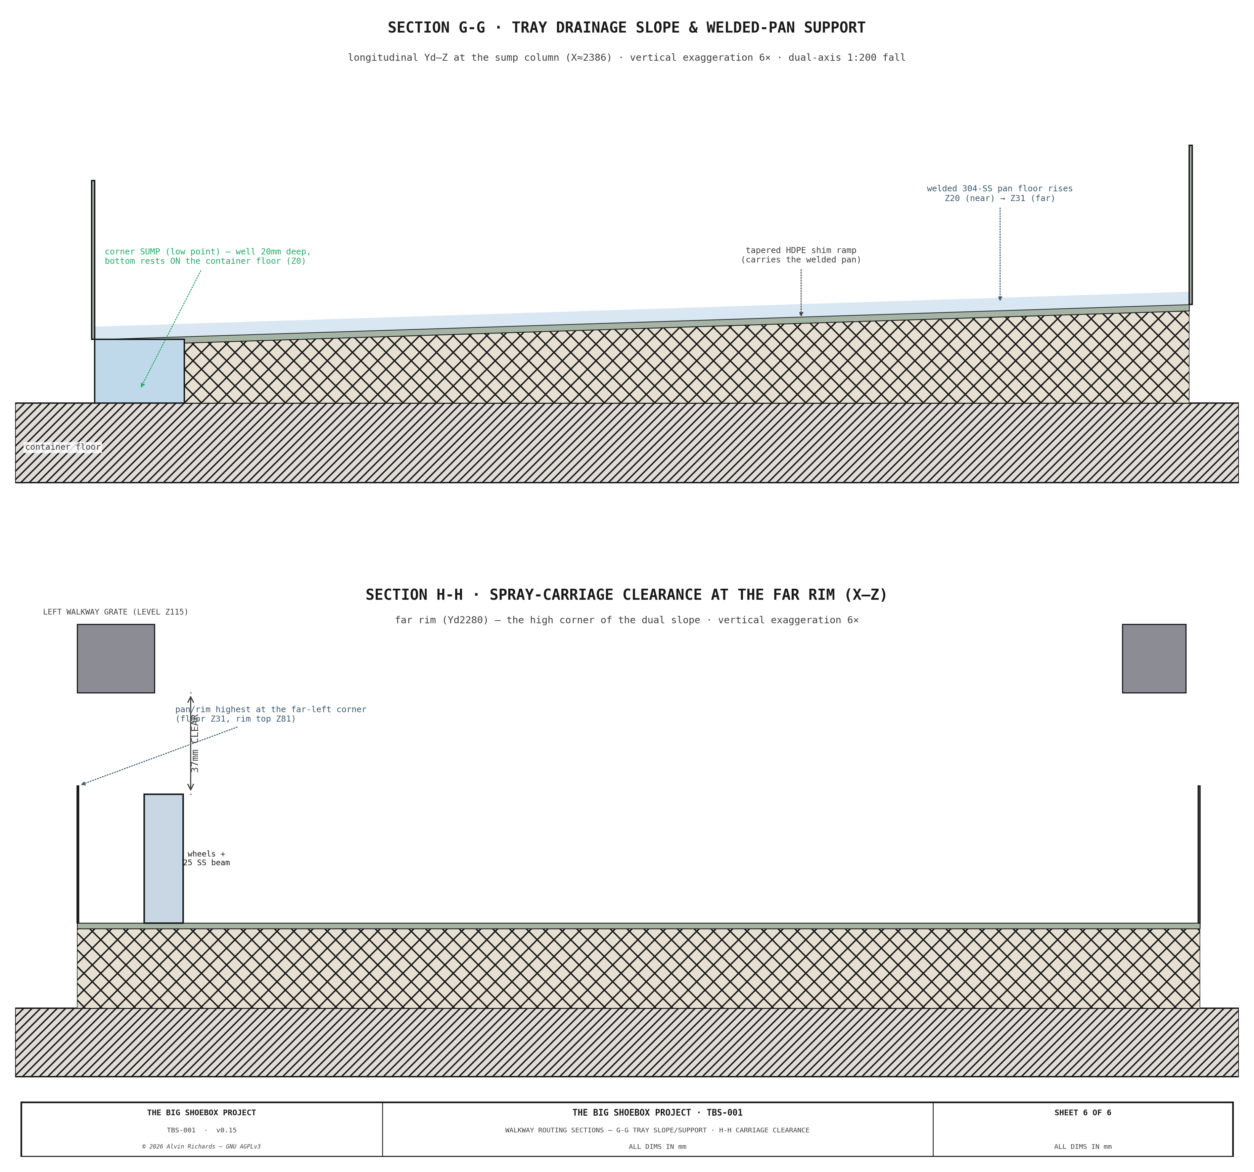
diagrams/walkway-sections-sheet6.png
