alvinr/tbs/diagrams/water-system-sheet1.png

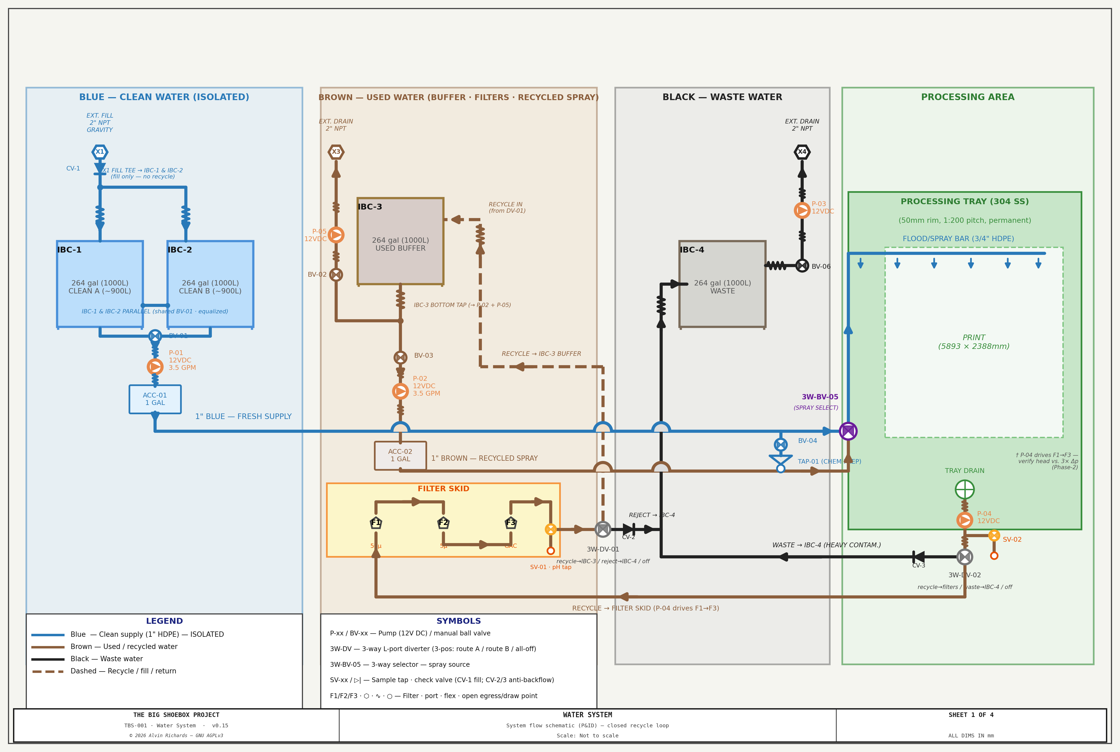
diagrams/water-system-sheet1.png
