alvinr/tbs/diagrams/water-system-sheet2.png

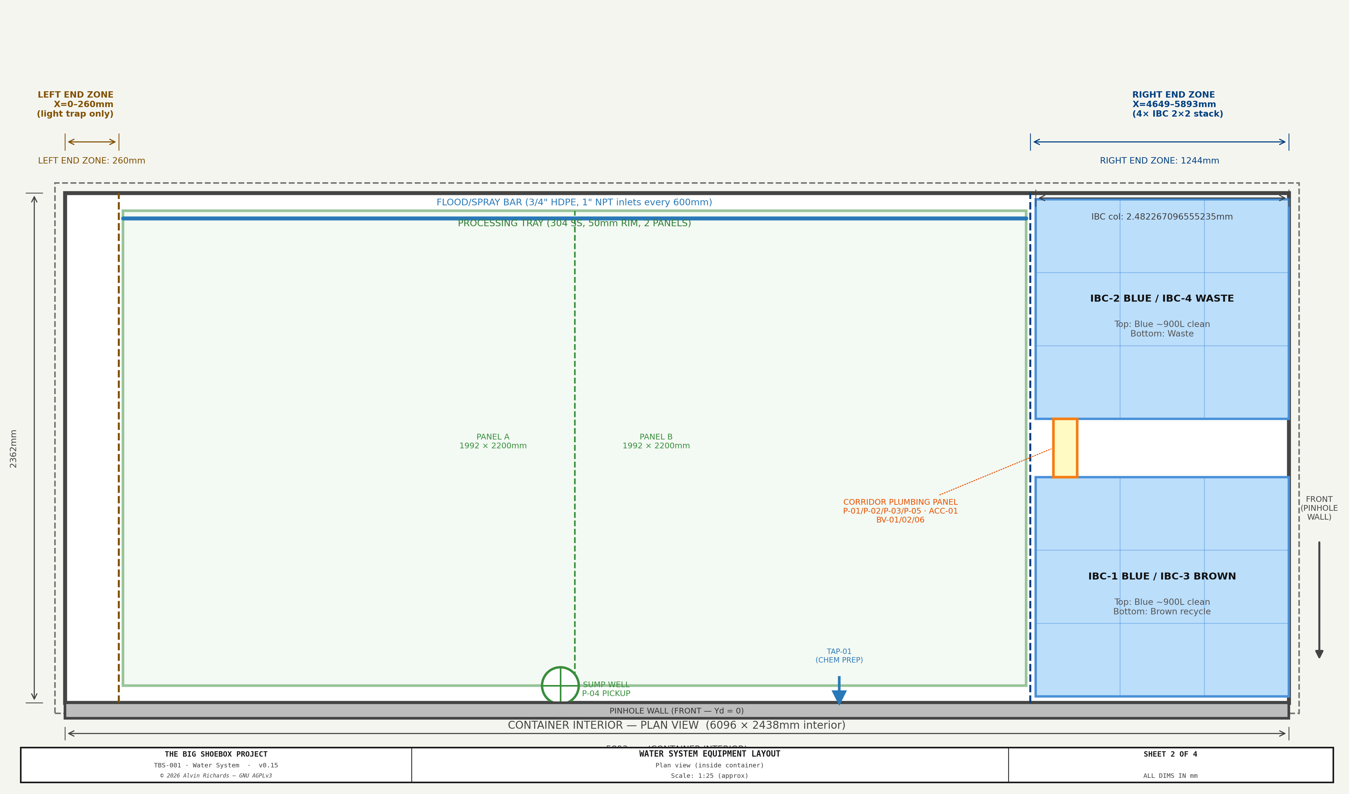
diagrams/water-system-sheet2.png
