alvinr/tbs/diagrams/water-system-sheet3.png

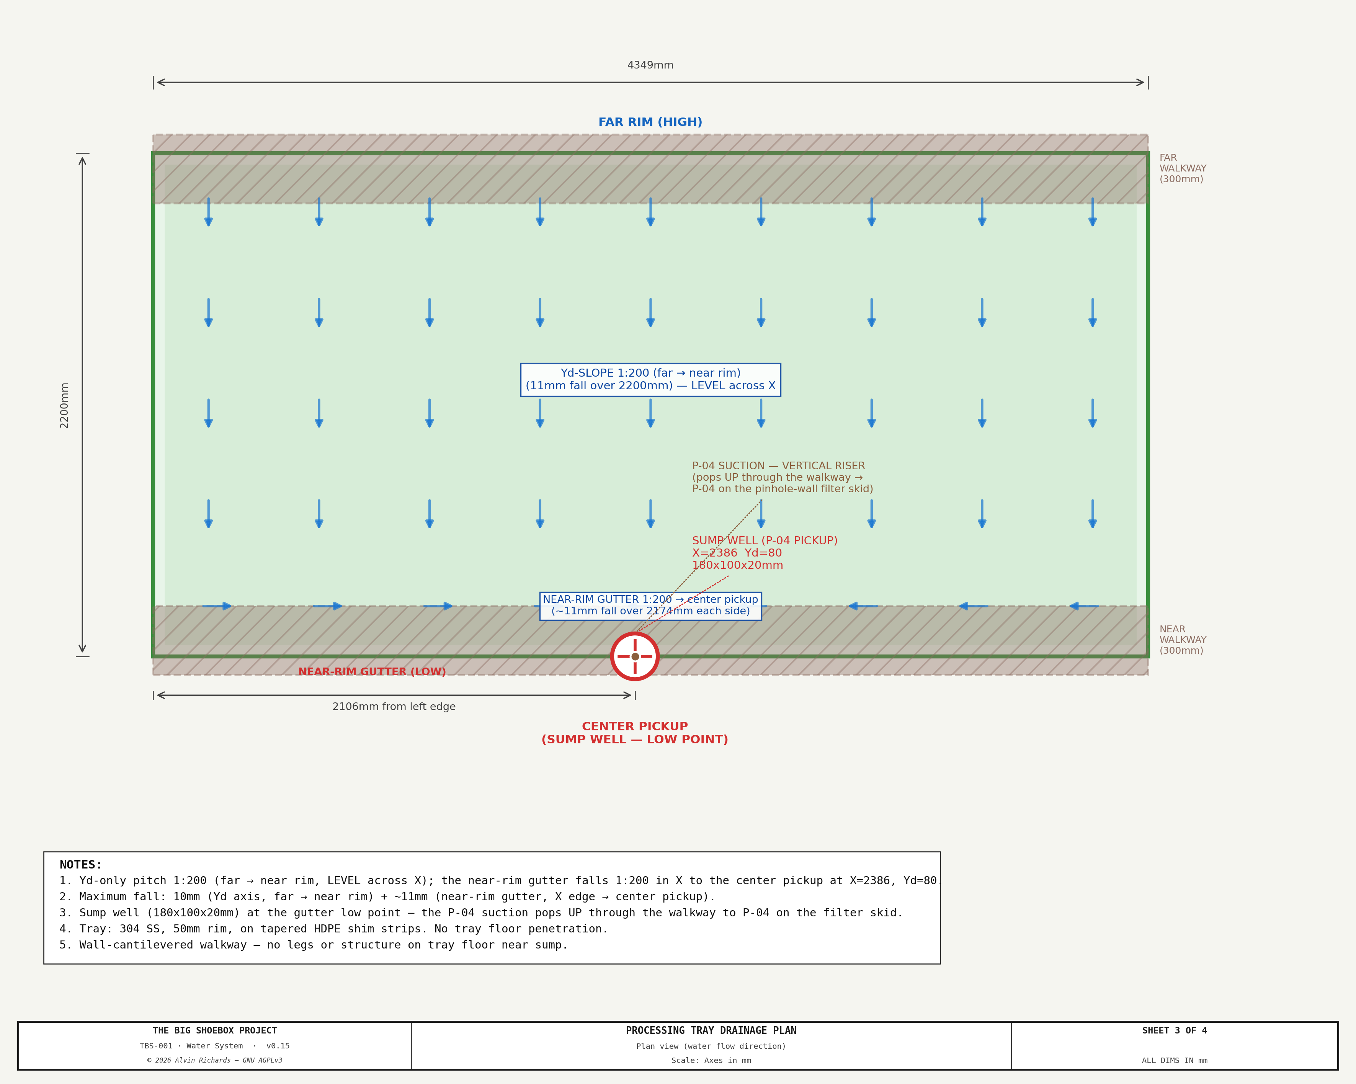
diagrams/water-system-sheet3.png
