alvinr/tbs/diagrams/water-system-sheet4.png

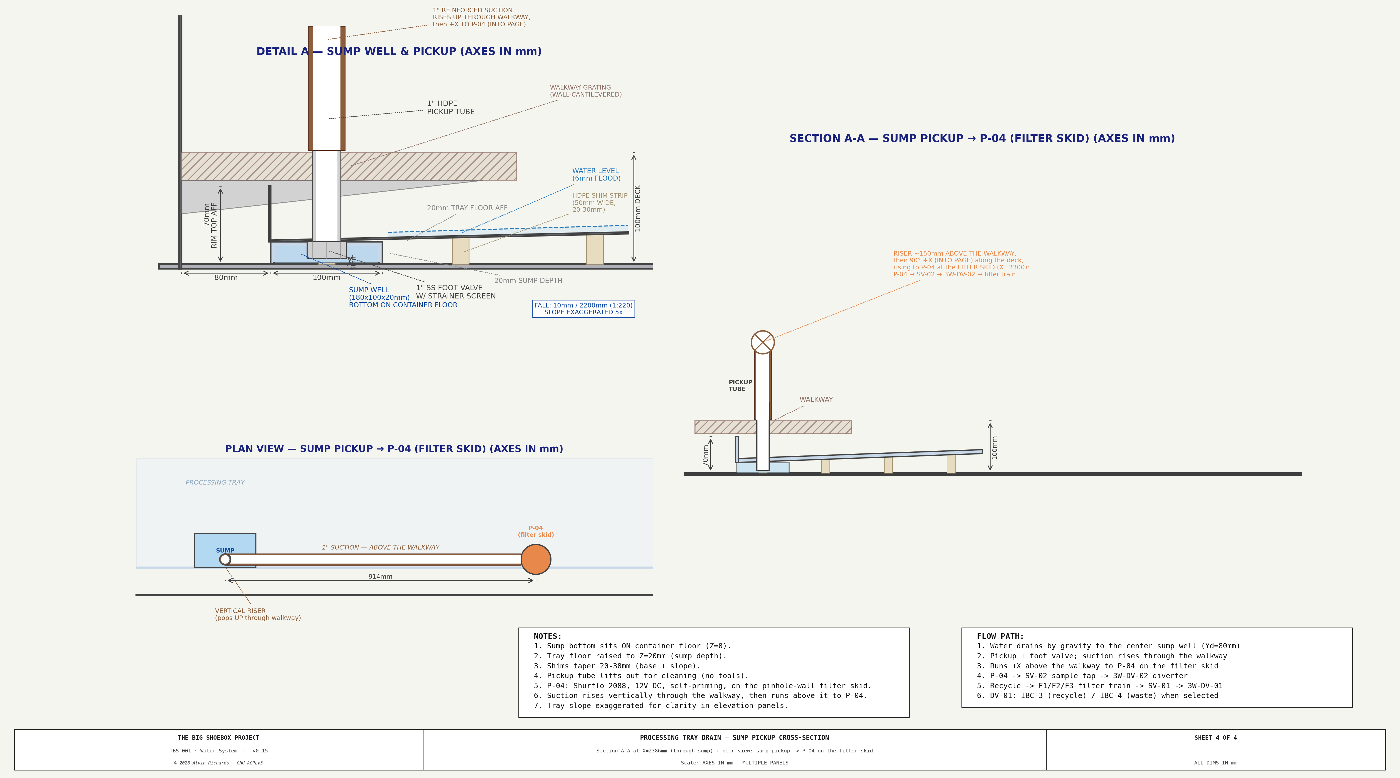
diagrams/water-system-sheet4.png
