alvinr/tbs/chemistry-shopping-list.md

<!-- SPDX-License-Identifier: AGPL-3.0-only -->
<!-- © 2026 Alvin Richards -->
# Chemistry Shopping List — Cyanotype
## Giant Pinhole Camera: Raw Material Procurement (chosen process)

**Image plane per print:** <!-- BEGIN fact:film_plane_width_mm -->4,389<!-- END fact:film_plane_width_mm --> × <!-- BEGIN fact:film_plane_height_mm -->2,094<!-- END fact:film_plane_height_mm -->mm (~<!-- BEGIN fact:image_area_sqft -->99<!-- END fact:image_area_sqft --> sq ft active film zone; container interior 5,893 × 2,388mm)  
**Run size:** 50 prints  
**Total substrate area:** ~5,800 sq ft  
**Pricing basis:** April 2026. Prices marked † are confirmed from supplier listings. All others are close estimates from current market data and should be verified before ordering. All prices USD unless noted.

---

## Alternative processes

Cyanotype is the chosen process. For the cost of the alternatives considered (gum bichromate, Van Dyke Brown, salt, Ilford RC, Liquid Light), see [Process Comparison](process-comparison.md).

---

## Shared Item: Substrate Fabric

All iron/silver processes use unbleached cotton muslin as the substrate. 50 prints at ~<!-- BEGIN fact:image_area_sqft -->99<!-- END fact:image_area_sqft --> sq ft each, plus 15% waste = ~5,980 sq ft total; at 60" (5 ft) wide fabric that is 5,980 ÷ 5 = **~1,196 linear feet ≈ 399 linear yards**.

| Item | Qty | Supplier | Unit | Units needed | Unit price | Total |
|---|---|---|---|---|---|---|
| Unbleached cotton muslin, 60" wide | ~399 yd | **Fabric Direct** | 150-yd roll | 3 rolls | ~$100/roll | ~$300 |
| OR by the yard | ~399 yd | **Fabric Wholesale Direct** | per yard | 399 | ~$0.80–$1.20/yd | ~$320–$480 |

**Fabric Direct** — 150-yard rolls of 60" unbleached muslin, medium weight  
URL: [fabricdirect.com](https://www.fabricdirect.com/shop/craft-fabric/broadcloth-and-muslin-fabric/essence-60-medium-weight-muslin-fabric-unbleached-150-yard-roll/)

**Fabric Wholesale Direct** — 60" wide unbleached cotton muslin, sold by the yard or bolt  
URL: [fabricwholesaledirect.com](https://fabricwholesaledirect.com/products/cotton-muslin-fabric-60-inches)

**Preparation required:** Pre-wash all fabric twice in hot water, no detergent. This removes sizing (starch filler) that repels sensitizer. Dry fully before coating.

---

## Process 1: Cyanotype

**50-print total (Standard ½-Ware default): ~$1,653 · ~$33/print** — the full Lean/Rich per-tier breakdown is in the shopping list below.

Cyanotype uses the **Mike Ware New Cyanotype formula** (1994) as the primary sensitizer. This replaces the traditional Herschel ferric ammonium citrate (FAC) formula with ammonium iron(III) oxalate (AmFe) and achieves **4–8× faster exposures** (baseline ~30–45 min in full sun vs 2+ hours for traditional) with denser shadows and finer tonal gradation.

**Source:** Ware, M., *Cyanotype: The History, Science and Art of Photographic Printing in Prussian Blue*, Science Museum, 1999. Formula and technical notes: [mikeware.co.uk/mikeware/New_Cyanotype_Process.html](https://www.mikeware.co.uk/mikeware/New_Cyanotype_Process.html) (free).

### Chemistry quantities — Ware New Cyanotype formula

The sensitizer is Ware's AmFe : potassium ferricyanide (Part A / Part B) with an ammonium-dichromate contrast additive:

| Reagent | Role | Notes |
|---|---|---|
| Ferric ammonium oxalate (AmFe) | Part A | requires warm water (50–60°C) to dissolve |
| Potassium ferricyanide | Part B | mixed with AmFe at Ware's 3:1 ratio |
| Ammonium dichromate | Part B additive | contrast enhancer — carcinogen, handle with care (see below) |
| Distilled / DI water | solvent | tap water + DI filter adequate; warm for Part A |

The **per-print masses are under trial** — two wet-on-wet coats at a diluted Ware strength, concentration-tier dependent — so they are not yet pinned; see [Sensitizer Trials](sensitizer-trials.md). The **per-tier order quantities and cost** (Lean / Standard / Rich) are in the shopping list below.

> **⚠ Ammonium dichromate** is a known carcinogen (Category 1A) and oxidizer. Quantities here are small (~10g per print, 1 kg for 50 prints). Wear nitrile gloves and mix in ventilated area. Store away from flammables. No hazmat shipping at this quantity (< 1 kg per shipment from Photographers' Formulary).

### Shopping list — Ware New Cyanotype (primary)

*Preliminary — quantities and costs are **subject to the [Sensitizer Trials](sensitizer-trials.md)**; the **Standard ½-Ware** tier is the working default. Generated from the parts registry.*

<!-- BEGIN parts:chemistry -->
| Reagent | Supplier | Lean ⅓-Ware | Standard ½-Ware (default) | Rich full-Ware |
|---|---|---|---|---|
| Ferric ammonium oxalate (AmFe) | Artcraft Chemicals | 11.4 kg / $732 | 17.1 kg / $1,098 | 34.2 kg / $2,196 |
| Potassium ferricyanide | Artcraft Chemicals | 3.8 kg / $194 | 5.7 kg / $291 | 11.4 kg / $582 |
| Ammonium dichromate | Artcraft Chemicals | $25 | $25 | $25 |
| **Chemistry subtotal** | | **$951** | **$1,414** | **$2,802** |
| Unbleached muslin (substrate) | Fabric Direct | $300 | $300 | $300 |
| **Total (50 prints)** | | **$1,251** | **$1,714** | **$3,102** |
| **Per print** | | **$25** | **$34** | **$62** |
<!-- END parts:chemistry -->

*No fixer required. Development in plain cold water. No darkroom required for processing.*

### Traditional Herschel formula (alternative — if AmFe unavailable)

Slower (4–8× longer exposures), but simpler preparation — FAC dissolves at room temperature.

| Item | Supplier | URL | Unit size | Units | Unit price | Total |
|---|---|---|---|---|---|---|
| Ferric Ammonium Citrate, green, 1 lb | **Photographers' Formulary** | [stores.photoformulary.com/ferric-ammonium-citrate-green](https://stores.photoformulary.com/ferric-ammonium-citrate-green/) | 454 g (1 lb) | 31 | ~$30† | ~$930 |
| Potassium Ferricyanide | Same as above | — | — | — | — | — |

---

## Source References

1. [Mike Ware — The New Cyanotype Process](https://www.mikeware.co.uk/mikeware/New_Cyanotype_Process.html) — AmFe sensitizer formula, the 3:1 ratio, and dichromate contrast (also Ware, M., *Cyanotype: The History, Science and Art of Photographic Printing in Prussian Blue*, Science Museum, 1999).
2. Muslin: [Fabric Direct](https://www.fabricdirect.com/shop/craft-fabric/broadcloth-and-muslin-fabric/essence-60-medium-weight-muslin-fabric-unbleached-150-yard-roll/) (150-yd rolls) · [Fabric Wholesale Direct](https://fabricwholesaledirect.com/products/cotton-muslin-fabric-60-inches) (by the yard).
3. Reagents: [Photographers' Formulary](https://stores.photoformulary.com/) (AmFe, ammonium dichromate, FAC) · Bostick & Sullivan (potassium ferricyanide).
4. [Process Comparison](process-comparison.md) — cost of the rejected alternative processes.
