alvinr/tbs/parts-worklist.csv

key | desc | system | type | qty | unit | flags | hint | cur_supplier | cur_part_no | cur_url | cur_dims | cur_spec | cur_low | cur_high | new_supplier | new_part_no | new_url | new_dims | new_low | new_high | checked_date | note
cooler-power-cable | Cooler external power cable | ventilation | electrical-distribution | 1 | ea | SOURCE-PRICE | source at Waytek Wire: pin the listing (SKU/ASIN + URL) + confirm a firm price (single value, not a range) in new_low/new_high | Waytek Wire |  |  |  | CRIMP-YOUR-OWN (no retail SKU): 1.5m, 14 AWG 2-cond + Deutsch DT 2-pin plug crimped each end (connectors per deutsch-dt-2pin). Self-assembled; $20 is the wire+terminal material estimate, accepted (2026-10-02). | 20 | 20
