alvinr/tbs/diagrams/assembly-fab-sheet1.png

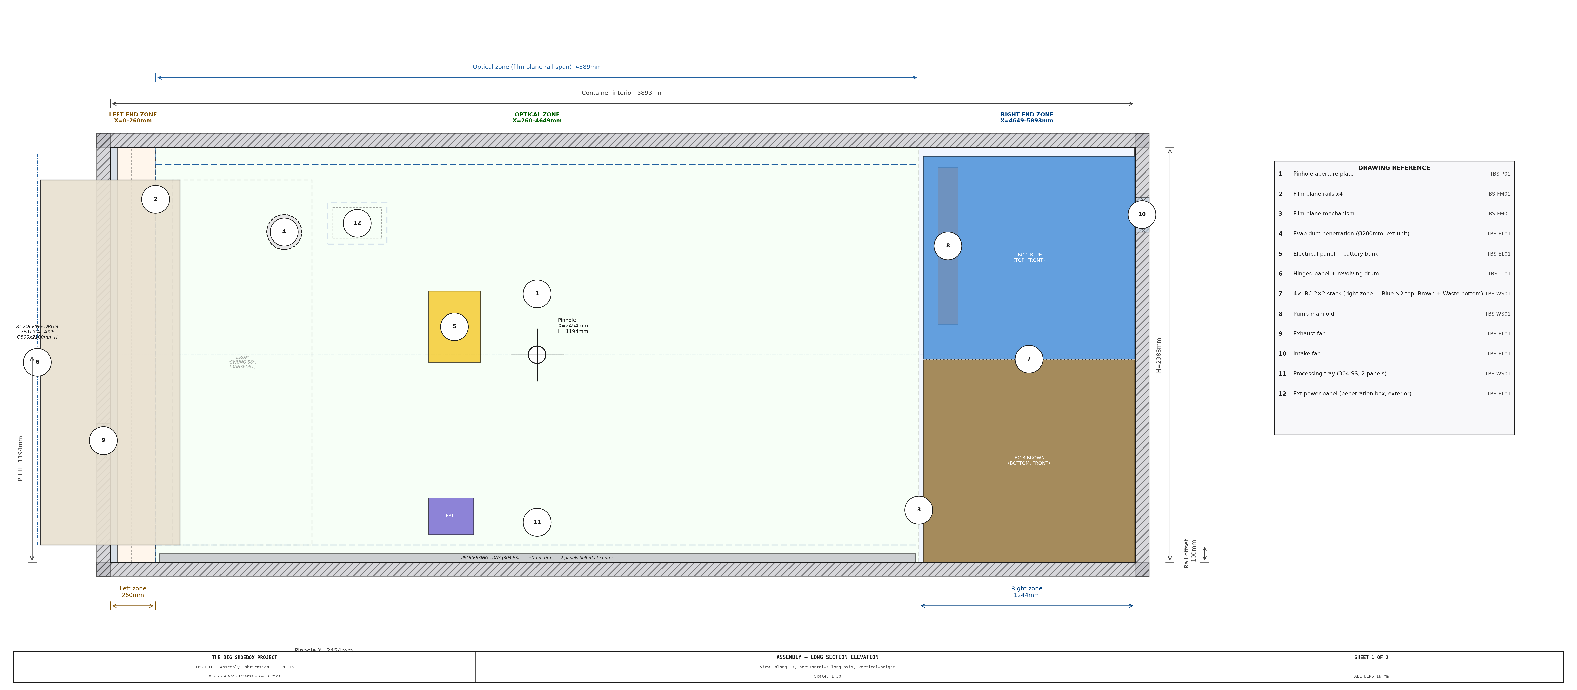
diagrams/assembly-fab-sheet1.png
