alvinr/tbs/diagrams/assembly-fab-sheet2.png

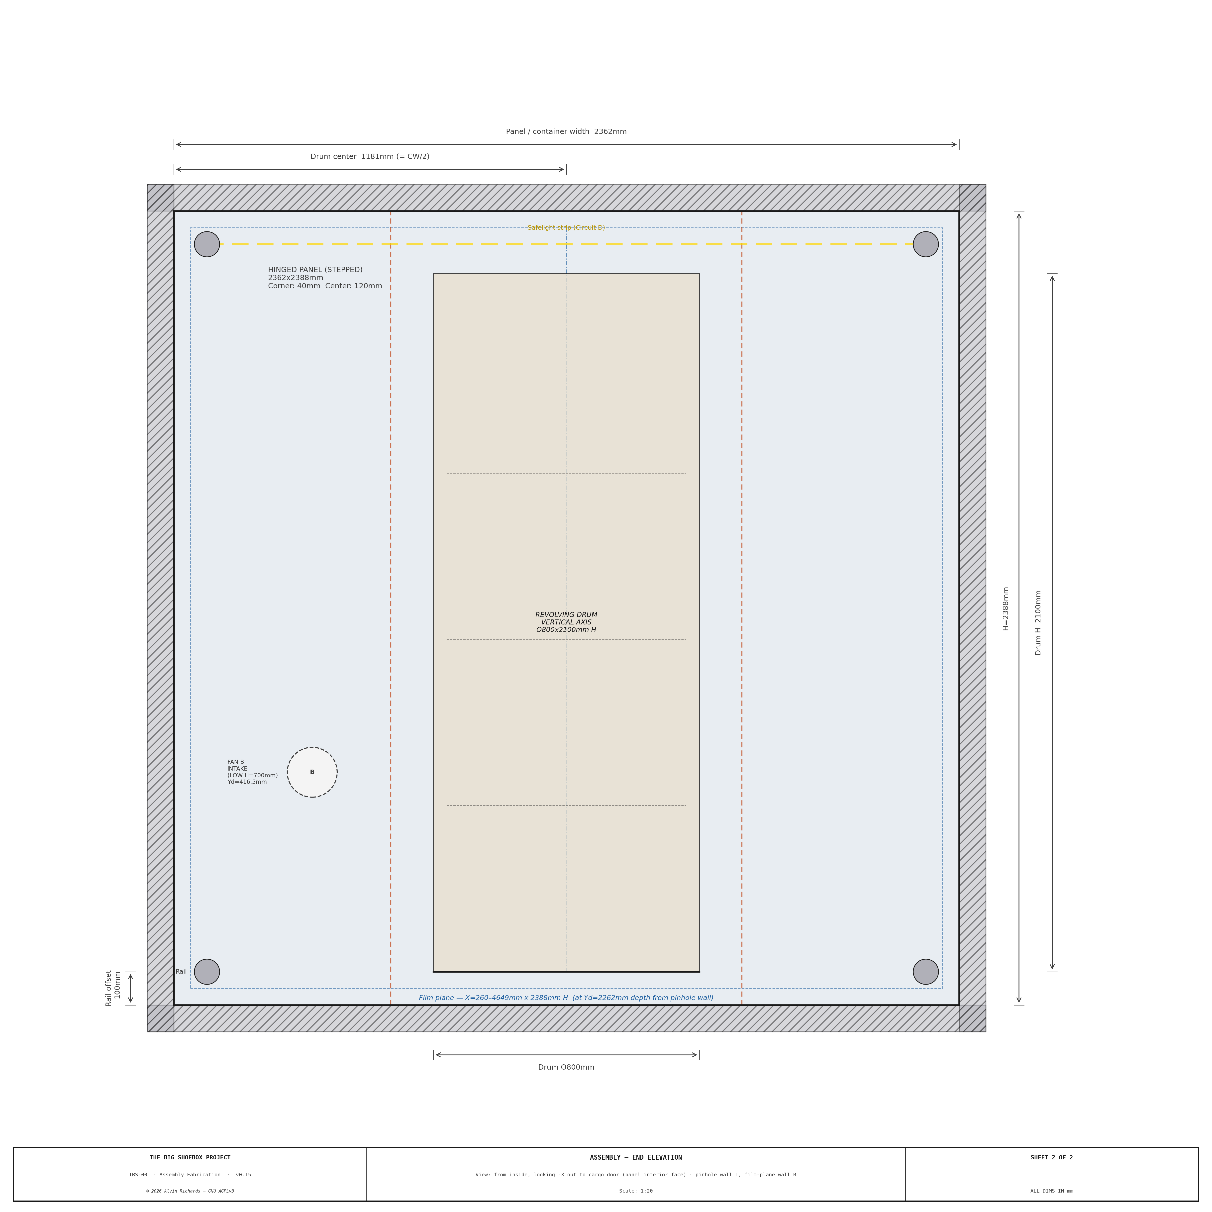
diagrams/assembly-fab-sheet2.png
