alvinr/tbs/diagrams/assembly-overview-fp.png

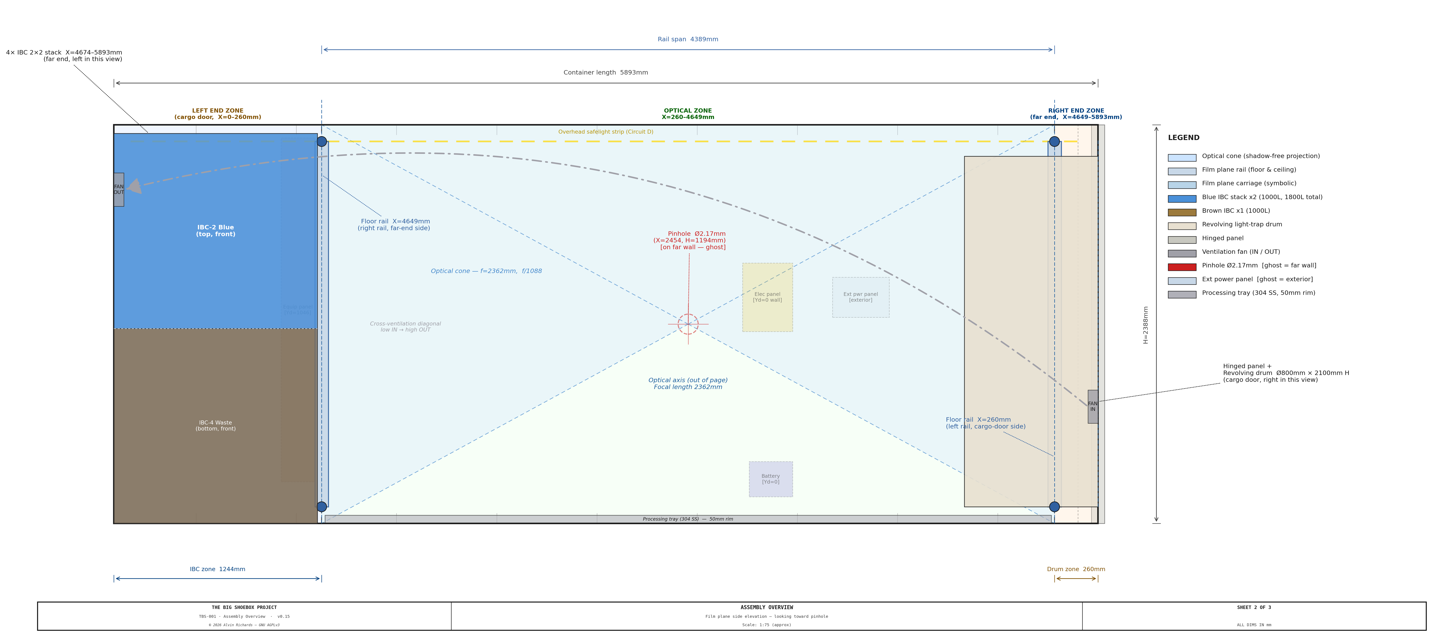
diagrams/assembly-overview-fp.png
