alvinr/tbs/diagrams/assembly-overview.png

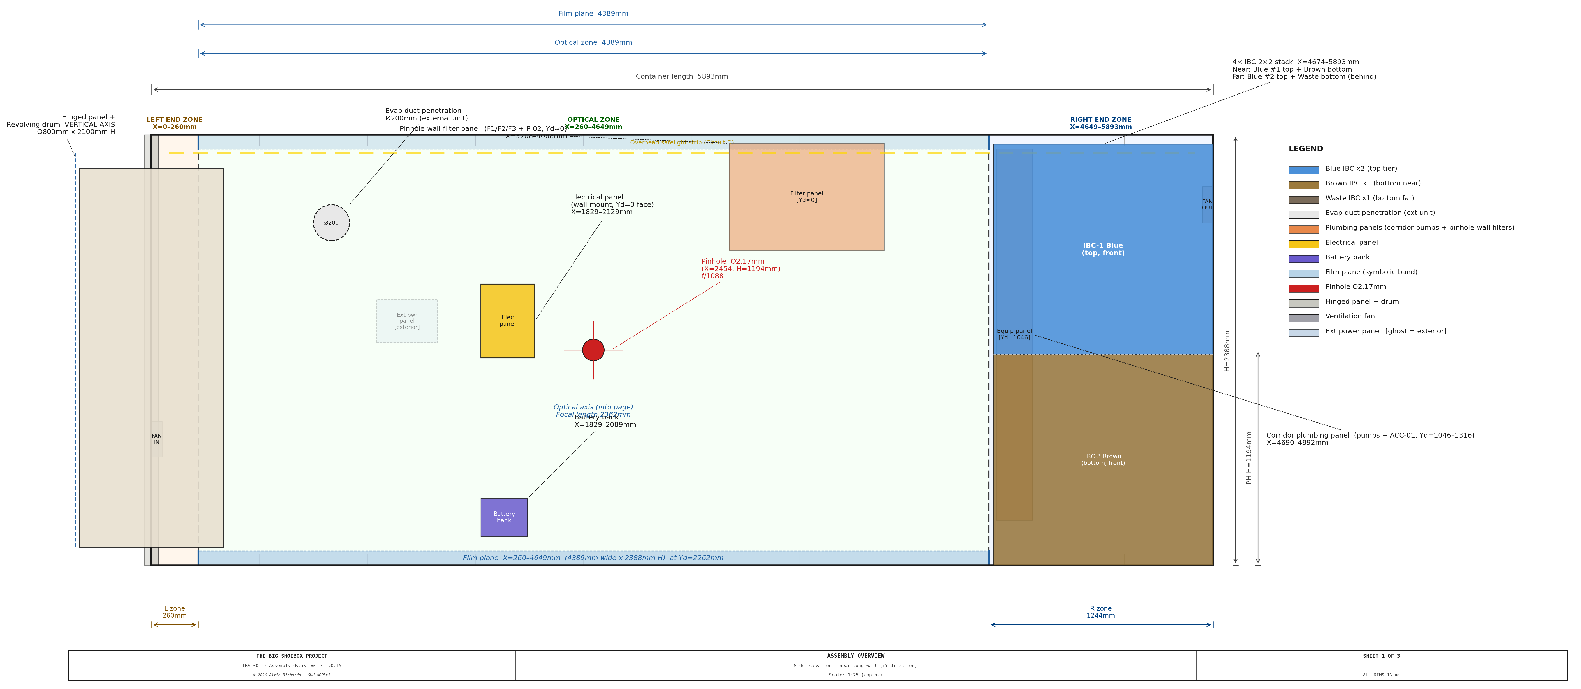
diagrams/assembly-overview.png
