alvinr/tbs/src/models/generate_pinhole_water_panel.py

#!/usr/bin/env python3
# SPDX-License-Identifier: AGPL-3.0-only
# © 2026 Alvin Richards
"""generate_pinhole_water_panel.py — EXPLORATORY massing (pinhole-wall-mount branch).

Block massing of the wet end (pumps + ACC + filters) wall-mounted on the PINHOLE
WALL (Yd=0) in the clear band X2700-4674, arranged by the RAKE-BY-DEPTH principle:
the deepest items (Big Blue filters) ride HIGH, the shallow items (pumps, ACC) sit
LOW, keeping the torso band clear.  Includes the (widened) near-walkway deck and a
1750mm person for scale.  No plumbing yet — geometry feasibility only.

    python3 src/models/generate_pinhole_water_panel.py --send          # build in the live SketchUp doc
    python3 src/models/generate_pinhole_water_panel.py --save          # write src/models/water.rb (offline, verifiable)
    python3 src/models/generate_pinhole_water_panel.py --send --save   # build the live doc + write water.rb (ALVIN saves the .skp)
"""
import sys, os, argparse
_HERE = os.path.dirname(os.path.abspath(__file__))
_ROOT = os.path.dirname(os.path.dirname(_HERE))   # repo root (src/models -> src -> root)
sys.path.insert(0, _HERE)
import generate_sketchup_model as ov
import generate_walkway_model as wm   # walkway builders (Phase 1)
import tbs_draw as draw                          # shared drawing/material primitives
import generate_corridor_water_panel as cp
import generate_spraybar_model as sb        # owns spray_bar() (Phase 1)
import generate_ibc_model as ib                 # owns ibc_stack() (Phase 1)        # the new corridor plumbing panel (same connected system)

# ── Sketchfab upload metadata (stamped onto the model on every --send) ────────
#    Read from the live water.skp 2026-07-03 (the model's own current title/description).
SF_TITLE = "TBS-001 Water Model"
SF_TAGS  = "sketchup"
SF_DESC  = (
    "The camera operates in remote locations with no municipal water or drainage. "
    "This document specifies a self-contained three-circuit water system that:\n\n"
    "Stores sufficient clean water for 9–14 full-size prints between resupply runs on "
    "fresh Blue alone (~14 prints once Brown wash-2 recycling is counted — see §below) "
    "Recycles used wash water through a three-stage filter train, extending usable supply by "
    "approximately 40% Contains all waste water in a closed, transportable IBC for proper "
    "off-site disposal Runs entirely on 12V DC, compatible with a solar/battery off-grid power system."
)

# ── band + wall ──────────────────────────────────────────────────────────────
X0, X1 = 2700, 4674            # wet-end clear mounting band on the pinhole wall (Yd0)
WALL_X0, WALL_X1 = 0, ov.C_LEN # 0..5893 — the FULL pinhole wall (context spans the whole length)
C_HGT, C_WID = ov.C_HGT, ov.C_WID
DECK_Z = ov.WALKWAY_H          # 130
DECK_W = ov.WALKWAY_W          # 300 — standard near walkway (evaluate whether it fits)
VIEW_DEPTH = DECK_W + 300      # 600 — show from the wall out to 300mm PAST the walkway, then stop

C_PERSON = "#806040"
C_DECK   = "#9C7B4D"


def context():
    """Pinhole wall + a FULL-depth floor/ceiling (so the full IBC tanks sit on it), with
    a faint marker line at the 300mm-past-walkway depth for reference."""
    bx, bw = WALL_X0, WALL_X1 - WALL_X0          # the FULL pinhole wall length
    p = []
    p.append(draw.ruby_box("Pinhole wall", bx, -ov.WALL_T, 0, bw, ov.WALL_T, C_HGT,
                         color=draw.C_SHELL, alpha=0.30))
    p.append(draw.ruby_box("Floor", bx, 0, -ov.WALL_T, bw, C_WID, ov.WALL_T,
                         color=draw.C_SHELL, alpha=0.16))
    # (container ceiling omitted in this view)
    # (depth-reference plane at Yd=VIEW_DEPTH removed 2026-08-15 — it read as a stray blue rectangle in the
    #  plumbing deliverable; it was only a viewing scaffold, not a real part.)
    return "\n".join(p)


# Cascade hint: walkway_full() reuses wm.walkways(), which draws the near-wide bump-out and the
# muslin-drop notches — so water.skp inherits WALKWAY_NEAR_WIDE_X_R, WALKWAY_MUSLIN_NOTCH_L_X0,
# WALKWAY_MUSLIN_NOTCH_R_X0. Named here so the grep-based missing-cascade check flags water.skp
# when any of them change (the deps are indirect via ov.*, which the import scan can't see).
def walkway_full():
    """Real walkway geometry so the cantilevers + brackets read: perimeter decks
    (near with punch-out, stopping at the IBC; left; right — FAR deck erased post-build),
    the wall gusset brackets, and the IBC-end cantilever arms."""
    p = []
    for fn in ("walkways", "walkway_brackets", "ibc_cantilever_arms"):
        try:
            r = getattr(wm, fn)()      # walkway builders now owned by the walkway model (Phase 1)
            p.append("\n".join(r) if isinstance(r, (list, tuple)) else r)
        except Exception as e:
            print(f"  (skip {fn}: {e})", file=sys.stderr)
    return "\n".join(p)


def film_plane_beams():
    """The RIGHT-side (IBC-end) film-plane corners (BR + TR) — the REAL detailed mechanism reused verbatim
    from the dedicated model (fpm.corner()): web-vertical 3×1.5 U-channel rails (flanged, end-flanges) +
    skate/rollers + carriage plate + cam-brake + cross-slides + U-joint + 304 corner plate. ONE source with
    overview/walkway. The LEFT-side (cargo-door end) corners are omitted in this view to keep the wet end
    readable. Late import breaks the fpm→ov cycle; fpm.corner() emits ov.ruby_* at the shared coords."""
    import generate_film_plane_mechanism_model as fpm
    return "\n".join([
        fpm.corner("BR", fpm.X_R, fpm.PZ0, fpm.PZ_HB_BOT, -1, "R"),
        fpm.corner("TR", fpm.X_R, fpm.PZ1, fpm.PZ_HB_TOP, -1, "R"),
    ])


def deck():
    """Near walkway along the pinhole wall — STOPS at the IBC (does not pass it), with
    its punch-out (widened to WALKWAY_NEAR_WIDE_W over X1155-2629)."""
    p = []
    p.append(draw.ruby_box("Near walkway (stops at IBC)", WALL_X0, 0, DECK_Z - 15,
                         ov.IBC_COL_X - WALL_X0, DECK_W, 15, color=C_DECK, alpha=0.9))
    p.append(draw.ruby_box("Near walkway punch-out", ov.WALKWAY_NEAR_WIDE_X_L, DECK_W, DECK_Z - 15,
                         ov.WALKWAY_NEAR_WIDE_X_R - ov.WALKWAY_NEAR_WIDE_X_L,
                         ov.WALKWAY_NEAR_WIDE_W - DECK_W, 15, color=C_DECK, alpha=0.9))
    return "\n".join(p)


def ibc_slice():
    """A thin slice of the near IBC column at its front face (X=IBC_COL_X) — shows the
    space to the LEFT (high X) is taken, so the wet end can't extend past it."""
    return draw.ruby_box("IBC slice (space taken)", ov.IBC_COL_X, ov.BLUE_IBC_Y, 0,
                       120, VIEW_DEPTH - ov.BLUE_IBC_Y, 2 * ov.IBC_H_1000,
                       color=draw.C_IBC_BLUE, alpha=0.30)


# Other equipment ALREADY mounted on the pinhole wall (Yd0) — the wet-end layout has to
# coexist with these.  electrical() = panel + inverter + batteries.
OTHER_WALL_EQUIP = [("Electrical (panel/inverter/batteries)", "electrical")]

# Context-muting parameters — ONE place so every muted system matches: the IBC tanks
# (built muted via ib.ibc_stack(mute=)) and the in-place-muted context tags below all use
# these.  Desaturate the color this fraction toward draw.MUTE_NEUTRAL, at this alpha.
MUTE_DESAT, MUTE_ALPHA = 0.65, 0.18
# Context systems shown as a quiet faded backdrop (NOT the key plumbing/kit/supply) — desaturated
# in place keeping a faint tint.  Everything that is enclosure/structure rather than a water
# component is muted, so in EVERY scene only the plumbing reads boldly (easier to validate).
# NB: "Corridor Panel" is NOT muted — the equipment panel (shirt + backing) is drawn SOLID in every
# scene (a solid backdrop behind the pumps reads better than the faint ghost; 2026-08-14).
MUTE_TAGS = ["Pinhole Equipment", "Processing Tray", "IBC Frame", "Corridor Frame",
             "Walkway", "Film Plane", "Pinhole", "Backing"]


def other_equipment():
    # Interior EP (fuse block / busbars / MPPT / battery + contactor) as pinhole-wall context. The
    # external power panel AND the evap cooler — both drawn by em.external_panel() — are DROPPED from
    # the water model (cleanup 2026-07-07). The overview no longer calls this (it draws its own EP).
    import generate_electrical_model as em
    return "\n".join([em.power_core(external_links=False), em.battery()])


# spray_bar() moved to generate_spraybar_model.py (sb.spray_bar()) — the single owner.


def processing_tray(alpha=None):
    """Processing tray — RAISED, dual-axis-sloped 304 SS welded pan (tilted floor + rim)
    on a tapered HDPE shim base, holding a translucent chemistry bath.  The low corner
    (near-right / IBC side = the sump) sits at Z=ov.PROC_TRAY_FLOOR_Z_LOW so the sump bottom
    rests on the container floor; the pan rises 1:200 in BOTH axes to the far-left corner
    (see ov.tray_floor_z / tray_rim_top_z).

    SINGLE OWNER of the tray geometry — the spray-bar model calls this with `alpha` set to draw
    the SAME sloped pan as a faint CONTEXT ghost (so the gantry reads inside the real tray).
    `alpha=None` (default) = solid detail — byte-identical to the original overview output."""
    xl, xr = ov.PROC_TRAY_X_L, ov.PROC_TRAY_X_R
    yn, yf = ov.PROC_TRAY_YD_NEAR, ov.PROC_TRAY_YD_FAR
    tray_w, tray_d = xr - xl, yf - yn
    sheet_t, rim_t = 2, 2
    zc = ov.PROC_TRAY_FLOOR_Z_LOW                       # low-corner floor top = shim base top
    a_shim = 0.9 if alpha is None else alpha         # ghost mode fades every part uniformly
    a_bath = 0.45 if alpha is None else alpha

    parts = []
    # Tapered HDPE shim base — raises the pan so the 20mm sump well bottom rests on Z0
    parts.append(draw.ruby_box("Tray Shim Base",
                          xl, yn, 0, tray_w, tray_d, zc - sheet_t,
                          color="#D8CFBC", alpha=a_shim))
    # Welded pan FLOOR — dual-axis-tilted plane (two triangles at the true corner Z's)
    c_nl = [xl, yn, ov.tray_floor_z(xl, yn)]
    c_nr = [xr, yn, ov.tray_floor_z(xr, yn)]
    c_fr = [xr, yf, ov.tray_floor_z(xr, yf)]
    c_fl = [xl, yf, ov.tray_floor_z(xl, yf)]
    parts.append(draw.ruby_tri("Processing Tray Floor A", c_nl, c_nr, c_fr, -sheet_t, color=draw.C_TRAY, alpha=alpha))
    parts.append(draw.ruby_tri("Processing Tray Floor B", c_nl, c_fr, c_fl, -sheet_t, color=draw.C_TRAY, alpha=alpha))
    # Rims — walls on the raised, tilted pan (each placed at the local floor Z for its edge)
    znr = ov.tray_floor_z((xl + xr) / 2, yn); zfr = ov.tray_floor_z((xl + xr) / 2, yf)
    zlr = ov.tray_floor_z(xl, (yn + yf) / 2); zrr = ov.tray_floor_z(xr, (yn + yf) / 2)
    parts.append(draw.ruby_box("Tray Rim Near", xl, yn, znr, tray_w, rim_t, ov.PROC_TRAY_RIM, color=draw.C_TRAY, alpha=alpha))
    parts.append(draw.ruby_box("Tray Rim Far",  xl, yf - rim_t, zfr, tray_w, rim_t, ov.PROC_TRAY_RIM, color=draw.C_TRAY, alpha=alpha))
    parts.append(draw.ruby_box("Tray Rim Left", xl, yn, zlr, rim_t, tray_d, ov.PROC_TRAY_RIM, color=draw.C_TRAY, alpha=alpha))
    parts.append(draw.ruby_box("Tray Rim Right", xr - rim_t, yn, zrr, rim_t, tray_d, ov.PROC_TRAY_RIM, color=draw.C_TRAY, alpha=alpha))
    # Translucent chemistry bath inside the rims (at the raised level)
    zb = ov.tray_floor_z((xl + xr) / 2, (yn + yf) / 2)
    parts.append(draw.ruby_box("Chemistry Bath",
                          xl + rim_t, yn + rim_t, zb,
                          tray_w - 2 * rim_t, tray_d - 2 * rim_t,
                          ov.PROC_TRAY_RIM - sheet_t - 8, color=draw.C_BATH, alpha=a_bath))
    return '\n'.join(parts)



# Flat-T red-handle 3-way diverter — shared with the corridor module (DV-01 on the wall,
# DV-02 on the corridor panel) and kept there to avoid a circular import.
C_HANDLE = cp.C_HANDLE
diverter = cp.diverter

# 3W-DV-01 center — single source for the geometry (kit()) AND the label anchor, so the
# callout can never drift off the diverter again when DV-01 is relocated.
DV01_CX, DV01_CY, DV01_CZ = 4775, cp.CTR_Y + 60, 235   # nudged 25mm −X toward the walkway; still +X enough that the port turns run square (DCY drives the filtered-line ribbon notch — don't nudge in Yd without decoupling it)


def kit(part="all", p02_on_corridor=False):
    """Pinhole-wall FILTER SKID (Phase-2 topology).  The tray drain feeds the filters:
    tray sump → P-04 → SV-02 (sample) → DV-02 → F1 → F2 → F3 → SV-01 (sample) → DV-01 →
    IBC-3 recycle / IBC-4 waste.  Separately, P-02 (corridor) recirculates the clean IBC-3
    buffer to the spray bar: IBC-3 → P-02 → ACC-02 → BV-05 → spray.
    Filters mounted HIGH so the walkway stays clear; the tray-drain skid row (P-04·SV-02·DV-02)
    sits under them; SV-01 raised beside F-3; ACC-02 center-bottom.  Plumbing orthogonal.

    Construction-model splits (default "all" = the full skid, byte-identical):
      • "recycle"       — ONLY the blue DV-01→X1 recycle line (corridor run to the IBC panel; Phase 1)
      • "waste"         — ONLY the grey DV-01→IBC-4 merge line (corridor run to the IBC panel; Phase 1)
      • "brown_ribbon"  — ONLY the brown IBC-3→P-02 suction's under-grate RIBBON portion (Phase 3, 3.2)
      • "skid"          — the skid bodies + on-panel plumbing + the short brown RISE to P-02, but NOT
                          the three lines above (they install earlier)."""
    p = []
    fr = ov.BB_OD / 2          # 92
    BB_H, cap_h = ov.BB_H, 78
    f_top = ov.PWP_FILTER_TOP_Z
    f_bot = f_top - BB_H       # 2000 — the high tier
    fcy = ov.PWP_FILTER_YD     # 104 — filter center Yd (sump back near the wall)
    cap_z = f_bot + BB_H - cap_h / 2   # 2301 — filter cap port centerline
    tie = cap_z                # ports are STRAIGHT/horizontal (in-line filter) — no down-elbow
    rp = ov.PUMP_PIPE_OD / 2   # 10.5
    yL, yS = 230, 295          # feed lane / suction+exit lane (clear of the bodies, Yd ≤ 196)
    yW = 35                    # wall plane — pipes/valves mounted on the plywood backing
    waist = ov.PWP_WAIST_Z     # SV-01 + DV-01 reach height
    cdk = "#222228"

    FX = {"F1": ov.PWP_FILTER_X1, "F2": ov.PWP_FILTER_X2, "F3": ov.PWP_FILTER_X3}   # single-source (tbs_constants)
    def f_in(nm):  return (FX[nm] - (fr + 30), fcy, tie)           # IN  port (−X)
    def f_out(nm): return (FX[nm] + (fr + 30), fcy, tie)           # OUT port (+X)

    # ── 3 Big Blue filters — F1 50µm / F2 KDF-55 / F3 GAC; STRAIGHT in-line ±X ports ──
    for nm, fx in FX.items():
        p.append(draw.ruby_cylinder(f"Filter {nm} sump", fx, fcy, f_bot, fr, BB_H - cap_h, color=draw.C_FILTER))
        p.append(draw.ruby_cylinder(f"Filter {nm} cap", fx, fcy, f_bot + BB_H - cap_h, fr + 3, cap_h, color=cdk))
        for tag, sd in (("in", -1), ("out", +1)):
            if nm == "F3" and tag == "out":
                continue        # F3 OUT stub drawn separately below — it TURNS the collection elbow
            p.append(draw.ruby_pipe_run(f"Filter {nm} {tag} port",
                [(fx + sd * (fr - 6), fcy, cap_z), (fx + sd * (fr + 30), fcy, cap_z)], rp, color=cdk))
        p.append(draw.ruby_cylinder(f"Filter {nm} PR button", fx, fcy, f_bot + BB_H, 6, 9, color=draw.C_STEEL))

    # ── P-02 — UPRIGHT, IN/OUT on OPPOSITE sides along X (same pattern as the filters): OUT (+X)
    #    feeds straight into F1; IN (−X) takes the suction from the shared Brown tap. ──
    p2cx  = ov.PWP_P02_X                                          # body center: OUT tip 40mm before F1
    p2cy  = fcy                                                    # same Yd lane as the filters
    p2cz0 = cap_z - (cp.PVB_H - 18)                               # OUT/IN port height at the cap level
    if not p02_on_corridor:                                      # P-02 relocated to the corridor column (water.skp)
        p += cp.pump_unit("Pump P-02 (Brown)", p2cx, p2cy, p2cz0, axis="x", color=draw.C_PUMP)
    p2_out = cp.pump_out(p2cx, p2cy, p2cz0, "x")                  # OUT port — exits +X (→ F1)
    p2_in  = cp.pump_in(p2cx, p2cy, p2cz0, "x")                   # IN port — exits −X (suction)

    # ── SV-01 sample tap stays on the plywood at the wall (sample cup access at waist).  3W-DV-01 is
    #    RELOCATED into the rear corridor so the filtered line runs as ONE pipe and only splits there ──
    svx = SV01_X               # relocated: centered under DV-02 (X3976)
    svz = SV01_CZ              # raised: valve center = filtered-line in-line height (Z1145)
    sv_y = yW + 75             # SV-01 projects only 75mm forward of the wall (cup access; was yL=230)
    p.append(cp.sample_valve("SV-01 sample valve", svx, sv_y, SV01_ZB, h=70))
    tipd = cp.DVB / 2 + cp.DVL                  # 33 — diverter port-stub tip reach
    DCX, DCY, DCZ = DV01_CX, DV01_CY, DV01_CZ   # DV-01 at the CORRIDOR-ENTRY TURN (just inside the mouth,
    #   reachable from the right walkway), shifted +60mm AWAY from the pinhole wall (+Yd) — the practical
    #   max at the mouth before the front-far frame upright (Yd1266+).  The single filtered line turns in
    #   here and splits; blue + waste legs run back across the corridor (low lane, under the ACC)
    p.append(diverter("3W-DV-01", DCX, DCY, DCZ, run="x", branch="y-", handle="z+", color=draw.C_VALVE))

    # ── PLUMBING ──
    def pipe(nm, wp, col): p.append(draw.ruby_pipe_run(nm, wp, rp, color=col))
    # 1. IBC-3 (Brown) suction → P-02 inlet, drawn FROM the shared bottom tap (cp.BROWN_TAP — a
    #    T also feeding P-05, so IBC-3 has ONE bottom penetration).  Down to the floor, along the
    #    wall base (Yd80, clear of the grey DV-01 waste drop at yW=35), up to P-02's +Yd IN port.
    yB = 80
    tx, ty, tz = cp.BROWN_TAP
    # UNDER-WALKWAY RIBBON (lane 0): IBC-3 tap (corridor) → loop UP over the first cantilever →
    # down into the ribbon channel → −Yd to the near-rim strip → rise up the wall to P-02's IN port.
    # split for the construction model: the under-grate RIBBON portion lays with the other ribbons
    # (Phase 3, step 3.2, before the grate); the short RISE to P-02 stays with the skid (3.5).
    brown_pre = ([(tx - 30, ty, tz), (4720, ty, tz), (4720, ty, cp.RIBBON_Z)]       # tap → −X → to the FLUSH ribbon Z (no dip)
                 + cp.ribbon_run(0, (4720, ov.RWK_RIBBON_NOTCH_YDS[0], cp.RIBBON_Z), (2960, 55, 25), up_yd=cp.RIBBON_YD_DOWN))  # FLUSH entry: straight through the NOTCHED beam (lane-0 Yd); crest at the SHARED line-1 Yd
    brown_rise_wps = [(2960, 55, p2_in[2]), (2960, p2cy, p2_in[2]), p2_in]         # rise to P-02 IN
    brown_full_pipe = draw.ruby_pipe_run("IBC-3 (Brown) tap -> P-02 inlet", brown_pre + brown_rise_wps, rp, color=draw.C_IBC_BROWN)
    if not p02_on_corridor:                                      # this wall suction is replaced by a corridor IBC-3→P-02 run
        p.append(brown_full_pipe)
    brown_ribbon_pipe = draw.ruby_pipe_run("IBC-3 (Brown) tap -> ribbon (under-grate, to P-02)", brown_pre, rp, color=draw.C_IBC_BROWN)
    brown_rise_pipe = draw.ruby_pipe_run("Brown ribbon -> P-02 inlet (rise)", [brown_pre[-1]] + brown_rise_wps, rp, color=draw.C_IBC_BROWN)
    # ^ OFF the tee's −X end; descent OFFSET from the blue trunk (Yd1170 not 1150); −Yd at z25 OVER the
    #   corridor foot-plate, then step DOWN to z10 (2 elbows) to pass UNDER the blue trunk; strip z10 to P-02.
    #   At x2960 the riser is nudged back to Yd43 (off the strip's Yd56) so it clears the Yd69 supply trunk
    #   it would otherwise rise straight through (grey lane Yd24–45 is x≥4269, so x2960 is clear at Yd43).
    if not p02_on_corridor:
        p.append(cp.ball_valve("BV-03 (P-02 suction)", 2960, 43, waist, "z"))   # at SV-01 reach height (moves to the corridor with P-02)
    # 2. (Phase 2) F1 is now fed by DV-02's recycle branch (see skid_plumbing); P-02 OUT → ACC-02 instead.
    # 3. filter-skid jumpers F1→F2→F3 — straight pipe between the adjacent in-line ports
    #    (combo unit; the ports face each other in the gap, so no around-the-body routing)
    for a, b in (("F1", "F2"), ("F2", "F3")):
        pipe(f"{a} out -> {b} in", [f_out(a), f_in(b)], draw.C_IBC_BROWN)
    # 4. F3 outlet → SV-01: the BLACK OUT-port extension turns the 90° "collection" elbow itself
    #    (elbow rendered INSIDE the black fitting, at the extension's end), then the filter-colored
    #    line picks up at the handoff and drops DOWN the wall (yW) to waist → SV-01.
    #    Why draw the elbow in the black run: ruby_pipe_run insets its fillet along the INCOMING leg,
    #    so an elbow at f_out always eats ~one radius back into whatever precedes it — keeping that
    #    leg the same black fitting means nothing colored is intruded and the elbow sits at the
    #    black extension's end (endpoints get no fitting, so f_out must be an interior vertex).
    f3_hand = (f_out("F3")[0], fcy - 40, tie)          # handoff just past the black elbow's -Y exit tangent
    p.append(draw.ruby_pipe_run("Filter F3 out port",
             [(FX["F3"] + (fr - 6), fcy, tie), f_out("F3"), f3_hand], rp, color=cdk))
    # F3 -> SV-01: drop down the wall, then dog-leg IN through SV-01's −X face — the filtered line runs
    # HORIZONTALLY through the valve body (in-line, matching SV-02), box over the through-segment.
    pipe("F3 -> SV-01 (wall-mounted drop)",
         [f3_hand, (f_out("F3")[0], yW, tie), (svx - 60, yW, tie),          # −Yd to the wall, +X to just −X of SV-01
          (svx - 60, yW, svz),                                       # DOWN the wall to the SV-01 in-line height
          (svx - 60, sv_y, svz),                                     # +Yd forward to the valve lane
          (svx + 25, sv_y, svz)], draw.C_FILTER)                       # +X THROUGH the body (in-line) to the +X face
    # after SV-01 the run returns to the plywood (yW) BEFORE routing on to DV-01 — keeps the
    # narrow walkway clear (only SV-01's sample spout projects forward to yL)
    # 4b. SV-01 -> DV-01: ONE filtered line follows the shared surface-perimeter route across the
    #     corridor (the path the blue+waste legs used to BOTH take, stacked) to the relocated DV-01 —
    #     which now SPLITS in the rear corridor, collapsing the old pair of parallel runs into one.
    sz    = cp.SUCT_SURF_Z + 30                   # 235 — surface perimeter lane
    xdrop = ov.RAIL_X_R - 17                      # 4632 — turn DOWN the wall clear of the IBC hanger
    # UNDER-WALKWAY RIBBON (lane 3): SV-01 → down the wall → −Yd along the ribbon → grate slot
    # → across the corridor to DV-01's IN port.
    # Drop SV-01 straight down the wall to a LOW strip level and run under the walkway beams (like the
    # other three lines).  On the corridor side it comes back DOWN just past the cantilever (like the
    # sump), runs under the grate to DV-01's Yd, then rises into DV-01's IN port.
    # At the pinhole-wall end the filtered line mirrors the grey (DV-02→IBC-4): from SV-01 it hops +X at
    # Z1010 OVER the inner beam to its own lane X, then DROPS straight down into the ribbon lane — turning
    # north (90° at the bottom) with NO under-walkway crossing.  Ribbon + DV-01 corridor end are unchanged.
    blane = cp.RIBBON_LANE_X[3]
    pipe("SV-01 -> DV-01 (single filtered line)",
         [(svx + 25, sv_y, svz),                                               # leave SV-01's +X face (in-line)
          (svx + 50, sv_y, svz),                                               # +X out (dog-leg)
          (blane, sv_y, svz),                                                  # +X at Z1010 OVER the inner beam to the lane X (over the walkway, not under)
          (blane, 60, svz)]                                                     # −Yd to the ribbon near-rim Yd (still Z1010) — top of the drop
         + cp.ribbon_run(3, (DCX - 100, DCY, cp.RIBBON_Z), (blane, 60, svz), up_yd=cp.RIBBON_YD_DOWN)[::-1][1:]  # FLUSH entry on the corridor end (no dip) + under-walkway ribbon (lane 3)
         + [(DCX - 100, DCY, DCZ),                                                      # rise −X of the port to the IN-port height
            (DCX - tipd, DCY, DCZ)],                                                    # +X 90° turn horizontally into DV-01's −X IN port
         draw.C_FILTER)
    # 5. DV-01 RECYCLE (run+, +X) → IBC-3 BUFFER tote — the recycle loop's buffer; P-02 pulls from IBC-3.
    #    (Was routed to the Blue X1 fill cross; Blue is now FILL-ONLY fresh water, so the filtered recycle
    #    stays isolated in IBC-3 — the contamination fix.)  CV-3 anti-siphon check on the approach.
    r_ex = 4760                                          # entry X on the Brown-tote near face, just −X of DV-01 (clear of the tap 4880 + pump column 4934)
    r_ez = ov.IBC_H_1000 - 38                            # 1130 — Brown top-entry level (= the old DV-02→IBC-3 entry)
    _rec0 = len(p)                                        # capture the recycle-leg elements _side_entry is about to append (part='recycle')
    entry_z = r_ez - 50                                  # 1080 — IBC-3 tote entry 50mm below the top-entry level (clear of the top edge ~1148)
    entry_face = cp.YD_NEAR - 8                           # 1038 — pass face −8 so _side_entry's (yface−into·8) seats the 16mm flange BASE on the cage edge (Yd1046)
    cp._side_entry(p, "DV-01 recycle -> IBC-3 (buffer)",
        [(DCX + tipd, DCY, DCZ),                         # off DV-01's +X recycle port (z235)
         (DCX + tipd + 40, DCY, DCZ),                    # +X OUT of the port — 90° #1 into DV-01
         (DCX + tipd + 40, cp.SB_RISER_YD_FAR, DCZ),     # +Yd onto the FAR support-board riser plane (#29) — 90° #2 into DV-01
         (DCX + tipd + 40, cp.SB_RISER_YD_FAR, entry_z), # RISE up the board face straight to the ENTRY level (lowered — no drop jog)
         (r_ex, cp.SB_RISER_YD_FAR, entry_z)],           # −X along the far board; _side_entry then runs −Yd STRAIGHT into the flange (at X4760, −X of the pumps → clear)
        r_ex, entry_face, entry_z, -1, draw.C_BLUE, drop=-50, check=False)   # −Yd into the Brown tote; flange seats on the cage edge (Yd1046) at Z1080
    recycle_elems = list(p[_rec0:])                      # the DV-01 recycle→IBC-3 pieces, captured by identity (material names leak across pipes — don't match by substring)
    # 6. DV-01 WASTE (branch, z+) → the shared IBC-4 merge tee's z− branch (DV-02's waste also lands here,
    #    on the tee run, so the two legs make ONE tote entry).
    mx, my, mz = cp.MERGE4
    waste_pipe = draw.ruby_pipe_run("DV-01 -> IBC-4 merge",
         [(DCX, DCY - tipd, DCZ), (DCX, 1165, DCZ),                   # SHORT −Yd exit off the branch → 90° elbow sooner
          (mx, 1165, DCZ),                                            # +X across the corridor at Yd1165 — SHIFTED +Yd (toward the
          #   film plane, was 1147) to open a lane for the blue supply trunk; still clears the brown P-02 riser below and
          #   the blue recycle elbow above (−Yd edge 1185)
          (mx, my, DCZ),                                              # −Yd to the merge column at the far end
          (mx, my, mz)], rp, color=draw.C_IBC_WASTE)                    # rise into the merge tee's z− branch
    p.append(waste_pipe)
    if part == "all":
        return "\n".join(p)
    # Part slices for the construction build-sequence, matched by ELEMENT IDENTITY (a pipe's material
    # name is shared/leaked across every same-color pipe, so substring matching over-selects — see
    # recycle_elems capture above).  recycle+waste+brown_ribbon+skid == all in BOTH P-02 modes:
    #   • P-02 on wall  (Phase-1): brown_full is in `p`; split into brown_ribbon (→3.2) + brown_rise (→skid).
    #   • P-02 on corridor (Phase-2): no wall suction — brown_ribbon is empty, recycle+waste+skid == all.
    if part == "recycle":
        return "\n".join(recycle_elems)
    if part == "waste":
        return waste_pipe
    if part == "brown_ribbon":
        return "" if p02_on_corridor else brown_ribbon_pipe
    if part == "skid":
        drop = set(recycle_elems) | {waste_pipe} | (set() if p02_on_corridor else {brown_full_pipe})
        keep = [x for x in p if x not in drop]
        return "\n".join(keep + ([] if p02_on_corridor else [brown_rise_pipe]))
    return "\n".join(p)


def tap01_supply():
    """Blue supply trunk along the pinhole wall → spray-bar tap (BV-05) + TAP-01 chem tap (BV-04).
    Based on overview.skp's spray_bar_plumbing, but the wall trunk runs at the TRAY-RIM edge (Yd69,
    butted to the near rim) so it tucks UNDER the triangular near-walkway cantilever brackets — the
    Yd12-against-the-wall path ran straight through the bracket plates/bolts.  BV-04/BV-05 off-panel."""
    yd, fz = ov.PROC_TRAY_YD_NEAR - 11, ov.SPRAY_BAR_FEED_Z   # 69 — butt the tray near rim (Yd80), under the triangle
    pr, tr = ov.PUMP_PIPE_OD / 2, ov.TAP_PIPE_OD / 2
    bvx = ov.BV05_X - 150   # BV-05 riser nudged 150mm −X (toward the EP) to clear the relocated tray-sump suction at PH_X
    p = []
    # UNDER-WALKWAY RIBBON (lane 1): the corridor blue trunk (dropped clear of the FP rail at X4670, Yd~1132,
    # z60) rises to FLUSH in the tray-edge slot, crosses the notched outer beam, runs −Yd along the ribbon to
    # the outside-rim strip, where the wall trunk continues.  (Moved from lane 2 → lane 1: the middle two lanes
    # swapped so the blue TAP-01 trunk and the brown tray-sump alternate, and the blue/brown no longer cross.)
    p.append(draw.ruby_pipe_run("Blue trunk: corridor -> ribbon -> outside-rim strip",
        cp.ribbon_run(1, (cp.BLUE_TRUNK_HANDOFF_X, cp.GAP_CORR_Y, cp.RIBBON_Z), (cp.BLUE_TRUNK_LANE_X, yd, fz), up_yd=cp.RIBBON_YD_DOWN, lane_x=cp.BLUE_TRUNK_LANE_X), pr, color=draw.C_BLUE))  # FLUSH entry; nudged +X toward the brown lane (lane_x) — STRAIGHT back (no U)
    p.append(draw.ruby_cylinder("Blue Supply Trunk (1/2in HDPE)",   # trunk ends at the ribbon lane (clear of the saddle gusset)
        ov.TAP_X, yd, fz, pr, cp.BLUE_TRUNK_LANE_X - ov.TAP_X, color=draw.C_BLUE, axis="x"))
    # BV-05 3W SELECTOR (fresh ↔ recycled → spray bar) — relocated FORWARD (Yd) + UP (Z) onto a bracket off
    # the pinhole wall, close to the spray-bar pole-top feed (2420,633,1303) so the delivery coil is short.
    #   run = fresh (−Yd, up from the trunk) ↔ spray (+Yd, to the coil); branch = recycled IN (+X, from ACC-02).
    b5x, b5y, b5z = bvx, yd, 700                       # ON the pinhole wall (Yd69); DROPPED so it + its routing clear the pinhole assembly (Z1024-1364, aperture Z1194)
    dvt = cp.DVB / 2 + cp.DVL                          # diverter port-tip reach
    p.append(cp.diverter("3W-BV-05a (Blue/Brown selector)", b5x, b5y, b5z, run="z", branch="x+", handle="y+", color=draw.C_VALVE))
    # Fresh supply: tap the trunk, rise straight into the −Z fresh port
    p.append(draw.ruby_pipe_run("BV-05 fresh supply (trunk -> selector)",
        [(b5x, b5y, fz),                              # tap the blue trunk (Yd69, Z41)
         (b5x, b5y, b5z - dvt)], pr, color=draw.C_BLUE))  # UP into the −Z fresh port
    # Spray delivery: BV-05a +Z selected port → BV-05b (2-way ON/OFF, WALL-MOUNTED just above the
    # selector — a fixed mount, not on the moving spray-bar pole) → coiled hose forward to the beam.
    p.append(draw.ruby_pipe_run("BV-05a -> BV-05b (up the pinhole wall)",
        [(b5x, b5y, b5z + dvt),                        # off the BV-05a +Z selected port
         (b5x, b5y, 1000)], pr, color=draw.C_BLUE))      # UP the pinhole wall to BV-05b (stays below the pinhole Z1024)
    p.append(cp.ball_valve("BV-05b (spray on/off)", b5x, b5y, 900, "z", hdir="+y"))   # 2-way ON/OFF — WALL-mounted, reach height
    p.append(draw.ruby_coil_cord("Spray-bar supply hose (BV-05b -> spray bar, coiled)",
        [(b5x, b5y, 1000),                             # off the top of BV-05b
         (2380, 480, 720),                             # FORWARD-low to the pole area (below the pinhole Z1024)
         (2410, 660, 440),                             # LONG service loop — droop down for slack (forward of the pinhole)
         (2420, 633, 1303)], r=7, color=draw.C_BLUE))    # UP alongside the pole to the pole-top feed
    # TAP-01 chem branch (3/4in) up over the shelf + BV-04 isolation (overview path)
    p.append(draw.ruby_pipe_run("TAP-01 Branch (3/4in)",
        [(ov.TAP_X, yd, fz), (ov.TAP_X, yd, ov.SHELF_STOW_TOP_Z),
         (ov.TAP_X, yd + 100, ov.SHELF_STOW_TOP_Z), (ov.TAP_X, yd + 100, ov.TAP_Z)], tr, color=draw.C_BLUE))
    p.append(cp.ball_valve("BV-04 (chem tap isolation)", ov.TAP_X, yd, 1010, "z"))
    # WALL-STANDOFF P-clips — the blue supply trunk + the TAP-01/BV-05 risers run below the ply panel
    # (Z<920) along the BARE pinhole wall at Yd69; they clamp to the wall (Yd0) on ~55mm standoff blocks.
    wreach = yd + pr + 2                                      # Yd0 → just past the pipe (wall standoff)
    for tx in (1500, 2100, 2700, 3300, 3900, 4400):          # Blue Supply Trunk (horizontal, Z=fz): band ⊥ the pipe, ~600mm
        p.append(draw.ruby_box("Wall-standoff pipe P-clip", tx - 8, 0, int(fz) - 14, 16, wreach, 28, color=cp.C_CLIP))
    for tz in (250, 550, 850, 1150):                         # TAP-01 riser (vertical, X=TAP_X): thin-Z band, ~300mm
        p.append(draw.ruby_box("Wall-standoff riser P-clip", ov.TAP_X - 14, 0, tz - 8, 28, yd + tr + 2, 16, color=cp.C_CLIP))
    for bz in (250, 500, 850):                               # BV-05 fresh-supply riser (vertical, X=bvx)
        p.append(draw.ruby_box("Wall-standoff riser P-clip", bvx - 14, 0, bz - 8, 28, wreach, 16, color=cp.C_CLIP))
    return "\n".join(p)


def backing():
    """18mm exterior-grade ply (BC/ACX) backing for the whole wall sub-loop — secured to the
    container wall; the pump, filters and valves mount on it and the pipes clamp to it for support
    (so the sub-loop installs as one panel, mirroring the corridor rear panel).  Dry mounting
    backboard — exterior grade, NOT marine (no water-immersion load)."""
    return draw.ruby_box("Wall backing (18mm ply)", 2780, 0, 920, 1795, ov.EQPANEL_T, 1440, color=draw.C_PLY)  # +75mm at the +X edge so the grey waste clamps to the ply before it bends into the ribbon


def person():
    # 1.75m scale figure standing ON the near walkway, FACING the IBC totes (+X):
    # depth (front-back) along X, shoulders along Yd.
    px, py = 3050, 200          # on the near walkway deck — nudged out so the back clears the ply
    z = DECK_Z
    pp = []
    pp.append(draw.ruby_box("Person legs", px - 100, py - 80, z, 200, 160, 850, color=C_PERSON, alpha=0.28))
    pp.append(draw.ruby_box("Person torso", px - 90, py - 150, z + 850, 180, 300, 600, color=C_PERSON, alpha=0.28))
    pp.append(draw.ruby_cylinder("Person head (scale 1.75m)", px, py, z + 1450, 100, 230, color=C_PERSON, alpha=0.32))
    return "\n".join(pp)


def right_walkway():
    """Partial view of the RIGHT walkway (runs in Yd across the container at X≈4329-4629)
    — only the slice within the limited depth (Yd0..VIEW_DEPTH), for spatial context where
    it passes the wet-end's IBC end."""
    return draw.ruby_box("Right walkway (partial)", ov.WALKWAY_RIGHT_X, 0, DECK_Z - 15,
                       ov.WALKWAY_RIGHT_W, VIEW_DEPTH, 15, color=draw.C_WALKWAY, alpha=0.9)


# ── "Labeled" scene callouts (point-anchored on the kit; instance-anchored on pinhole/elec) ──
_FILT_FCY = ov.BB_OD / 2 + 12              # 104 — filter / P-02 body center Yd (sump back near the wall)
_FILT_CZ  = ov.C_HGT - 48 - ov.BB_H / 2    # 2170 — Big-Blue filter body center Z
# Phase-2 skid row (P-04 · SV-02 · DV-02, under the filters) — single-sourced for skid_row/plumbing/labels
SROW_YD, SROW_Z0 = 104, ov.PWP_SROW_Z0   # Yd104 = the filter/P-02 wall lane (surface-mounted on the ply, like the other kit)
SKID_CLIP_YD = 35                          # #29: skid-panel riser plane — vertical runs sit flush on the ply (face Yd18) and P-clip to it (= the F3→SV-01 wall-lane Yd)
# ── Panel reorg (2026-08-04): declutter the skid so the lane-1 brown rises up the wall and runs the panel
#    bottom to ACC-02 (like lanes 3 & 4).  Component X/Z decoupled from the shared filter/pump constants. ──
PANEL_X0, PANEL_X1, PANEL_Z0 = ov.PWP_PANEL_X0, ov.PWP_PANEL_X1, ov.PWP_PANEL_Z0   # 18mm-ply extents (single-sourced)
ACC2_X  = ov.PWP_ACC2_X                          # 3857 — panel center + 180 toward the IBCs (clears SV-02)
ACC2_Z0 = ov.PWP_ACC2_Z0                         # ACC-02 base on the panel bottom (Z920)
SV01_X  = ov.PWP_SV01_X                            # 4250 — SV-01: 300mm left toward F-3, then 300mm back toward the IBC totes
SV01_CZ = ov.PWP_SV01_Z                            # 1610 — valve center = filtered-line in-line height (single-sourced)
SV01_ZB = SV01_CZ - 35                            # 1575 — sample-valve base (valve center − h/2)
LABEL_POINTS = [  # (x, y, z, text, leader dx,dy,dz) — (x,y,z) is the arrow TIP = component CENTER
    # ── pinhole-wall FILTER sub-loop (leaders point +Yd, out toward the operator) ──
    (ACC2_X, ov.PWP_FILTER_YD, ACC2_Z0 + 87, "ACC-02\n(recycle spray)", 0, 470, 330),   # relocated to panel center-bottom
    (3300, _FILT_FCY, _FILT_CZ, "F1 (50um)",   0, 560, 215),
    (3638, _FILT_FCY, _FILT_CZ, "F2 (KDF-55)", 0, 560, 215),
    (3976, _FILT_FCY, _FILT_CZ, "F3 (GAC)",    0, 560, 215),
    (SV01_X, 110, SV01_CZ, "SV-01\n(sample)", -430, 430, 250),   # relocated under DV-02, raised
    (DV01_CX, DV01_CY, DV01_CZ, "DV-01\n(3-way)",  -700, 0, 650),   # relocated to the corridor mouth (see kit())
    # ── Phase-2 skid row under the filters (P-04 · SV-02 · DV-02, relocated from the corridor) — leaders +Yd ──
    (ov.PWP_FILTER_X1, SROW_YD, SROW_Z0 + cp.PVB_H / 2, "P-04\n(tray drain)", 0, 470, -180),
    (ov.PWP_FILTER_X2, SROW_YD, SROW_Z0 + 162, "SV-02\n(sample)", 0, 470, -120),
    (ov.PWP_FILTER_X3, SROW_YD, SROW_Z0 + 162, "DV-02 (3-way)", 0, 470, -180),
    # ── corridor plumbing panel: single-column pumps + ACCs (leaders point −X, out the mouth) ──
    (cp.PXC, cp.CTR_Y, cp.PSTACK["P-01"] + cp.PVB_H / 2, "P-01 (Blue supply)", -700, 0, -150),
    (cp.PXC, cp.CTR_Y, cp.PSTACK["P-04"] + cp.PVB_H / 2, "P-02 (recycle pump)", -800, 0, -150),   # relocated into P-04's vacated slot
    (cp.PXC, cp.CTR_Y, cp.PSTACK["P-05"] + cp.PVB_H / 2, "P-05 (Brown drain)", -900, 0,  150),
    (cp.PXC, cp.CTR_Y, cp.PSTACK["P-03"] + cp.PVB_H / 2, "P-03 (Waste drain)", -1000, 0, 150),
    (cp.PXC, cp.CTR_Y, cp.ACC_Z0 + 87, "ACC-01\n(accumulator)", -700, 0, 250),   # + acc_h/2 (body 174)
    (cp.BACK_X + cp.EQT + 24, cp.CTR_Y, (cp.PSTACK["P-01"] + cp.PSTACK["P-03"]) / 2 + 90, "12V DIST BLOCK\n(Cct C)", 300, 0, 400),   # rear-of-panel Circuit-C distribution block (behind the pump column; feed lands here, bus fans out to the pumps)
    # ── ball valves (in-panel pump-suction isolation; BV-01/02 on the BACK-of-panel risers) ──
    (cp.FRONT_X + 221, cp.SB_RISER_YD_NEAR, 950, "BV-01", -600, 0, 250),   # on the near-board P-01 suction riser (dropped 50mm; pushed onto the board face)
    (cp.BV_FWD_X, cp.BV02_YD, cp._piz("P-05") - 85, "BV-02", -350, 0, 200),   # tip = BV-02 valve center (walkway-edge loop); text on the −X operator side
    (cp.BROWN_TAP[0] - 55, cp.SB_RISER_YD_NEAR, 900, "BV-03", -600, 0, 250),   # ON the corridor P-02 suction riser (on the near support board; dropped 50mm)
    (cp.BV_FWD_X, cp.BV02_YD, cp._piz("P-03") - 110, "BV-06", -350, 0, 150),    # tip = BV-06 valve center (walkway-edge loop); text on the −X operator side
    # ── per-tank anti-siphon check valves ──
    (ov.C_LEN - 200, cp.X1_TEE_Y, cp.X1_TEE_Z, "CV-1\n(X1 fill)", -600, 300, 0),   # only CV-1 — pumps' integral checks cover the returns
    # ── end-wall bulkhead ports (tip at the port-body center, 30mm in from the wall) ──
    (ov.C_LEN - 30, cp.X1_TEE_Y, cp.X1_TEE_Z, "X1\n(fresh fill)", -550, 250, 0),
    (ov.C_LEN - 30, cp.COL_L, 1700, "X3\n(brown drain out)", -550, 0, 250),
    (ov.C_LEN - 30, cp.COL_R, 1620, "X4\n(waste drain out)", -550, 0, -250),
    (ov.BV05_X - 150, ov.PROC_TRAY_YD_NEAR - 11, 700, "3W-BV-05a\n(Blue/Brown selector)", 0, 380, 250),   # the wall-mounted spray-bar source selector
    (ov.BV05_X - 150, ov.PROC_TRAY_YD_NEAR - 11, 900, "BV-05b\n(spray on/off)", 0, 300, 200),   # the 2-way on/off, WALL-mounted above the selector
]
# Off-panel / context labels — shown ONLY in the full "Labeled" scene (Labels Context tag), kept
# OUT of the "Plumbing (labeled)" scene so their leaders don't clutter the plumbing view.
LABEL_CONTEXT_POINTS = [
    (ov.TAP_X, 112, ov.TAP_Z, "TAP-01\n(chem tap)", 0, 450, 300),
    (ov.TAP_X, 12, 1010, "BV-04", -450, 0, 250),
]
LABEL_INSTANCES = [
    ("Pinhole Assembly", "PINHOLE\n(optical ref)", 0, 700, 350),
    ("Other pinhole-wall equipment", "ELECTRICAL\n(panel/inverter/batteries)", 0, 850, 500),
    ("IBC Tanks (full)", "IBCs\n(space NOT available)", -300, 900, 300),
]


def labels_ruby():
    rows = []
    for x, y, z, text, dx, dy, dz in LABEL_POINTS:
        rows.append(
            f'anc = Geom::Point3d.new({draw.mm(x)},{draw.mm(y)},{draw.mm(z)})\n'
            f'txt = entities.add_text("{text}", anc, Geom::Vector3d.new({draw.mm(dx)},{draw.mm(dy)},{draw.mm(dz)}))\n'
            f'txt.layer = model.layers["Labels"] rescue nil')
    for x, y, z, text, dx, dy, dz in LABEL_CONTEXT_POINTS:   # off-panel labels → Labels Context tag
        rows.append(
            f'anc = Geom::Point3d.new({draw.mm(x)},{draw.mm(y)},{draw.mm(z)})\n'
            f'txt = entities.add_text("{text}", anc, Geom::Vector3d.new({draw.mm(dx)},{draw.mm(dy)},{draw.mm(dz)}))\n'
            f'txt.layer = model.layers["Labels Context"] rescue nil')
    for name, text, dx, dy, dz in LABEL_INSTANCES:
        rows.append(
            f'inst = entities.grep(Sketchup::ComponentInstance).find {{ |i| i.name == "{name}" }}\n'
            f'if inst\n'
            f'  bb = inst.bounds\n'
            f'  anc = Geom::Point3d.new(bb.center.x, bb.min.y, bb.center.z)\n'
            f'  txt = entities.add_text("{text}", anc, Geom::Vector3d.new({draw.mm(dx)},{draw.mm(dy)},{draw.mm(dz)}))\n'
            f'  txt.layer = model.layers["Labels Context"] rescue nil\n'   # context labels (PINHOLE/ELEC/IBC) — full scene only
            f'end')
    return '\n'.join(rows)


def panel_power(include_switch=True, part="all"):
    """Circuit-C power + cabling to the TWO plumbing panels ONLY (no other electrical shown).
    Routed to NEVER cross a pipe (plumbing-skill rule): the corridor run lives in the CHASE
    between the pump-mount shirt and the rear panel — a clear vertical channel behind the pump
    bodies. Ceiling feed → master switch + 12V distribution block in the chase → vertical bus
    down the chase → short back-taps to each pump (behind the body). One branch runs along the
    ceiling (in the tote-free corridor lane) to the Pinhole-Wall panel → P-02.

    part="corridor" = everything EXCEPT the final EP drop (the dist block, bus, pump taps, P-02
    branch + the ceiling feed run STOPPING at the pinhole-wall trunk above the EP) — the
    construction model installs this in Phase 1, wired to the pinhole wall. part="ep_link" = just
    the EP-drop segment (+ master switch), connected in Phase 4. "all" (default) = the original
    single feed run + everything, byte-identical."""
    do_corr = part in ("all", "corridor")
    do_link = part in ("all", "ep_link")
    PWR = "#2980B9"                                 # Cct-C color (blue) — matches fuse C (was purple = same as Cct-D, confusing)
    cr = 4                                          # thin 16 AWG conductor (was 7 — too fat; crowded the fuse-D feed + battery − riser)
    p = []
    TY, TZ = 20, ov.C_HGT - 13                       # pinhole-wall ceiling trunking line (Yd20), per electrical.skp
    ptop = cp.PSTACK['P-03'] + cp.PVB_H              # 1920 — top of the pump column
    BKX = cp.BACK_X + cp.EQT + 24                    # ~5146 — dist block + bus on the REVERSE of the panel (clear)
    by  = cp.CTR_Y                                    # 1181 — corridor center (tote-free, between back uprights)
    fr = ov.BB_OD / 2
    pwr_edge_x = ov.PWP_PANEL_X0 + 20                # pinhole-side plywood edge — P-04's Cct-C drops here, clear of the filters (X3161+); then runs across to the pump
    p04_body_x = ov.PWP_FILTER_X1 + 30               # P-04 body-center X on the filter skid (tray-drain pump relocated here from the corridor)
    epx = 1979                                       # EP fuse-block C X (electrical.skp)
    swx = epx + 200                                  # 2179 — master switch 200mm toward the IBC end (clear of the EP kit)
    z_lo = cp.PSTACK['P-01'] + 90                     # 705  — lowest pump tap
    z_hi = cp.PSTACK['P-03'] + 90                     # 1830 — highest pump tap
    zc   = (z_lo + z_hi) / 2                          # 1268 — vertical center of the pump column
    # ── MASTER SWITCH on the ELECTRICAL PANEL — one cutoff upstream of EVERYTHING (avoids a
    #    corridor switch + its through-panel wiring; puts BOTH P-02 and the corridor pumps
    #    downstream of it).  Red disconnect lever like the DV handles. ──
    if include_switch:   # standalone: draw the REAL EP master switch (owned by em) + feed off it
        import generate_electrical_model as em
        if do_link:
            p.append(em.master_switch())
        fx, fy, fz = em.MASTER_SW_POS
    else:                # EP present (overview + water): feed off the EP panel's OWN master switch, ON the panel
        import generate_electrical_model as em
        fx, fy, fz = em.MASTER_SW_POS
    # ── feed: EP master switch → Yd20 ceiling trunk (per electrical.skp, clear of the center
    #    LEDs) → down to the corridor 12V DISTRIBUTION BLOCK.  Split at index 2 = (fx,TY,TZ), the
    #    pinhole-wall ceiling trunk above the EP: corridor side (Phase 1) vs EP drop (Phase 4). ──
    # The dist block sits BEHIND the rear panel, in the Yd-gap between the two rear frame uprights
    # (Yd1096.8-1265.2) — and the frame's TOP ring Yd-rail bridges exactly that gap (Z2245-2296).  A
    # straight drop onto the block would pierce that rail, and a Yd-traverse at the block's X (inside the
    # upright footprint 5104-5154.8) would pierce an upright.  So drop in the CORRIDOR just −X of the rear
    # frame, pass UNDER the top rail at the block Yd (in the clear upright gap), then step +X into the pocket.
    cx_clear = cp.BACK_X - 24                         # 5080 — drop lane −X of the rear uprights (5104+), in the corridor
    urz      = cp.TOP_Z - ov.IBC_FRAME_RHS - 60       # 2185 — under the top ring rail (bottom 2245), above the panel/pumps
    _rx = fx - 19                                                                           # riser X, clear LEFT of the battery − cable (X1958-1980) AND clear of the Cct-D feed at fuse D (X1926)
    feed = [(fx, fy, fz), (_rx, fy, fz), (_rx, 65, fz), (_rx, 65, TZ), (_rx, TY, TZ), (pwr_edge_x, TY, TZ),   # exit the switch REAR, jog −X clear of the battery − riser (at Yd100), tuck to Yd65 (front of fuses/busbar, behind the MPPT cross member), rise
            (cx_clear, TY, TZ), (cx_clear, by, TZ), (cx_clear, by, urz),   # ceiling to the clear drop lane, +Yd to the block Yd, DROP to under the rail
            (BKX, by, urz), (BKX, by, zc + 48)]                            # +X under the rail into the pocket, then down onto the block
    if part == "all":
        p.append(draw.ruby_pipe_run("Cct C feed (EP master sw -> corridor dist block)", feed, cr, color=PWR))
    else:
        if do_link:
            p.append(draw.ruby_pipe_run("Cct C feed (EP master sw -> pinhole-wall ceiling)", feed[:5], cr, color=PWR))
        if do_corr:
            p.append(draw.ruby_pipe_run("Cct C feed (pinhole-wall ceiling -> corridor dist block)", feed[4:], cr, color=PWR))
    if part == "all" or do_corr:
        # P-clip supports on the corridor-exposed part of the feed (the Yd-traverse + the drop onto the
        # dist block, out past the ceiling trunk) — mirrors the plumbing pipe-support-clips.
        p.append(draw.ruby_clip_run("Cct C feed", feed[6:], spacing=450))
    # ── P-04 (tray-drain pump, relocated to the filter skid) taps the trunk off the master-switch
    #    feed → drops down the pinhole wall (Yd20, behind the skid) → into P-04's body from the wall
    #    side.  (P-02 is now a corridor-column pump — wired off the corridor bus below.) ──
    p4z  = SROW_Z0 + cp.PVB_R                         # P-04 body-center Z on the skid
    p4ty = SROW_YD - 14                               # just behind the surface-mounted P-04 body (wall side; clears the Yd104 skid plumbing in front)
    if do_corr:
        # Route AROUND the filters: -X to the pinhole-side plywood edge, DROP the edge at the Yd20 wall
        # lane (clear of F-1/F-2/F-3 at X3161+), run +X below the filter sumps to under P-04, then tap
        # +Yd into P-04's body.  Never passes through a filter or the Yd104 skid-plumbing plane.
        _p04br = [(pwr_edge_x, TY, TZ), (pwr_edge_x, TY, p4z),
                  (p04_body_x, TY, p4z), (p04_body_x, p4ty, p4z)]
        p.append(draw.ruby_pipe_run("Cct C branch P-04 (filter skid)", _p04br, cr, color=PWR))
        p.append(draw.ruby_clip_run("Cct C branch P-04", _p04br, spacing=400))
        # ── 12V DISTRIBUTION BLOCK on the REVERSE of the corridor panel + bus + back-taps to pumps ──
        p.append(draw.ruby_box("12V distribution block (Cct C, rear)", BKX - 24, by - 30, zc - 45, 48, 60, 90, color="#3A3A42"))
        # power bus down the back, with SMOOTH elbows turning into the TOP (P-03) and BOTTOM (P-01)
        # pumps as one continuous run; the two middle pumps tee off the bus.
        xin = cp.PXC + cp.PVB_R - 10                      # 5024 — tap tip, 10mm into each pump back
        bus_pts = [(xin, by, z_hi), (BKX, by, z_hi), (BKX, by, z_lo), (xin, by, z_lo)]
        p.append(draw.ruby_pipe_run("Cct C bus + P-03/P-01 elbow taps (rear)", bus_pts, cr, color=PWR))
        # P-clips carrying the pump-feed bus down the rear of the corridor plumbing panel.
        p.append(draw.ruby_clip_run("Cct C pump bus", bus_pts, spacing=380))
        # corridor branch taps: P-05 + the pump now in P-04's vacated slot (P-02, Phase 2)
        for label, key in (("P-02", "P-04"), ("P-05", "P-05")):
            z = cp.PSTACK[key] + 90
            _br = [(BKX, by, z), (xin, by, z)]
            p.append(draw.ruby_pipe_run(f"Cct C branch {label}", _br, cr, color=PWR))
            p.append(draw.ruby_clip_run(f"Cct C branch {label}", _br, spacing=100))
    return "\n".join(p)


# ── Phase 2: relocated tray-sump processing ROW, mounted on the FILTER SKID under the filters ──
# P-04 (sump pump) · SV-02 (sample tap) · 3W-DV-02 diverter, in a row under F1 / F2 / F3.
# Facing the pinhole wall, right→left = P-04 (low X, beside F1) → SV-02 → DV-02 (high X).
# The sump pickup feeds P-04 directly here.  SROW_YD/SROW_Z0 single-sourced above (near LABEL_POINTS).
def skid_row():
    """The relocated tray-sump processing row on the filter skid (P-04 · SV-02 · 3W-DV-02).
    Bodies only for now — plumbing (sump→P-04→SV-02→DV-02→F1 / waste) follows in Increment 2."""
    p = []
    p += cp.pump_unit("Pump P-04 (Tray drain)", ov.PWP_FILTER_X1, SROW_YD, SROW_Z0, axis="x", face=+1)
    # #29 — P-04 DISCHARGE braided ½" flex jumper (+X toward SV-02); its SUCTION is the 1" tray-drain
    #   hose (already a flexible connection), so only the discharge port needs a jumper here.
    _p4o = cp.pump_out(ov.PWP_FILTER_X1, SROW_YD, SROW_Z0, axis="x", face=+1)
    cp._flex_jumper(p, "P-04 discharge jumper", _p4o, (_p4o[0] + 40, _p4o[1], _p4o[2]), draw.C_IBC_BROWN, start=2, maxlen=24)
    p.append(cp.sample_valve("SV-02 sample valve", ov.PWP_FILTER_X2, SROW_YD, SROW_Z0 + 132, h=60))   # IN-LINE: row line runs THROUGH the body (center Z1312 = P-04 OUT), red handwheel free above, spout below
    p.append(cp.diverter("3W-DV-02", ov.PWP_FILTER_X3, SROW_YD, SROW_Z0 + 162,
                         run="x", branch="z+", handle="y+", color=draw.C_VALVE))   # IN −X (P-04) · waste +X (corridor) · feed z+ (F1); center Z1312 = P-04 OUT (straight run)
    # ACC-02 (recycled-spray accumulator) — on the filter skid, in P-02's vacated spot (X=PWP_P02_X); Ø127 × 200 (= ACC-01)
    p.append(draw.ruby_cylinder("ACC-02 Accumulator", ACC2_X, ov.PWP_FILTER_YD, ACC2_Z0, cp.ACC_R, 174, color=draw.C_ACC))
    p.append(draw.ruby_cylinder("ACC-02 head", ACC2_X, ov.PWP_FILTER_YD, ACC2_Z0 + 174, cp.ACC_R + 2, 26, color="#222228", axis="z"))
    # ACC-02 IN/OUT ports — ACC-01 style (horizontal, opposite sides at the body BOTTOM); on ±X here since
    # the −Yd side faces the wall.  IN +X (from the P-02 discharge), OUT −X (to BV-05 / the spray bar).
    acc2z = ACC2_Z0 + 28                                 # port Z at the body bottom (= ACC-01's ACC_PZ offset)
    for tag, sd in (("in", +1), ("out", -1)):
        x0 = (ACC2_X + cp.ACC_R) if sd > 0 else (ACC2_X - cp.ACC_R - 30)
        p.append(draw.ruby_cylinder(f"ACC-02 {tag} port", x0, ov.PWP_FILTER_YD, acc2z, cp.RP, 30, color="#222228", axis="x"))
    return "\n".join(p)


def skid_plumbing(part="all"):
    """Phase 2 — relocated tray-sump plumbing on the filter skid.  Legs are tagged by the
    construction-model phase they install in — 'skid' (3.5: row + recycle-feed + spray) or
    'ribbon' (3.2/1.3: sump suction + waste + P-02 feed, the under-walkway/corridor runs).
    part='all' (default) returns every leg in build order (byte-identical to the water.skp build)."""
    p = []
    rp = ov.PUMP_PIPE_OD / 2
    lz = SROW_Z0 + 162                                   # 1312 — row line AT P-04's OUT-port height (straight run, no dog-leg)
    # ── Leg 1: tray sump pickup → P-04 IN  (DIRECT — deletes the long corridor ribbon) ──
    sfz = ov.PROC_TRAY_FLOOR_Z_LOW - ov.PROC_TRAY_SUMP_Z + 3
    p04_in = cp.pump_in(ov.PWP_FILTER_X1, SROW_YD, SROW_Z0, "x", face=+1)   # (3220,130,1312)
    sfoot = (ov.PROC_TRAY_DRAIN_X, SROW_YD, sfz)                         # (2399, 104, 3) — strainer in the well, DIRECTLY under the riser (Yd104 also clears the blue trunk at Yd69)
    riser_top_z = ov.WALKWAY_H                                          # 140 — reach the wall at the walkway deck level (the −Yd turn), then rise up the wall before turning to the panel
    wall_run_z  = ov.SUMP_SUCTION_WALL_RUN_Z                            # along-wall horizontal height — ABOVE the near-walkway cantilever wall-plates (top Z200) so neither the pipe nor its clips foul a cantilever (single-sourced; the pinhole-wall elevation reads the same constant)
    p.append(draw.ruby_pipe_run("Tray sump -> P-04 suction",
        [sfoot,                                                          # strainer foot at the sump bottom
         (ov.PROC_TRAY_DRAIN_X, SROW_YD, riser_top_z),                   # RISER up through the walkway grate to 150mm above the deck (no tall wall riser)
         (ov.PROC_TRAY_DRAIN_X, SKID_CLIP_YD, riser_top_z),             # 90° TURN toward the pinhole wall (−Yd to the clip plane) at the walkway deck level
         (ov.PROC_TRAY_DRAIN_X, SKID_CLIP_YD, wall_run_z),              # RISE vertically up the wall to clear the cantilever wall-plates (top Z200) BEFORE turning to the panel
         (p04_in[0] - 40, SKID_CLIP_YD, wall_run_z),                   # 90° TURN along the pinhole wall: +X above the plates, hugging the ply, toward P-04
         (p04_in[0] - 40, SKID_CLIP_YD, p04_in[2]),                     # climb the panel face to P-04's IN height
         (p04_in[0] - 40, SROW_YD, p04_in[2]),                          # +Yd back to the P-04 IN lane
         p04_in], rp, color=draw.C_IBC_BROWN))                           # short lead into P-04's IN port
    p.append(cp.sump_strainer_foot())                                  # shared single source (same part in the corridor sump)
    # ── Leg 2: P-04 OUT → (SV-02 tap) → DV-02 IN, along the row at lz ──
    p04_out = cp.pump_out(ov.PWP_FILTER_X1, SROW_YD, SROW_Z0, "x", face=+1)   # (3380,130,1312)
    dv_in = (ov.PWP_FILTER_X3 - (cp.DVB / 2 + cp.DVL), SROW_YD, lz)     # DV-02 −X run port (3943,130,1250)
    # the line runs THROUGH SV-02's in-line body at X2 (so no separate tap tee — the sample spout hangs below)
    p.append(draw.ruby_pipe_run("P-04 -> SV-02 -> DV-02",
        [p04_out, (dv_in[0], SROW_YD, lz)], rp, color=draw.C_IBC_BROWN))   # STRAIGHT: lz = P-04 OUT Z (no dog-leg)
    # ── Leg 3a: DV-02 feed (z+ branch) → F1 IN — the RECYCLE leg into the filter train ──
    fr = ov.BB_OD / 2
    f1_in = (ov.PWP_FILTER_X1 - (fr + 30), ov.PWP_FILTER_YD, ov.PWP_FILTER_TOP_Z - 39)   # (3178,104,2301) — matches f_in("F1")
    dv_feed = (ov.PWP_FILTER_X3, SROW_YD, lz + (cp.DVB / 2 + cp.DVL))               # DV-02 z+ branch port (3976,104,1283)
    edge_x = 2830        # near the panel's low-X (pinhole) edge
    p.append(draw.ruby_pipe_run("DV-02 feed -> F1 (recycle)",
        [dv_feed,
         (ov.PWP_FILTER_X3, ov.PWP_FILTER_YD, 1450),      # up just clear of the skid-row tops (~1360)
         (edge_x, ov.PWP_FILTER_YD, 1450),                # −X to the pinhole edge (Yd104)
         (edge_x, SKID_CLIP_YD, 1450),                    # −Yd onto the skid clip plane (#29: flush on the panel)
         (edge_x, SKID_CLIP_YD, f1_in[2]),                # VERTICAL UP on the panel face to F1-IN height
         (edge_x, ov.PWP_FILTER_YD, f1_in[2]),            # +Yd back to the filter lane
         f1_in], rp, color=draw.C_IBC_BROWN))               # +X into F1's −X IN port
    # ── Leg 3b: DV-02 waste (+X port) → IBC-4 (corridor), UNDER THE WALKWAY via the ribbon ──
    # Mirrors the (now-freed) tray-sump ribbon path: out to the near-rim lane FIRST (clear of the tray
    # basin), drop, +X under the walkway to lane 2, up-and-over the cantilever, down into the corridor,
    # then rise onto the IBC-4 merge tee.
    RZ, OVZ = cp.RIBBON_Z, cp.RIBBON_OVER_Z
    wlx   = cp.RIBBON_LANE_X[2]                           # lane 2 — freed now the sump goes direct to P-04
    gapyd = ov.RWK_RIBBON_NOTCH_YDS[2]                    # 1194 — lane-2 outer-beam notch Yd (single-sourced)
    CLIPY = 35                                            # clip plane — flush to the ply (= the F3→SV-01 filtered-line Yd), so the grey clamps to the panel
    dv_waste = (ov.PWP_FILTER_X3 + (cp.DVB / 2 + cp.DVL), SROW_YD, lz)   # DV-02 +X waste port (4054,104,1312)
    riseX = cp.MERGE4[0] - 115                            # 5289 — seat-approach X (= old DV-02→IBC-4 drop lane, −x of the tee)
    p.append(draw.ruby_pipe_run("DV-02 waste -> IBC-4",
        [dv_waste,
         (dv_waste[0] + 36, SROW_YD, lz),                 # +X lead-out off the +X waste port
         (dv_waste[0] + 36, SROW_YD, 1050),               # DROP to the raised panel-bottom grey lane (Z1050 — 100mm above the brown bottom run Z948)
         (dv_waste[0] + 36, CLIPY, 1050),                 # −Yd onto the clip plane (clamped to the ply)
         (wlx, CLIPY, 1050),                              # +X along the ply to lane 2 (clear of the relocated SV-01 at X3976)
         (wlx, 65, 1050),                                 # +Yd clear of the RWk end beam (Yd0) before dropping
         (wlx, 65, RZ),                                   # DROP between the walkway beams into the ribbon (past the end beam, in front of the tray box)
         (wlx, cp.RIBBON_YD_UP, RZ),                      # +Yd along the lane (under the grate) to before the cantilever
         (wlx, cp.RIBBON_YD_UP, OVZ),                     # UP over the cantilever (Rule 5)
         (wlx, cp.RIBBON_YD_DOWN, OVZ),                   # +Yd past the cantilever
         (wlx, cp.RIBBON_YD_DOWN, RZ),                    # DOWN through the grate into the corridor
         (wlx, gapyd, RZ),                                # +Yd to the notch Yd (flush under the grate)
         (cp.RIBBON_SLOT_X, gapyd, RZ),                   # +X through the outer-beam notch to the drop slot
         (cp.RIBBON_SLOT_X, gapyd, 65),                   # DOWN the slot to the corridor-entry Z (Z65)
         (cp.BACK_X - 44, gapyd, 65),                     # +X at the low floor Z PAST the P-02->ACC-02 recycle crossing (X4900, Z97) — stays ~32mm below it, no crossing
         (cp.BACK_X - 44, gapyd, 90),                     # HOP UP just before the IBC frame's REAR bottom ring-rail (full-height, top Z65) — the corridor is open above here (between the tote columns), clear headroom
         (riseX, gapyd, 90),                              # +X OVER the rear ring-rail to the merge-approach lane, held at Z90 (the front rail is already low at Z49 and clears)
         (riseX, cp.MERGE4[1], 90),                       # jog to the merge Yd, still above the ring-rail
         (riseX, cp.MERGE4[1], cp.MERGE4[2]),             # RISE to the merge Z (1230)
         cp.MERGE4], rp, color=draw.C_IBC_WASTE))           # +X onto the tee's −x run port
    # ── Leg 4: P-02 discharge (corridor) → ACC-02 (skid) — the recycle-spray feed, UNDER THE WALKWAY ──
    # Reverse of the waste leg: off P-02's +Yd OUT, drop into the corridor, ribbon lane 0 back under the
    # walkway to the near rim, then −X along the near rim to the skid and up into ACC-02's bottom IN.
    p2o = cp.pump_out(cp.PXC, cp.CTR_Y, cp.PSTACK["P-04"], "y", 1)      # P-02 OUT (+Yd) (4984,1261,1102)
    L0  = cp.RIBBON_LANE_X[0]                                           # lane 0
    g0  = ov.RWK_RIBBON_NOTCH_YDS[0]                                    # lane-0 outer-beam notch Yd (1110)
    acc2_in = (ACC2_X + cp.ACC_R + 30, ov.PWP_FILTER_YD, ACC2_Z0 + 28)   # ACC-02 +X IN-port tip (3770.5,104,948)
    exitX = 4900                                                        # −X of the ACC-01/P-01 column (bodies X≥4921) so the drop clears them
    cpt = (4616, g0 + 13, RZ)                                           # ribbon entry at flush Z (flush branch); Yd1123 — nudged +Yd toward the film-plane wall so the flush run + hump-rise clear the cantilever +Yd edge (Yd1097) by ~15mm; X pulled −X to clear the J6 end-plate (−X face X4646)
    npt = (L0, 65, RZ)                                                  # near-rim junction (Yd65, clear of the end beam)
    rpy = cp.SB_RISER_YD_FAR                                            # 1285 — P-02 discharge riser on the FAR support board (flush)
    midz = RZ                                                          # flush ribbon Z
    lead  = [p2o, (p2o[0], rpy, p2o[2]),                                # +Yd OUT of the +Yd OUT port onto the board riser plane
             (exitX, rpy, p2o[2]),                                      # −X OUT of the pump column (+Yd side, above P-01/ACC-01)
             (exitX, rpy, midz),                                        # DROP to the flush ribbon Z
             (exitX, cpt[1], midz),                                     # −Yd to the ribbon-entry Yd (1123)
             cpt]                                                       # −X STRAIGHT back to the 90° ribbon-entry turn — no duck (the lowered blue trunk at z210 clears it)
    cross = cp.ribbon_run(0, cpt, npt)                                  # cpt → over the cantilever → npt
    tail  = [npt, (L0, 65, acc2_in[2]), (L0, CLIPY, acc2_in[2]),
             (acc2_in[0] + 55, CLIPY, acc2_in[2]),
             (acc2_in[0] + 55, ov.PWP_FILTER_YD, acc2_in[2]), acc2_in]
    p.append(draw.ruby_pipe_run("P-02 -> ACC-02 (recycle spray)",
        lead[:-1] + cross + tail[1:], rp, color=draw.C_IBC_BROWN))
    # ── Leg 5: ACC-02 OUT (−X) → 3W-BV-05 recycled port — closes the recycle-spray loop ──
    acc2_out = (ACC2_X - cp.ACC_R - 30, ov.PWP_FILTER_YD, ACC2_Z0 + 28)   # ACC-02 −X OUT tip (3583.5,104,948)
    b5rx = (ov.BV05_X - 150) + (cp.DVB / 2 + cp.DVL)                             # BV-05 +X recycled port tip X (2282)
    zb = acc2_out[2]                                        # 948 — panel-bottom run height (= ACC-02 OUT)
    p.append(draw.ruby_pipe_run("ACC-02 -> BV-05 (recycled spray)",
        [acc2_out,                                          # off ACC-02's −X OUT port (collinear −X)
         (acc2_out[0] - 55, ov.PWP_FILTER_YD, zb),          # −X lead-out off the OUT port
         (acc2_out[0] - 55, CLIPY, zb),                     # −Yd onto the ply clip plane — CLAMPED to the panel face
         (3210, CLIPY, zb),                                 # −X toward BV-05, to just +X of the P-04 suction riser (X3180)
         (3210, CLIPY + 40, zb),                            # +Yd HUMP out over the P-04 suction riser (now nudged to Yd35, #29) — passes in front
         (3150, CLIPY + 40, zb),                            # −X across, clear of the riser
         (3150, CLIPY, zb),                                 # −Yd back onto the ply clip plane
         (b5rx + 40, CLIPY, zb),                            # −X along the panel bottom, HUGGING the ply, to BV-05
         (b5rx + 40, CLIPY, 700),                           # DROP to the BV-05 recycled-port height
         (b5rx + 40, 69, 700),                              # +Yd to the BV-05 lane (Yd69)
         (b5rx, 69, 700)], rp, color=draw.C_IBC_BROWN))       # −X into the +X recycled port
    # ── #29: skid-panel riser P-clips — hold the nudged vertical runs flush to the ply (face Yd18) ──
    skid_face = 18
    for rx, cz_lo, cz_hi in ((edge_x, 1520, 2120),               # DV-02 feed → F1 riser (X2830)
                             (p04_in[0] - 40, 600, 1080),        # tray sump → P-04 riser (X3180)
                             (ov.PWP_SV01_X - 60, 1780, 2160)):  # F3 → SV-01 wall drop (X4190)
        for cz in (cz_lo, cz_hi):
            p.append(draw.ruby_box("Skid riser P-clip", rx - 14, skid_face, cz - 8,
                                 28, (SKID_CLIP_YD + rp + 2) - skid_face, 16, color=cp.C_CLIP))
    # horizontal-run clamps flagged in review — brown ± ACC-02 (on the panel-bottom lane), blue ±
    # SV-01, and the brown row line → DV-02.  Same clip, bridging each run back to the ply face.
    for rx, ryd, cz in ((3720, 35, 948),  (3970, 35, 948),     # brown ± ACC-02 (panel-bottom lane, flush)
                        (2500, 35, 948), (2800, 35, 948), (3100, 35, 948),   # ACC-02→BV-05 recycle run (−X toward BV-05, ~300mm)
                        (3370, 35, 948),                                      # ACC-02→BV-05 run (+X segment, past the P-04 riser hump)
                        (4150, 35, 948), (4380, 35, 948),                     # P-02→ACC-02 recycle run (panel-bottom lane)
                        (4150, 35, 1050), (4350, 35, 1050),                   # DV-02 waste → IBC-4 run (higher lane, Z1050)
                        (3050, 104, 1450), (3350, 104, 1450), (3650, 104, 1450), (3900, 104, 1450),  # DV-02 feed → F1 recycle run (Z1450, filter lane — 1104mm, ~300mm)
                        (4230, 110, 1610), (4370, 110, 1610),  # blue ± SV-01 (forward valve lane — standoff)
                        (3560, 104, 1312), (3820, 104, 1312)): # brown row line → DV-02 (kit-row lane — standoff)
        p.append(draw.ruby_box("Skid pipe P-clip", rx - 8, skid_face, cz - 14,
                             16, (ryd + rp + 2) - skid_face, 28, color=cp.C_CLIP))   # horizontal run: band thin in X, wraps in Z (⊥ the pipe)
    # Tray-sump suction supports (relocated routing): standard P-clips on the new along-wall
    # horizontal (Yd35, at the walkway deck level) + a low clip on the X3180 panel climb (it now
    # starts at the deck).  Each bridges the run back to its backing face — the bare container wall
    # (Yd0) left of the ply panel edge (PWP_PANEL_X0=2780), the ply face (Yd18) on the panel.
    # clips sit in the clear gaps BETWEEN the near-walkway cantilevers (Near 5 X2576-2696,
    # Near 6 X3033-3153) so no support bracket lands on a cantilever arm/plate.
    for rx, face in ((2520, 0), (2760, 0), (2980, skid_face)):   # along-wall horizontal run (at wall_run_z)
        p.append(draw.ruby_box("Skid pipe P-clip", rx - 8, face, wall_run_z - 14,
                             16, (SKID_CLIP_YD + rp + 2) - face, 28, color=cp.C_CLIP))   # horizontal along-wall run: band ⊥ the pipe
    p.append(draw.ruby_box("Skid riser P-clip", (p04_in[0] - 40) - 14, skid_face, 340 - 8,
                         28, (SKID_CLIP_YD + rp + 2) - skid_face, 16, color=cp.C_CLIP))   # P-04 climb, low (joins the 600/1080 clips)
    # WALL-STANDOFF riser clips — the DV-02-waste + P-02→ACC-02 corridor drops run BELOW the ply panel
    # (Z<920) in front of the BARE pinhole wall (Yd0), ~65mm off it; they mount to the wall on a ~55mm
    # standoff block (the box spans Yd0→pipe). Vertical pipe → band thin in Z (28×16).
    for rx, ryd in ((4400, 60), (4434, 65), (4503, 65)):   # SV-01→DV-01 (blue), DV-02 waste, P-02→ACC-02 — the 3 corridor-drop risers
        for cz in (300, 550, 800):                    # ~300mm down the drop, all below the panel bottom (Z920)
            p.append(draw.ruby_box("Wall-standoff riser P-clip", rx - 14, 0, cz - 8,
                                 28, (ryd + rp + 2), 16, color=cp.C_CLIP))
    if part == "all":
        return "\n".join(p)
    # Partition legs by the construction-model phase they install in, matched on each pipe's own
    # embedded name (no re-ordering — keeps the 'all' path byte-identical to water.skp).
    #   'skid'   (3.5): the on-panel skid-side legs — P-04->SV-02->DV-02, DV-02 recycle-feed->F1, ACC-02->BV-05
    #   'ribbon' (3.2): the under-walkway / corridor legs — tray-sump suction (+strainer), DV-02 waste, P-02->ACC-02
    SKID_LEGS = ("P-04 -> SV-02", "DV-02 feed -> F1", "ACC-02 -> BV-05")
    def _is_skid(s): return any(k in s for k in SKID_LEGS)
    return "\n".join(s for s in p if (part == "skid") == _is_skid(s))


def build():
    # Limited-depth view of the FULL pinhole wall: the wet-end kit + the OTHER wall-mounted
    # equipment (own layer/scene) + a shallow context slice (wall + floor/ceiling out to
    # 300mm past the walkway) + scale figure.  Two scenes: wet end / other equipment.
    comps, tags = [], set()
    # (name, tag, builder) — builders whose tag is in MUTE_TAGS build muted at source via draw.muted().
    for name, tag, builder in [("Context", "Context", context),
                         ("Walkways + cantilevers + brackets", "Walkway", walkway_full),
                         ("Film-plane support beams", "Film Plane", film_plane_beams),
                         ("Processing tray (ghost)", "Processing Tray", processing_tray),
                         ("Spray Bar", "Spray Bar", sb.spray_bar),
                         ("IBC Tanks (full)", "IBC", lambda: ib.ibc_stack(alpha=MUTE_ALPHA, mute=MUTE_DESAT)),
                         ("IBC restraint (bars + wall anchors)", "IBC Frame", cp.tote_restraint),
                         ("End wall (context)", "Context", cp.end_wall),
                         ("Pinhole Assembly", "Pinhole", ov.pinhole_assembly),
                         ("Wall backing (ply)", "Backing", backing),
                         ("TAP-01 + spray-bar supply", "Supply", tap01_supply),
                         ("Wet-end kit (raked)", "Kit", lambda: kit(p02_on_corridor=True)),
                         ("Skid row (P-04 · SV-02 · DV-02)", "Kit", skid_row),
                         ("Skid plumbing", "Kit", skid_plumbing),
                         ("Person (scale)", "Scale", person),
                         ("Other pinhole-wall equipment", "Pinhole Equipment", other_equipment),
                         ("Corridor frame (deep box)", "Corridor Frame", cp.frame),
                         ("Corridor rear panel", "Corridor Panel", cp.rear_panel),
                         ("Corridor equipment", "Corridor Equipment", lambda: cp.equipment(sump_on_skid=True)),
                         ("Corridor plumbing", "Corridor Plumbing", lambda: cp.plumbing(sump_on_skid=True)),
                         ("Corridor drains + X-ports", "Corridor Drains", lambda: cp.drains_ports(sump_on_skid=True)),
                         ("Circuit-C power + cabling (both panels)", "Power", lambda: panel_power(include_switch=False)),
                         ("Ribbon support cross-beams", "Ribbon Supports", cp.ribbon_supports),
                         # SOLID (non-ghost) copy of the wall backing, on its own tag — shown only in the
                         # "Plumbing (labeled)" scene so it reads full-color there while the overview scenes
                         # keep the muted "Backing" version. (The corridor panel is now solid in EVERY scene,
                         # so its former solid duplicate was dropped — see MUTE_TAGS.)
                         ("Wall backing (solid)", "Backing Solid", backing)]:
        if tag in MUTE_TAGS:
            with draw.muted(MUTE_DESAT, MUTE_ALPHA):
                b = builder()
        else:
            b = builder()
        comps.append(draw.component(name, tag, b)); tags.add(tag)
    tags.add("Labels"); tags.add("Labels Context")
    body = "\n".join(comps)
    tags_ruby = "".join(f'  model.layers.add({t!r}) unless model.layers[{t!r}]\n' for t in sorted(tags))
    return f'''# SPDX-License-Identifier: AGPL-3.0-only
# © 2026 Alvin Richards
# Generated from src/models/ — do not edit this .rb directly.
model = Sketchup.active_model
model.start_operation("Pinhole-wall layout", true)
entities = model.active_entities
to_erase = entities.to_a.select {{ |e| e.is_a?(Sketchup::Group) || e.is_a?(Sketchup::ComponentInstance) || e.is_a?(Sketchup::Text) || e.is_a?(Sketchup::ConstructionLine) || e.is_a?(Sketchup::ConstructionPoint) || e.is_a?(Sketchup::Edge) }}
entities.erase_entities(to_erase) unless to_erase.empty?
model.definitions.purge_unused
model.materials.purge_unused
model.layers.purge_unused   # drop orphan tags (e.g. the retired "Corridor Panel Solid") so they don't linger
model.pages.to_a.each {{ |pg| model.pages.erase(pg) }}
opts = model.options["UnitsOptions"]; opts["LengthUnit"]=2; opts["LengthFormat"]=0
{draw.sketchfab_meta_ruby(SF_TITLE, SF_DESC, draw.model_uid("water"), SF_TAGS, force_name=True)}
{tags_ruby}{body}
# remove the FAR walkway deck AND its cantilever brackets (not wanted in this view)
model.definitions.each {{ |d| d.entities.grep(Sketchup::Group).each {{ |g| g.erase! if g.valid? && g.name =~ /^Walkway Far/ }} }}
# in-model callout labels on the 'Labels' tag (shown only in the Labeled scene)
{labels_ruby()}
v = model.active_view
v.camera = Sketchup::Camera.new(Geom::Point3d.new(800.mm, 6000.mm, 2300.mm), Geom::Point3d.new(2950.mm, 200.mm, 1100.mm), Geom::Vector3d.new(0,0,1), false, 52)
# Context/backdrop is built muted AT SOURCE (ov.muted() wraps the MUTE_TAGS builders above), so no
# post-build re-coloring pass is needed.  Keep ModelTransparency OFF so the per-material alpha renders
# as translucency (not a global X-ray that would leak across scenes).
model.rendering_options["ModelTransparency"] = false
def scene(model, name, on)
  model.layers.each {{ |l| l.visible = (l.name == "Layer0" || l == model.layers[0] || on.include?(l.name)) }}
  pg = model.pages.add(name, 4095)
  pg.use_hidden_layers = true rescue nil
  pg
end
scene(model, "Overview", ["Context","Walkway","Film Plane","Processing Tray","Spray Bar","IBC","IBC Frame","Pinhole","Backing","Supply","Kit","Scale","Pinhole Equipment","Corridor Frame","Corridor Panel","Corridor Equipment","Corridor Plumbing","Corridor Drains","Power"])
scene(model, "Plumbing", ["Kit","Supply","Corridor Equipment","Corridor Plumbing","Corridor Drains","Power","Corridor Panel"])
scene(model, "Plumbing (labeled)", ["Kit","Supply","Corridor Equipment","Corridor Plumbing","Corridor Drains","Power","Labels","Corridor Panel","Backing Solid"])
scene(model, "Plumbing + IBC", ["Kit","Supply","Corridor Equipment","Corridor Plumbing","Corridor Drains","Power","IBC","IBC Frame","Corridor Frame","Corridor Panel","Walkway"])
scene(model, "Labeled", ["Context","Walkway","Film Plane","Processing Tray","Spray Bar","IBC","IBC Frame","Pinhole","Backing","Supply","Kit","Scale","Pinhole Equipment","Corridor Frame","Corridor Panel","Corridor Equipment","Corridor Plumbing","Corridor Drains","Power","Labels","Labels Context"])
model.layers.each {{ |l| l.visible = true }}
model.commit_operation
{{ ok: true }}.to_json
'''


RB_PATH = os.path.join(_HERE, "water.rb")

if __name__ == "__main__":
    ap = argparse.ArgumentParser()
    ap.add_argument("--send", action="store_true", help="build into the ACTIVE SketchUp doc (open a blank doc first!)")
    ap.add_argument("--save", action="store_true",
                    help="write src/models/water.rb (deterministic, byte-verifiable by lint --verify-all). "
                         "Does NOT save the .skp — ALVIN saves the live doc after --send (single-writer protocol).")
    a = ap.parse_args()
    ruby = build()
    if a.save:
        with open(RB_PATH, "w") as f:
            f.write(ruby)
        print(f"  {RB_PATH} saved ({len(ruby)} bytes)")
    if a.send:
        from sketchup_client import send_ruby
        print(send_ruby(ruby))
        # NEVER Sketchup.active_model.save() the .skp via MCP — single-writer protocol. `--send` only
        # rebuilds the live doc; ALVIN saves the .skp (File>Save) + re-uploads to Sketchfab. A direct
        # save here overwrote water.skp under ALVIN's open doc (2026-08-13, "file on disk changed"
        # conflict) — every other model leaves saving to ALVIN, and so must this one. Do not re-add it.
    if not a.send and not a.save:
        print(ruby[:400])
