alvinr/tbs/src/models/tbs_draw.py

#!/usr/bin/env python3
# SPDX-License-Identifier: AGPL-3.0-only
# © 2026 Alvin Richards
"""
tbs_draw.py — Neutral drawing + material primitives for the TBS-001 SketchUp models.

The generic Ruby-emitting helpers (mm, ruby_box/cylinder/prism/pipe/pipe_run/..., component,
material + mute/ghost machinery, vector math) shared by EVERY model generator. Extracted from
generate_sketchup_model.py (Phase 0 of the model-aggregation plan) so no model imports the
"overview" module just to draw — overview becomes a pure aggregator.

Holds the SHARED mutable build state (_MAT_BY_COLOR material registry, the muted()/_CTX_* ghost
context). Import this module (e.g. `import tbs_draw as draw`) so every reader sees the one live
state; do NOT `from tbs_draw import _CTX_FORCE` (that copies a stale binding).
"""
import math
import contextlib
import os
import sys

sys.path.insert(0, os.path.join(os.path.dirname(__file__), "..", "generators"))

def mm(val):
    """Render a millimeter value as a Ruby literal carrying the `.mm` suffix.

    SketchUp's geometry database is always inches internally, but the Ruby API
    converts on input: `2362.mm` yields the correct inch value. Emitting `.mm`
    keeps the generated Ruby readable in the project's native millimeters and
    lets SketchUp do the conversion, rather than baking in pre-divided floats.
    """
    # Drop a trailing ".0" so whole numbers read as 2362.mm, not 2362.0.mm.
    if isinstance(val, float) and val.is_integer():
        val = int(val)
    return f"{val}.mm"
_CANON_RGB = {
    # tight greys / near-blacks (Δ≤6)
    (32, 32, 32): (26, 26, 26),
    (34, 34, 40): (26, 26, 26), (34, 34, 34): (26, 26, 26),
    (43, 43, 48): (42, 42, 42), (44, 44, 44): (42, 42, 42),
    (58, 58, 58): (51, 52, 58), (58, 58, 66): (51, 52, 58),
    (80, 80, 88): (80, 80, 90),
    (96, 96, 104): (88, 96, 112),
    (122, 128, 136): (128, 128, 138),
    (126, 126, 118): (119, 119, 119), (128, 128, 128): (119, 119, 119),
    (154, 160, 160): (154, 160, 166), (154, 160, 168): (154, 160, 166),
    (192, 192, 200): (184, 188, 196),
    (200, 176, 106): (200, 176, 112),
    (216, 207, 188): (216, 208, 188),
    # same-hue color pairs (Δ≤10) — blue / yellow, imperceptible
    (41, 128, 185): (41, 121, 184),
    (245, 197, 24): (241, 196, 15),
}
def hex_to_rgb(h):
    """Convert '#RRGGBB' to (r, g, b), collapsing near-identical colors to a canonical value so
    they share a material (holds the Sketchfab material count down)."""
    h = h.lstrip("#")
    rgb = (int(h[0:2], 16), int(h[2:4], 16), int(h[4:6], 16))
    return _CANON_RGB.get(rgb, rgb)
MUTE_NEUTRAL = (190, 190, 195)
GHOST_HEX = "#8C929B"   # single neutral blue-gray for ALL forced-ghost context (construction prior phases)
def mute_hex(h, f, neutral=MUTE_NEUTRAL):
    """Blend a '#RRGGBB' color a fraction `f` toward `neutral` (0 = unchanged, 1 = full
    neutral).  Used to desaturate ghosted context (e.g. IBC tanks) so strong circuit
    colors don't bury the key components — matches the muted feel of overview.skp.
    Under a forced-muted (ghost) context, ALL colors collapse to the single GHOST_HEX so the
    faded prior-phase context reads as one uniform gray (easiest to read against the current
    phase's full-color additions) and shares ONE material (Sketchfab caps materials at ~100)."""
    if _CTX_FORCE:
        return GHOST_HEX
    if not f:
        return h
    r, g, b = hex_to_rgb(h)
    nr, ng, nb = neutral
    blend = lambda c, n: round(c * (1 - f) + n * f)
    return "#%02X%02X%02X" % (blend(r, nr), blend(g, ng), blend(b, nb))
_MAT_BY_COLOR = {}
def shared_mat_name(name, color, alpha):
    """Return a material name shared by every element of the same CANONICAL color + alpha.
    Under a forced-muted (ghost) context the name is namespaced ('ghost ' prefix) and keyed
    separately, so a ghosted static copy never collides on the same material as its full-color
    live twin (same group name, different color/alpha). Outside a forced context this is
    byte-identical to before (the key gains a constant False prefix; the returned name is unchanged)."""
    key = (_CTX_FORCE, hex_to_rgb(color), alpha if alpha is not None else 1.0)
    return _MAT_BY_COLOR.setdefault(key, ("ghost " + name) if _CTX_FORCE else name)
_CTX_MUTE, _CTX_ALPHA, _CTX_FORCE = 0.0, None, False
@contextlib.contextmanager
def muted(mute, alpha, force=False):
    """Within this block, drawing helpers build muted CONTEXT/backdrop geometry at source.
    force=True makes the context's mute/alpha WIN over whatever the caller passes — so builders
    that hardcode their own alpha/mute (e.g. ibc_stack(alpha=0.85)) are still fully ghosted."""
    global _CTX_MUTE, _CTX_ALPHA, _CTX_FORCE
    prev = (_CTX_MUTE, _CTX_ALPHA, _CTX_FORCE)
    _CTX_MUTE, _CTX_ALPHA, _CTX_FORCE = mute, alpha, force
    try:
        yield
    finally:
        _CTX_MUTE, _CTX_ALPHA, _CTX_FORCE = prev
def _mute_ctx(mute, alpha):
    """Resolve a helper's mute/alpha against the current muted() context (idempotent).
    Under force, the context values override the caller's; otherwise the caller's explicit
    (non-None) values win, so outside a muted() block this is byte-identical to passing them through."""
    if _CTX_FORCE:
        return (_CTX_MUTE, _CTX_ALPHA if _CTX_ALPHA is not None else alpha)
    return (_CTX_MUTE if mute is None else mute, _CTX_ALPHA if alpha is None else alpha)
def ruby_box(name, x, y, z, w, d, h, color=None, alpha=None, both_sides=False, mute=None,
             holes=None, hole_axis=None):
    """Generate Ruby to create a named box group inside the `ents` context.

    Parameters are in mm. x, y, z: origin corner (min X, min Yd, min Z).
    w, d, h: width (X), depth (Yd), height (Z). Boxes are added to `ents`,
    the entities collection of the enclosing component definition.
    `both_sides` paints the back faces too (so interior + exterior read the
    same — used for the container shell).

    `holes` cuts real drilled clearance holes THROUGH the panel (a void, not a
    part — so a pipe/cable reads as passing through a hole, not fused into the
    slab; see check_interference.py --pipes).  Each hole is `(a, b, r)` in mm
    world coords of the two in-plane axes, radius r, cut along `hole_axis`
    ("x"/"y"/"z" — the panel's thin axis): x→(yd,z), y→(x,z), z→(x,yd).  The
    cutter is oversized ±2mm so it cleanly penetrates both faces via
    Group#subtract; material is applied to the resulting solid.
    """
    mute, alpha = _mute_ctx(mute, alpha)
    # Sum in millimeters first, then render each corner with the `.mm` suffix.
    x0, y0, z0 = mm(x), mm(y), mm(z)
    x1, y1 = mm(x + w), mm(y + d)
    h_mm = mm(h)

    lines = [
        f'  # {name}',
        f'  grp = ents.add_group',
        f'  grp.name = "{name}"',
        f'  face = grp.entities.add_face('
        f'[{x0},{y0},{z0}], [{x1},{y0},{z0}], '
        f'[{x1},{y1},{z0}], [{x0},{y1},{z0}])',
        f'  face.reverse! if face.normal.z < 0',
        f'  face.pushpull({h_mm})',
    ]

    if holes:
        # Cut real drilled clearance holes by drawing each circle COPLANAR on the panel's NEAR face and
        # pushpulling it through the thickness.  (Group#subtract does NOT chain in this SketchUp — the 2nd
        # boolean silently collapses the solid to garbage; coplanar-face pushpull is robust and adds one
        # clean 24-segment hole each, staying manifold.)  Keep each hole a safe MARGIN inside the panel
        # on both in-plane axes so a near-edge razor sliver can't form.
        span = {"x": (x, x + w, w), "y": (y, y + d, d), "z": (z, z + h, h)}[hole_axis]
        inplane = {"x": ((y, y + d), (z, z + h)),
                   "y": ((x, x + w), (z, z + h)),
                   "z": ((x, x + w), (y, y + d))}[hole_axis]
        normal = {"x": "[1,0,0]", "y": "[0,1,0]", "z": "[0,0,1]"}[hole_axis]
        near, thick = span[0], span[2]
        MARGIN = 5.0

        def _clamp(v, lo, hi, r):
            return min(max(v, lo + r + MARGIN), hi - r - MARGIN)
        for a, b, r in holes:
            a = _clamp(a, inplane[0][0], inplane[0][1], r)
            b = _clamp(b, inplane[1][0], inplane[1][1], r)
            if hole_axis == "x":
                cc = f'[{mm(near)},{mm(a)},{mm(b)}]'
            elif hole_axis == "y":
                cc = f'[{mm(a)},{mm(near)},{mm(b)}]'
            else:
                cc = f'[{mm(a)},{mm(b)},{mm(near)}]'
            lines += [
                f'  hcirc = grp.entities.add_circle({cc}, {normal}, {mm(r)}, 24)',
                f'  hdisk = hcirc.map {{ |e| e.faces }}.flatten.uniq.min_by {{ |ff| ff.area }}',
                f'  hdisk.reverse! if hdisk.normal.{hole_axis} < 0',   # normal into the solid
                f'  hdisk.pushpull({mm(thick)})',                       # through to the far face → hole
            ]

    if color:
        color = mute_hex(color, mute)
        r, g, b = hex_to_rgb(color)
        # Reuse the material if it already exists so re-sends don't pile up
        # "Container Ceiling2", "Container Ceiling3", … duplicates.
        mat_nm = shared_mat_name(name, color, alpha)
        lines.append(f'  mat = model.materials["{mat_nm}"] || '
                     f'model.materials.add("{mat_nm}")')
        lines.append(f'  mat.color = Sketchup::Color.new({r}, {g}, {b})')
        # Always set alpha (default opaque) so a reused material can't keep a
        # stale translucency from an earlier run.
        lines.append(f'  mat.alpha = {alpha if alpha is not None else 1.0}')
        lines.append(f'  grp.material = mat')
        if both_sides:
            lines.append(f'  grp.entities.grep(Sketchup::Face).each '
                         f'{{ |f| f.material = mat; f.back_material = mat }}')

    lines.append('')
    return '\n'.join(lines)
def ruby_prism(name, pts, z, h, color=None, alpha=None, mute=None, holes=None):
    """A vertical prism from an arbitrary polygon (list of (x, y) mm points) at height z,
    pushpulled up by h. Same material handling as ruby_box. Used for NOTCHED grates so the deck
    is ONE continuous piece (a bite cut out of one edge), not separate sections needing support.

    `holes` cuts real drilled clearance cutouts THROUGH the slab (along its Z thickness) so a pipe
    reads as passing through a hole/slot, not fused into the deck (see check_interference.py --pipes).
    Each entry is either a ROUND hole `(cx, cy, r)` or a rectangular SLOT `(x0, y0, x1, y1)`, in mm
    XY world coords; each must sit strictly INSIDE the polygon (coplanar-face pushpull, same robust
    drill as ruby_box — Group#subtract chaining is unreliable in this SketchUp)."""
    mute, alpha = _mute_ctx(mute, alpha)
    z0, h_mm = mm(z), mm(h)
    face_pts = ", ".join(f"[{mm(px)},{mm(py)},{z0}]" for px, py in pts)
    lines = [
        f'  # {name}',
        f'  grp = ents.add_group',
        f'  grp.name = "{name}"',
        f'  face = grp.entities.add_face({face_pts})',
        f'  face.reverse! if face.normal.z < 0',
        f'  face.pushpull({h_mm})',
    ]
    for hole in (holes or []):
        if len(hole) == 3:                                   # round hole (cx, cy, r)
            cx, cy, r = hole
            lines.append(f'  hc = grp.entities.add_circle([{mm(cx)},{mm(cy)},{z0}], [0,0,1], {mm(r)}, 24)')
            lines.append('  hf = hc.map { |e| e.faces }.flatten.uniq.min_by { |ff| ff.area }')
        else:                                                # rectangular slot (x0, y0, x1, y1)
            x0, y0, x1, y1 = hole
            lines.append(f'  hf = grp.entities.add_face('
                         f'[{mm(x0)},{mm(y0)},{z0}], [{mm(x1)},{mm(y0)},{z0}], '
                         f'[{mm(x1)},{mm(y1)},{z0}], [{mm(x0)},{mm(y1)},{z0}])')
        lines.append('  if hf; hf.reverse! if hf.normal.z < 0; hf.pushpull(%s); end' % h_mm)   # through to the far face → cutout
    if color:
        color = mute_hex(color, mute)
        r, g, b = hex_to_rgb(color)
        mat_nm = shared_mat_name(name, color, alpha)
        lines.append(f'  mat = model.materials["{mat_nm}"] || model.materials.add("{mat_nm}")')
        lines.append(f'  mat.color = Sketchup::Color.new({r}, {g}, {b})')
        lines.append(f'  mat.alpha = {alpha if alpha is not None else 1.0}')
        lines.append(f'  grp.material = mat')
    lines.append('')
    return '\n'.join(lines)
def component(defn_name, tag, body):
    """Wrap a body of ruby_box calls into a ComponentDefinition + instance.

    The body builds geometry into `ents`; we then place one instance and put
    it on `tag`.
    """
    return f'''  # ═══ {defn_name} ═══
  defn = model.definitions.add("{defn_name}")
  ents = defn.entities
{body}
  inst = entities.add_instance(defn, Geom::Transformation.new)
  inst.name = "{defn_name}"
  inst.layer = model.layers["{tag}"]
'''
def ruby_cone_wire(name, apex, base, tag):
    """Generate Ruby for a wireframe pyramid (edges only) in `ents`.

    apex: (x, y, z). base: 4 (x, y, z) corners. The edges are assigned to
    `tag`, whose line style is set to dashed in the main script — so the cone
    reads as dashed guidance geometry rather than a solid system.
    """
    a = f'[{mm(apex[0])},{mm(apex[1])},{mm(apex[2])}]'
    b = [f'[{mm(p[0])},{mm(p[1])},{mm(p[2])}]' for p in base]
    return '\n'.join([
        f'  # {name}',
        f'  grp = ents.add_group',
        f'  grp.name = "{name}"',
        f'  ge = grp.entities',
        f'  apex = {a}',
        f'  b0 = {b[0]}; b1 = {b[1]}; b2 = {b[2]}; b3 = {b[3]}',
        f'  edges = []',
        f'  edges.concat(ge.add_edges(b0, b1, b2, b3, b0))',
        f'  edges << ge.add_line(apex, b0)',
        f'  edges << ge.add_line(apex, b1)',
        f'  edges << ge.add_line(apex, b2)',
        f'  edges << ge.add_line(apex, b3)',
        f'  lyr = model.layers["{tag}"]',
        f'  edges.each {{ |e| e.layer = lyr if e.is_a?(Sketchup::Edge) }}',
        '',
    ])
def ruby_cylinder(name, cx, cy, cz, radius, height, color=None, alpha=None,
                  n=24, axis="z", mute=None):
    """Generate Ruby for a cylinder in `ents`, axis along +x/+y/+z.

    (cx, cy, cz): center of the base circle. radius/height in mm. Used for
    round bodies (filters, drum, ducts, pipe stubs, fans).
    """
    mute, alpha = _mute_ctx(mute, alpha)
    normal = {"z": "[0,0,1]", "y": "[0,1,0]", "x": "[1,0,0]"}[axis]
    lines = [
        f'  # {name}',
        f'  grp = ents.add_group',
        f'  grp.name = "{name}"',
        f'  ge = grp.entities',
        f'  circle = ge.add_circle([{mm(cx)},{mm(cy)},{mm(cz)}], '
        f'{normal}, {mm(radius)}, {n})',
        f'  cface = ge.add_face(circle)',
        f'  cface.reverse! if cface.normal.{axis} < 0',
        f'  cface.pushpull({mm(height)})',
    ]
    if color:
        color = mute_hex(color, mute)
        r, g, b = hex_to_rgb(color)
        mat_nm = shared_mat_name(name, color, alpha)
        lines.append(f'  mat = model.materials["{mat_nm}"] || '
                     f'model.materials.add("{mat_nm}")')
        lines.append(f'  mat.color = Sketchup::Color.new({r}, {g}, {b})')
        lines.append(f'  mat.alpha = {alpha if alpha is not None else 1.0}')
        lines.append(f'  grp.material = mat')
    lines.append('')
    return '\n'.join(lines)
def ruby_bolt(name, x, y, z, length, radius=6.0, axis="z", color=None, head="base", nut="far", mute=None):
    """A fastener: an Ø(2·radius) shank from (x,y,z) along +`axis` by `length`, PLUS a hex HEAD and/or hex
    NUT drawn as 6-sided prisms so it reads as a real bolt, not a plain rod.  `head`/`nut` name the end each
    sits on: "base" = the (x,y,z) end, "far" = the (base+length) end, or None (omit — e.g. a nut-less anchor
    or self-drilling screw).  Hex circumradius ≈ 1.65·radius, thickness ≈ 1.35·radius (real hex proportions).
    The head/nut protrude just proud of the shank ends (against the clamped faces)."""
    hex_r, hex_h = radius * 1.65, radius * 1.35
    ai = {"x": 0, "y": 1, "z": 2}[axis]
    out = [ruby_cylinder(name, x, y, z, radius, length, color=color, axis=axis, mute=mute)]
    for kind, end in (("head", head), ("nut", nut)):
        if not end:
            continue
        b = [x, y, z]
        b[ai] += length if end == "far" else -hex_h            # protrude outward past that shank end
        out.append(ruby_cylinder(f"{name} {kind}", b[0], b[1], b[2], hex_r, hex_h,
                                 color=color, axis=axis, n=6, mute=mute))
    return "\n".join(out)
def ruby_tri(name, p1, p2, p3, thick, color=None, alpha=None, mute=None):
    """Triangular plate: a face through p1,p2,p3 pushpulled by `thick` along its
    normal (used for gusset plates)."""
    mute, alpha = _mute_ctx(mute, alpha)
    face = ', '.join(f'[{mm(p[0])},{mm(p[1])},{mm(p[2])}]' for p in (p1, p2, p3))
    out = [
        f'  # {name}',
        '  grp = ents.add_group',
        f'  grp.name = "{name}"',
        '  ge = grp.entities',
        f'  f = ge.add_face({face})',
        f'  f.pushpull({mm(thick)})',
    ]
    if color:
        color = mute_hex(color, mute)
        rr, gg, bb = hex_to_rgb(color)
        mat_nm = shared_mat_name(name, color, alpha)
        out.append(f'  mat = model.materials["{mat_nm}"] || model.materials.add("{mat_nm}")')
        out.append(f'  mat.color = Sketchup::Color.new({rr}, {gg}, {bb})')
        out.append(f'  mat.alpha = {alpha if alpha is not None else 1.0}')
        out.append('  grp.material = mat')
    out.append('')
    return '\n'.join(out)
def ruby_arc_wall(name, cx, cy, r, wall_t, height, gap_center_deg, gap_deg,
                  color=None, alpha=None, n=48, z0=0, mute=0.0):
    """Hollow curved wall (annular sector, extruded in +Z) with a gap.

    The gap (an opening of `gap_deg` centerd on `gap_center_deg`) reads as a
    doorway/entry slot in the cylinder. Built as a closed band polygon (outer
    arc forward + inner arc back) at base height `z0` then pushpulled `height`.
    """
    ri = r - wall_t
    a0 = math.radians(gap_center_deg + gap_deg / 2.0)
    a1 = math.radians(gap_center_deg + 360.0 - gap_deg / 2.0)
    pts = []
    for i in range(n + 1):
        a = a0 + (a1 - a0) * i / n
        pts.append((cx + r * math.cos(a), cy + r * math.sin(a)))
    for i in range(n, -1, -1):
        a = a0 + (a1 - a0) * i / n
        pts.append((cx + ri * math.cos(a), cy + ri * math.sin(a)))
    pts_ruby = ', '.join(f'[{mm(round(x, 2))},{mm(round(y, 2))},{mm(z0)}]' for x, y in pts)
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
