alvinr/tbs/src/models/generate_sketchup_model.py

#!/usr/bin/env python3
# SPDX-License-Identifier: AGPL-3.0-only
# © 2026 Alvin Richards
"""
generate_sketchup_model.py — Generate Ruby code for the TBS-001 "Overview"
SketchUp model.

Reads spatial constants from tbs_constants.py and builds Ruby that creates the
model via the SketchUp MCP plugin (eval_ruby / sketchup_client).

Organization (chosen build convention):
  - Each subsystem is a **ComponentDefinition** placed as one instance.
  - Each instance lives on its own **Tag** (layer) for show/hide.
  - **Scenes** (pages) capture useful visibility states.
  - Re-runs are **idempotent**: ALL prior instances (groups, components, text) are
    erased and their definitions purged before rebuilding — including any manually
    placed 'Sree' scale figure (the person is no longer preserved).

Subsystems / tags:
  Container Shell      → Shell            (ceiling ghosted)
  Walkways             → Walkways
  Processing Tray      → Processing Tray
  Pinhole Assembly     → Pinhole          (mount plate + Ø2.17 aperture)
  Optical Axis         → Optical Axis     (pinhole → film-plane center)
  Film Plane Mechanism → Film Plane       (rails + framed muslin screen)

Usage
-----
    python3 src/models/generate_sketchup_model.py          # print Ruby
    python3 src/models/generate_sketchup_model.py --save   # write overview.rb
    python3 src/models/generate_sketchup_model.py --send    # push to SketchUp
"""

import os
import sys
import math
import argparse

sys.path.insert(0, os.path.join(os.path.dirname(__file__), "..", "generators"))
from tbs_constants import C_LEN, C_WID, C_HGT, WALL_T, PROC_TRAY_X_L, PROC_TRAY_X_R, PROC_TRAY_YD_NEAR, PROC_TRAY_YD_FAR, PROC_TRAY_RIM, PROC_TRAY_FLOOR_Z_LOW, tray_floor_z, WALKWAY_W, WALKWAY_H, WALKWAY_GRATE_T, WALKWAY_FAR_YD, WALKWAY_RIGHT_X, WALKWAY_RIGHT_W, WALKWAY_LEFT_X, WALKWAY_BRACKET_T, WALKWAY_BRACKET_H, CONTAINER_RIB_SPACING, WALKWAY_NEAR_WIDE_W, WALKWAY_NEAR_WIDE_X_L, WALKWAY_NEAR_WIDE_X_R, WALKWAY_LEFT_WIDE_W, WALKWAY_LEFT_WIDE_YD_L, WALKWAY_LEFT_WIDE_YD_R, PH_X, PH_H, PH_D, FP_X_L, FP_X_R, FP_H, FP_Y, RAIL_X_R, RAIL_OFF_BOT, FP_RAIL_WEB, FP_RAIL_FLANGE, FP_RAIL_BUILD_BOT, FP_RAIL_GUIDE_GAP, FP_RAIL_ZC_BOT, FP_RAIL_ZC_TOP, FP_FILM_TOP, BAY_FRONT_X, BAY_WALL_T, PANEL_CENTER_T, PANEL_CORNER_T, PANEL_FLOOR_GAP, PANEL_FAN_BAND_Z, PANEL_CORNER_YD_L, PANEL_CORNER_YD_R, PIVOT_X, PIVOT_YD, SWING_LOCK_DEG, PANEL_CUT_YD, FAR_STRIP_YD0, PIVOT_POST_OD, DRUM_CAGE_X0, DRUM_CAGE_X1, DRUM_CAGE_YD_L, DRUM_CAGE_YD_R, WALKWAY_NEAR_LIFTOUT_X_R, BB_OD, BB_H, EQPANEL_T, IBC_COL_X, IBC_H_1000, IBC_PALLET_H, BLUE_IBC_Y, IBC_FRAME_RHS, IBC_FRONT_BAR_D, IBC_FOOT_PLATE, IBC_FOOT_PLATE_T, IBC_FOOT_BOLT_PCD, IBC_FRONT_FOOT_DX, IBC_FRONT_RAIL_H, IBC_FRONT_RAIL_W, FP_CORNER_SEAT_PLATE_T, DRUM_CX, DRUM_CY, DRUM_R, DRUM_H_LT, LT_HOUSING_R, LT_HOUSING_T, LT_DRUM_OR, LT_DRUM_T, LT_OPENING_DEG, EP_X, EP_W, EP_H_LO, EP_H_HI, ENCL_SHELL_D, SOLAR_ARRAY_X, SOLAR_ARRAY_YD, SHELF_X_L, SHELF_X_R, SHELF_W, SHELF_H, SHELF_T, SHELF_DEPTH, SHELF_YD_NEAR, SHELF_YD_FAR, SHELF_STOW_TOP_Z, EVAP_W, EVAP_D, EVAP_H, EVAP_DUCT_X, EVAP_DUCT_Z, EVAP_DUCT_D, INVERTER_X, INVERTER_Z, INVERTER_W, INVERTER_H, INVERTER_D, FAN_BODY_D, FAN_A_YD, FAN_A_H, FAN_B_YD, FAN_B_H, DUCT_DEPTH, DUCT_HEIGHT, BV05_X, TAP_X, TAP_Z, TAP_PIPE_OD, PUMP_PIPE_OD, SPRAY_BAR_FEED_Z, PROC_TRAY_DRAIN_X, PROC_TRAY_SUMP_Z, SUMP_SUCTION_WALL_RUN_Z, PWP_FILTER_X1, PWP_FILTER_X2, PWP_FILTER_X3, PWP_FILTER_TOP_Z, PWP_FILTER_YD, PWP_P02_X, PWP_SV01_X, PWP_WAIST_Z, PWP_SV01_Z, PWP_PANEL_X0, PWP_PANEL_X1, PWP_PANEL_Z0, PWP_SROW_Z0, PWP_ACC2_X, PWP_ACC2_Z0, RWK_X_L, RWK_X_R, RWK_ARM_BOT, RWK_ARM_TOP, RWK_AH, RWK_ARM_W, RWK_BEARER_W, RWK_X_UP, RWK_J6_BOLT_ZS, RWK_J6_EP_H, RWK_RIBBON_NOTCH_YDS, PDH_PLATE_OD, PDH_RING_OD, PDH_PLATE_T, PDH_RING_T, PDH_ADAPT_OD, PDH_ADAPT_T, PDH_MOUNT_BC, PDH_MOUNT_N

from tbs_draw import *            # shared drawing/material primitives (Phase 0 extraction)


# Subsystem → tag map (also drives tag creation order).
TAGS = ["Shell", "Shell Far", "Walkways", "Processing Tray",
        "Pinhole", "Optical Cone", "Film Plane", "Combined Plate",
        "Pivot Axle", "Spray Bar", "Plumbing Panel",
        "IBC Stack", "IBC Rack", "Light Trap", "Electrical", "Shelf",
        "Light Seal", "Lighting", "Evap Cooler", "Water Hookups", "Fans",
        "Water Plumbing", "Solar Array", "Fan Wiring", "EP Ext Wiring", "Labels"]


# Major system components to call out in the "Labeled" scene.
# (component instance name, label text, leader Δx mm, leader Δz mm) — the leader is
# anchored at the component's bounds top-centre and fanned out so labels don't pile up.
# (component name, text, leader Δx, Δy, Δz mm). Δy pulls the label OUT of a wall
# toward the viewer (the camera looks from the −Y / pinhole-wall side).
OVERVIEW_LABELS = [
    ("Pinhole Assembly",      "PINHOLE  Ø2.17mm",                 -140, -1120,  630),
    ("Processing Tray",       "PROCESSING TRAY",                  -250,     0,  650),
    ("Corridor Equipment",    "CORRIDOR PLUMBING PANEL",          520,     0,  820),
    ("IBC Stack",             "IBC WATER STORAGE\n4x tote",        600,     0, 1300),
    ("Light-Trap Drum",       "LIGHT-TRAP DRUM\n(entry)",         -650,     0, 1050),
    ("Electrical",            "ELECTRICAL PANEL",                  500,     0,  560),
    ("Evap Cooler & Duct",    "EVAP COOLER",                       300,     0, 1700),
    # rev13: the fold-down shelf lost its ceiling hanger rods, so a bounds-top anchor
    # now lands on the shelf assembly (not the roof) — anchor on the component so the
    # leader TRACKS the shelf wherever it's positioned (was a stale explicit point).
    ("Chemistry Shelf",       "CHEMISTRY SHELF",                  -200,  -850,  700),
]
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
