alvinr/tbs/src/models/generate_construction_model.py

#!/usr/bin/env python3
# SPDX-License-Identifier: AGPL-3.0-only
# © 2026 Alvin Richards
"""Generate the TBS-001 phased CONSTRUCTION model (logical model: construction).

Validates the BUILD ORDER (see construction-report.md). REUSES the Overview component
builders (generate_sketchup_model.py + corridor/pinhole water panels + walkway model) —
each build STEP is drawn on its own tag, and one SCENE per PHASE shows the model built up
CUMULATIVELY through that phase. Stepping the scenes 1→5 walks the install; toggling a
phase's step-tags on in order shows each step drop in.

v1 granularity note: several Overview builders draw more than one report-step's worth of
geometry and don't (yet) take a per-wall/subset argument (e.g. `ibc_stack()` draws all four
totes; `walkway_brackets()` draws near+far together; `film_plane_mechanism()` draws the rails
AND the moving plane). Where that happens the affected report-steps are GROUPED onto one
step-tag (noted in STEPS). Finer per-step splitting + the click-to-build Dynamic Component are
the next iteration.

Phase 2 (re-measure) adds no geometry — its scene shows the Phase-1 state (what you measure).

Usage:
    python3 src/models/generate_construction_model.py --save         # write construction.rb
    python3 src/models/generate_construction_model.py --save --send  # + send to the ACTIVE doc

NOTE: --send clears the ACTIVE SketchUp document. Open a NEW blank doc before sending, then
save the result as models/construction.skp.
"""
import argparse
import os
import sys
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
